newaetech/chipwhisperer-target-cw308t/CW308T_ICE405/README.md

## CE308T-ICE40 Prototype Target

This target was used for internal development.
