newaetech/chipwhisperer-target-cw308t/CW308T_NU8051_AT20/kicad_src/README.md

# N76e003 UFO Target board for the Chipwhisper UFO board

Tested and working, gerbers, BOM, and placement files are in `jlcpcb/`
