newaetech/chipwhisperer-target-cw308t/CW308T_STM32F_SOCKET/gerbers/README.txt

2-Layer PCB

Soldermask: Blue
Silkscreen: White

Finish: Immersion Gold

52.3mm x 64.6mm

Board Files:

 .GTO - Top Silkscreen
 .GTS - Top Soldermask
 .GTL - Top Copper
 .GBL - Bottom Copper
 .GBS - Bottom Soldermask
 .GBO - Bottom Silkscreen
 .GM1 - Board Outline
 .NCDRILL - Drill File

Other Files:

 .GTP - Top Paste (not used - no SMD on top)
 .GBP - Bottom Paste (for stencil)
