newaetech/chipwhisperer-target-cw308t/CW308T_IMXRT1062/gerbers/README.txt

2-Layer PCB

Soldermask: Blue
Silkscreen: White

Finish: ENIG

Individual PCB Size: 52.3mm x 64.6mm

Board Files:

 .GTO - Top Silkscreen
 .GTS - Top Soldermask
 .GTL - Top Copper
 .GBL - Bottom Copper
 .GBS - Bottom Soldermask
 .GBO - Bottom Silkscreen
 .GM1 - PCB Outline
 .NCDRILL - Drill Files

Other Files:

 .GTP - Top Paste (used for stencil)
 .GBP - Bottom Paste (NOT USED)
