newaetech/chipwhisperer-target-cw308t/CW308T_NRF52840/gerbers/README.txt

2-Layer PCB

Soldermask: Blue
Silkscreen: White

Finish: Immersion Gold

Individual PCB Size: 52.3mm x 64.6mm

Trace/Space: 5 mil
Min Drill:   0.3 mm

Board Files:

 .GTO - Top Silkscreen
 .GTS - Top Soldermask
 .GTL - Top Copper
 .GBL - Bottom Copper
 .GBS - Bottom Soldermask
 .GBO - Bottom Silkscreen
 .GM1 - Outline
 .NCDRILL - Drill Files

Other Files:

 .GTP - Top Paste (used for stencil)
 .GBP - Bottom Paste (NOT USED)
