newaetech/chipwhisperer-target-cw308t/CW308T_LPC1343F/gerbers/02/README.txt

2-Layer PCB

Soldermask: Blue
Silkscreen: White

Finish: Immersion Gold

PCB Size: 52.3mm x 64.6mm

Board Files:

 .GTO - Top Silkscreen
 .GTS - Top Soldermask
 .GTL - Top Copper
 .GBL - Bottom Copper
 .GBS - Bottom Soldermask
 .GBO - Bottom Silkscreen
 .GM1 - Outline
 .NCDRILL - Drill File (ROUND & SLOTS IN SEPERATE FILES)

Other Files:

 .GTP - Top Paste (used for stencil)
 .GBP - Bottom Paste (NOT USED)
