newaetech/chipwhisperer-target-cw308t/CW308T_STM32F4_CSP/gerbers/SINGLE_03/README.txt

2-Layer PCB

Soldermask: Blue
Silkscreen: White

4 mil trace/space

Finish: Immersion Gold

54.6mm x 65.7mm

Board Files:

 .GTO - Top Silkscreen
 .GTS - Top Soldermask
 .GTL - Top Copper
 .GBL - Bottom Copper
 .GBS - Bottom Soldermask
 .GBO - Bottom Silkscreen
 .GM1 - Board Outline
 .NCDRILL - Drill File

Other Files:

 .GTP - Top Paste (for stencil)
 .GBP - Bottom Paste (for stencil)
