newaetech/chipwhisperer-target-cw308t/CW308T_AVR/altium_src/gerbers/README.txt

2-Layer PCB

Soldermask: Blue
Silkscreen: White

Finish: RoHS HASL

52.3mm x 68.1mm

Board Files:

 .GTO - Top Silkscreen
 .GTS - Top Soldermask
 .GTL - Top Copper
 .GBL - Bottom Copper
 .GBS - Bottom Soldermask
 .GBO - Bottom Silkscreen
 .GM3 - Board Outline
 .NCDRILL - Drill File

Other Files:

 .GTP - Top Paste (for stencil)
 .GBP - Bottom Paste (for stencil)
