newaetech/chipwhisperer-target-cw308t/CW312T_ATSAM4S/altium_src/RELEASE/gerbers/README.txt

GENERAL
----------
Board Size: 58.7 mm x 53.7 mm
Finish: Immersion Gold
Soldermask: Blue
Silkscreen: White
Board Thickness: 1.6mm

Min drill = 0.3mm
Space/Trace = 6mil

PCB STACKUP:
--------------------------------
 .GTO Top Silkcreen
 .GTS Top Soldermask
 .GTL TOP COPPER               (LAYER 1)
 .GBL BOTTOM COPPER            (LAYER 2)
 .GTS Bottom Soldermask 
 .GBO Bottom Silkscreen

ADDITIONAL FILES:
--------------------------------
 .NCDRILL - NC Drill
 .GTP Top Stencil
 .GBP Bottom Stencil
 .GM1 Milling Layer

BOARD CONSTRUCTION
--------------------------------
Standard board stackup spacing for 2-layer 0.062" PCB
