newaetech/chipwhisperer-target-cw308t/CW308T_ATSAMR21/Images/atsamr21-sch.png

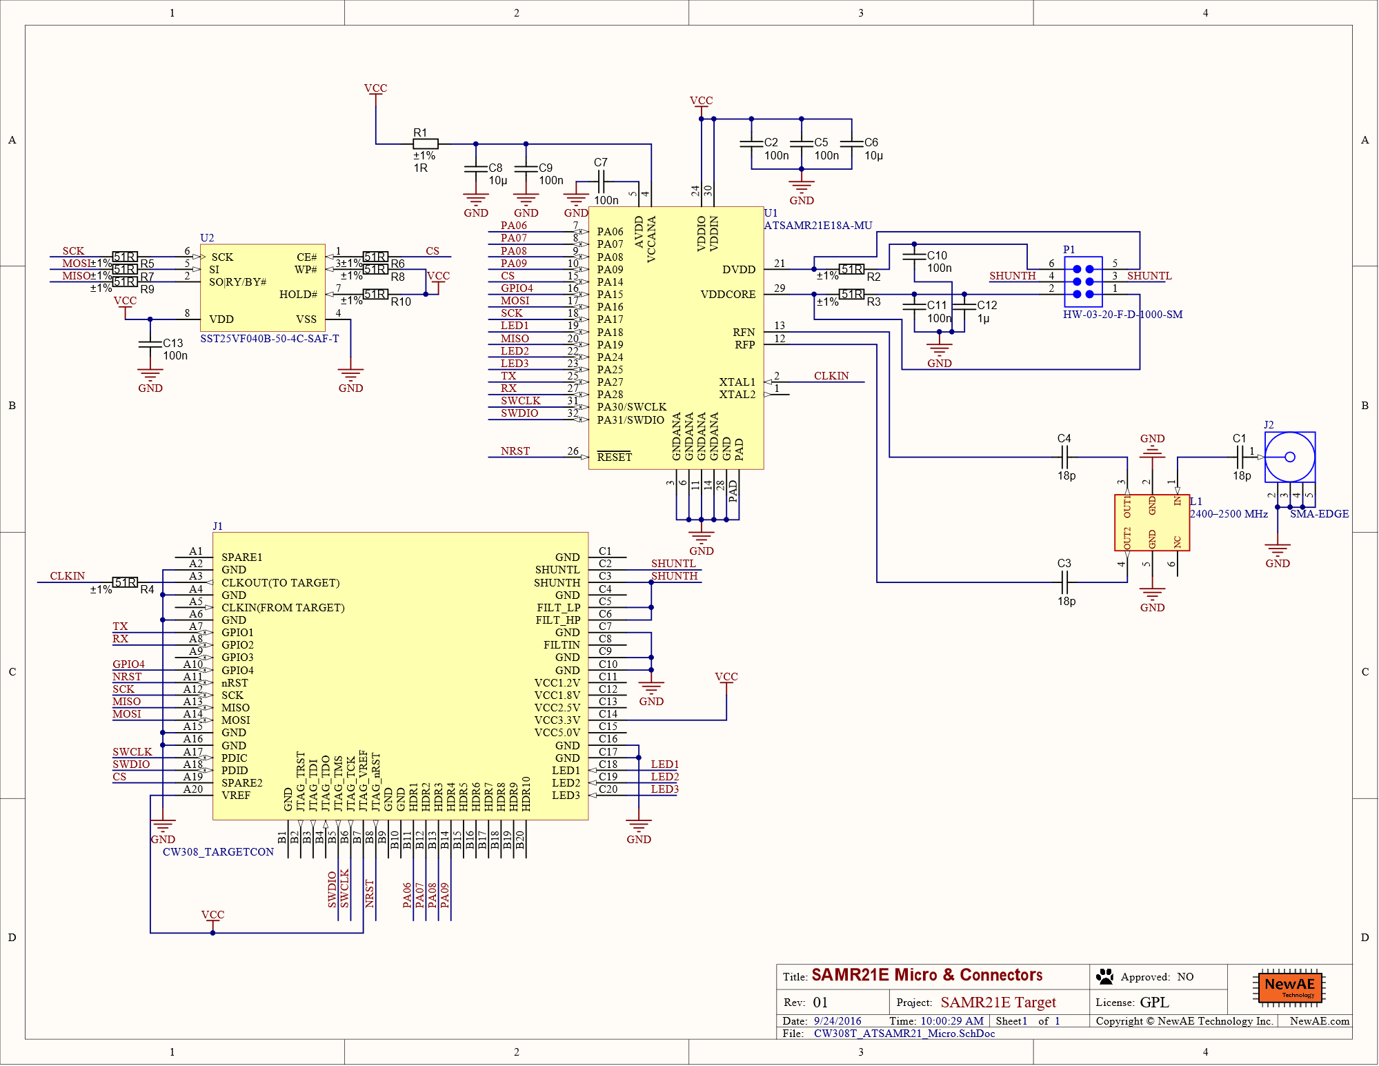
CW308T_ATSAMR21/Images/atsamr21-sch.png
