newaetech/chipwhisperer-target-cw308t/CW308T_Si4010/altium_src/matching_values.png

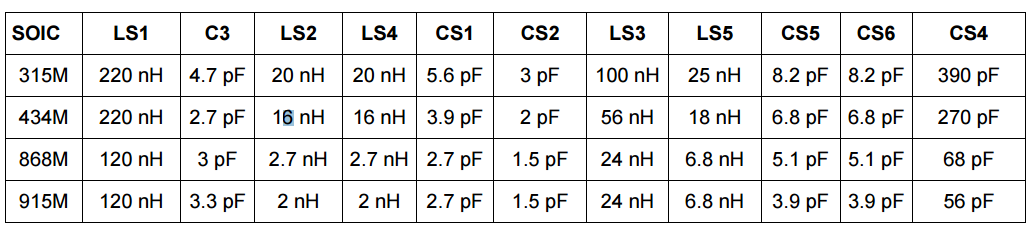
CW308T_Si4010/altium_src/matching_values.png
