newaetech/chipwhisperer-target-cw308t/CW308T_S6LX9/altium_src/PANEL_ORDER/README.txt

GENERAL
----------
Panel Size: 138.78 mm x 114.27 mm
Board Size: 52.3 mm x 64.6 mm
Finish: Immersion Gold
Soldermask: Blue
Silkscreen: White
Board Thickness: 1.6mm

Min drill = 0.3mm
Space/Trace = 6mil

PCB STACKUP:
--------------------------------
 .GTO Top Silkcreen
 .GTS Top Soldermask
 .GTL TOP COPPER               (LAYER 1)
 .GP1 INNER PLANE 1 (NEGATIVE) (LAYER 2)
 .GP2 INNER PLANE 2 (NEGATIVE) (LAYER 3)
 .GBL BOTTOM COPPER            (LAYER 4)
 .GTS Bottom Soldermask
 .GBO Bottom Silkscreen

ADDITIONAL FILES:
--------------------------------
 .NCDRILL - NC Drill
 .GTP Top Stencil
 .GBP Bottom Stencil
 .GM25 - Panel Outline
 .GM18 - VSCORE for Panel

BOARD CONSTRUCTION
--------------------------------
Standard board stackup spacing for 4-layer 0.062" PCB ok

E-TEST
------

PCBs must be 100% electrically tested.
