newaetech/chipwhisperer-target-cw308t/CW308T_87C51/altium_src/RELEASE/-02/NAE-CW308T-87C51 Build Notes.pdf

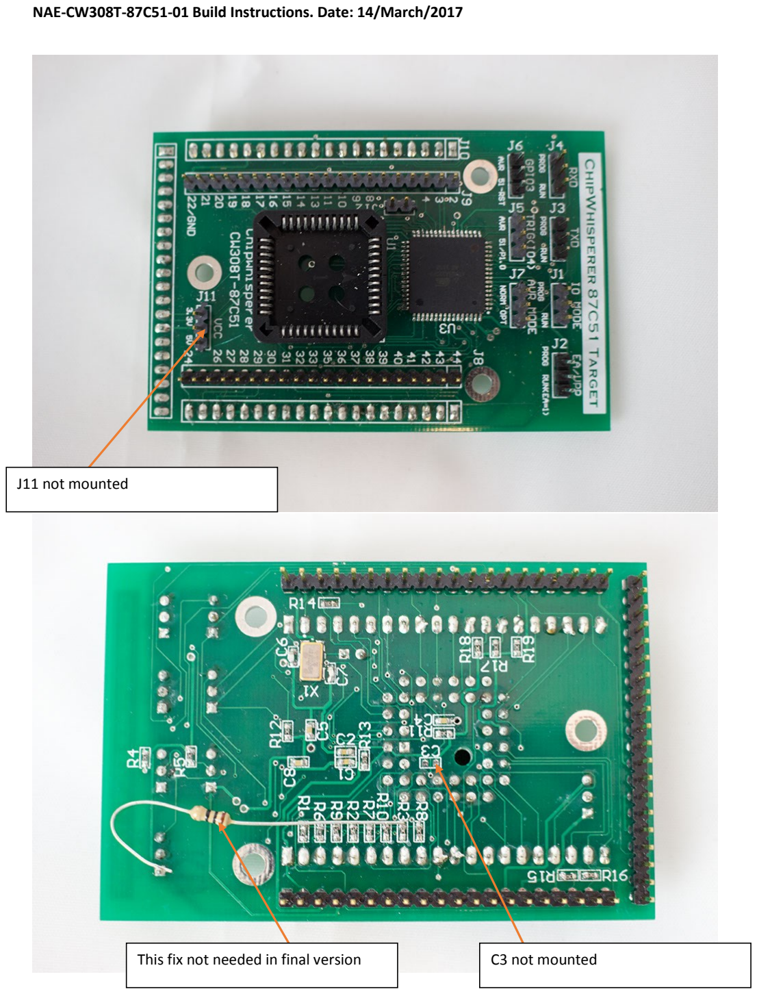
[picture p116: page 1]

NAE-CW308T-87C51-01 Build Instructions. Date: 14/March/2017

J11 not mounted

This fix not needed in final version | C3 not mounted
