newaetech/chipwhisperer-target-cw308t/CW308T_S6LX9/NAE-CW308T-S6LX9_Schematic.PDF

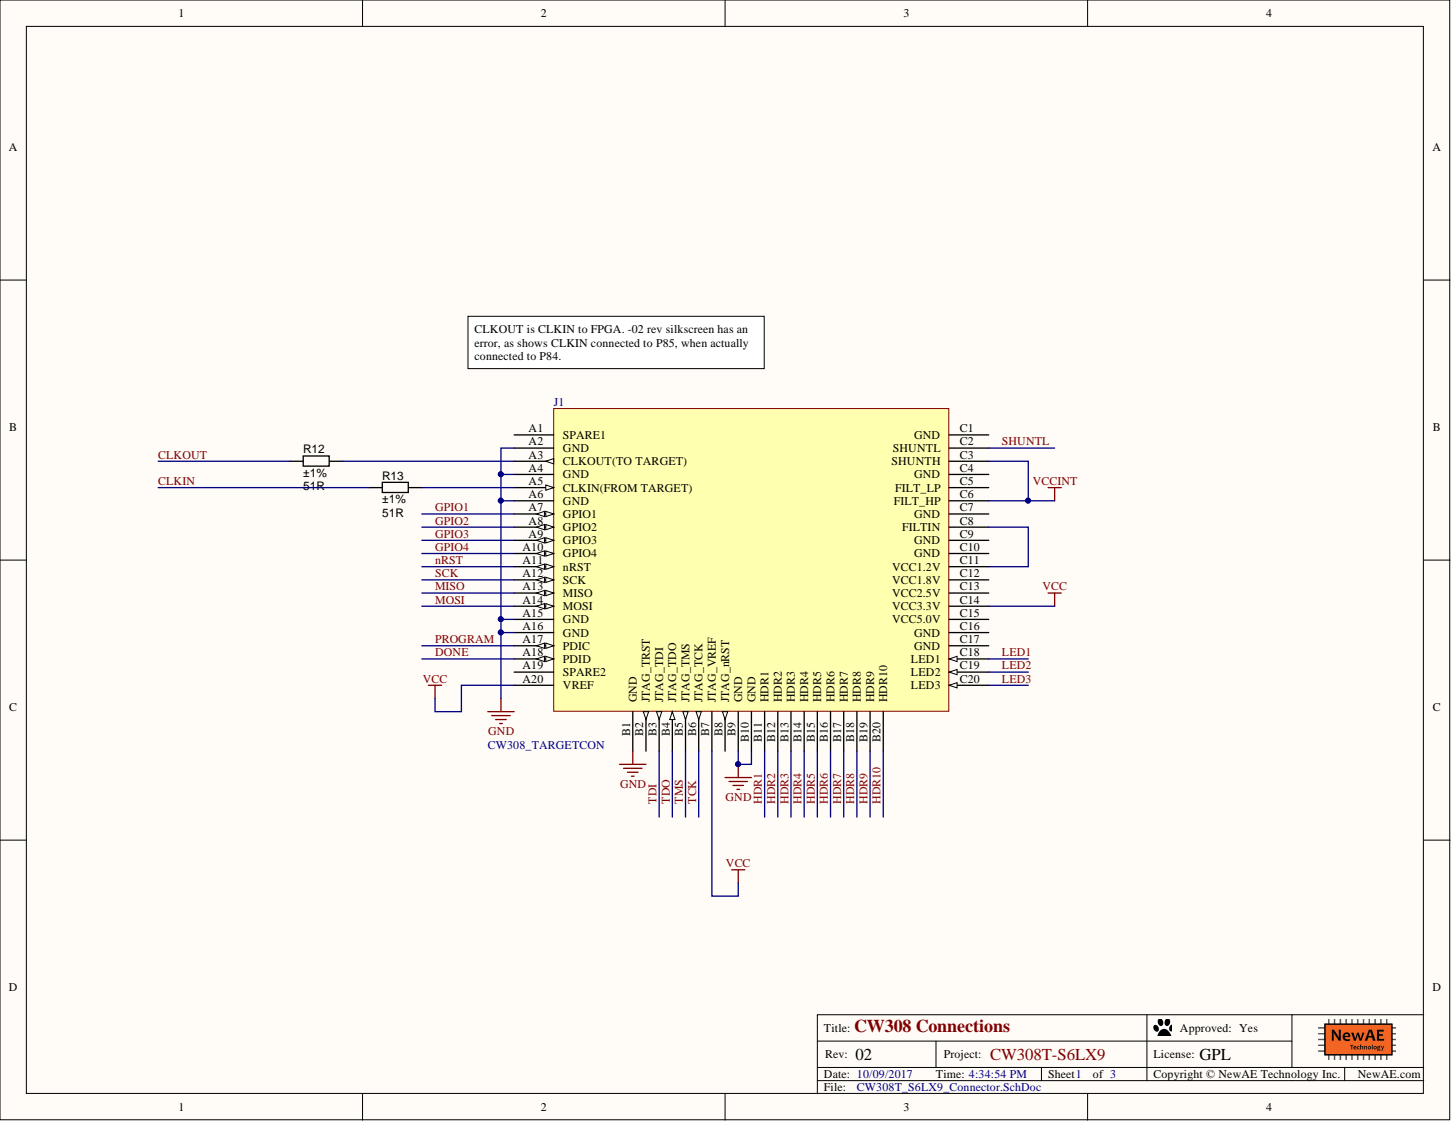
[picture p130: page 1]

CLKOUT is CLKIN to FPGA. -02 rev silkscreen has an
error, as shows CLKIN connected to P85, when actually
connected to P84.

CW308 Connections Title: | Approved: Yes

Rev: 02 | Project: CW308T-S6LX9 | License: GPL

Date: 10/09/2017 Time: 4:34:54 PM | Sheet 1 of 3

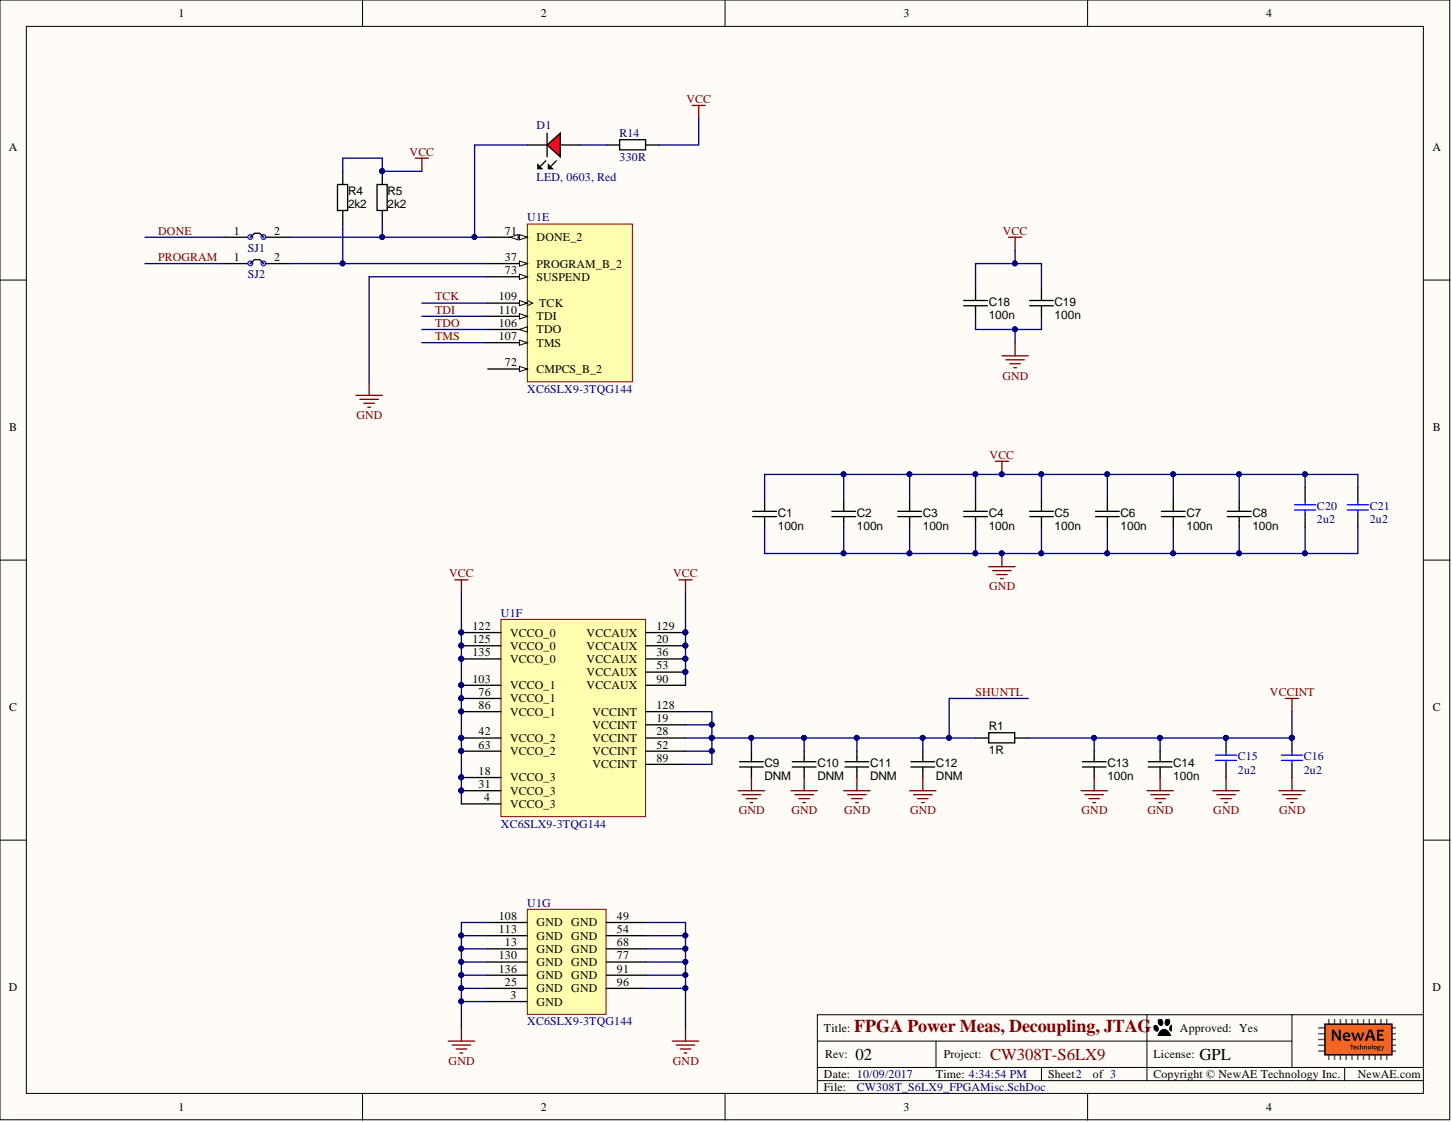
[picture p131: page 2]

FPGA Power Meas, Decoupling, JTAG Title: | Approved: Yes

Rev: 02 | Project: CW308T-S6LX9 | License: GPL

10/09/2017 Time: 4:34:54 PM | Sheet 2 of 3

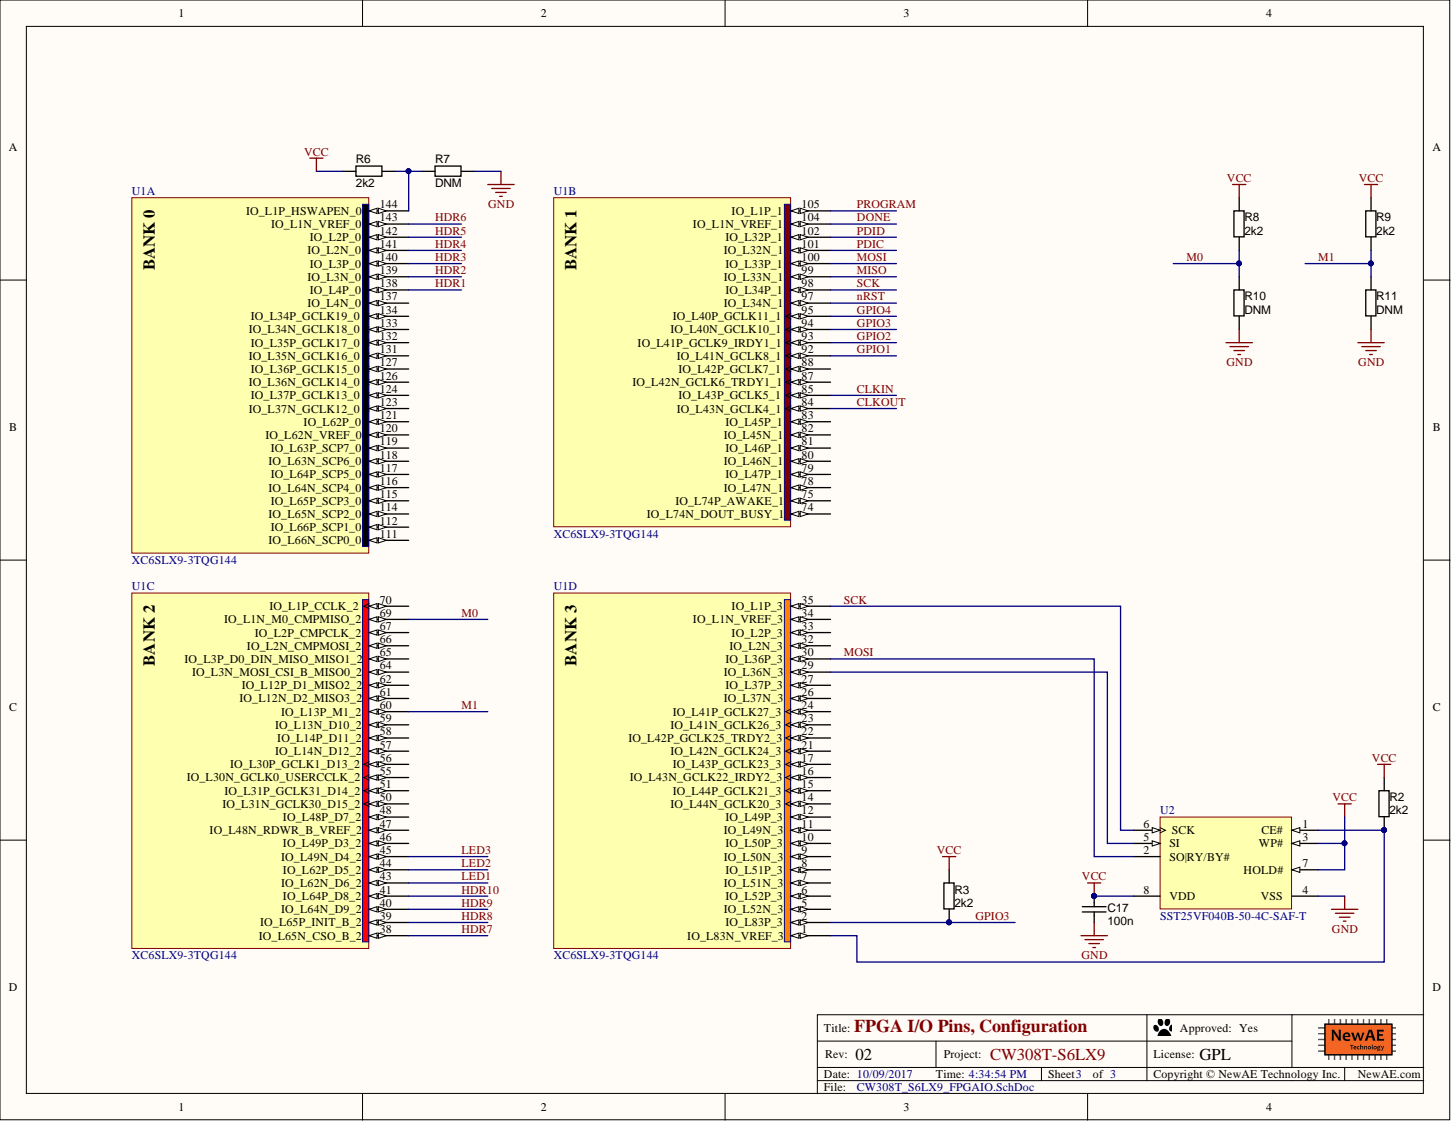
[picture p132: page 3]

9 | VCC | 2 | | 7

FPGA I/O Pins, C onfiguratio n T i t le: | A p pro ved : Yes

Rev : 02 | Project : CW308T-S6LX | L icen se: GPL

/ / T ime: : : 4 PM | Sheet o f | Co p yri g h t © New A E Tech n | o l o g y Inc.
