newaetech/chipwhisperer-target-cw308t/CW312T_RP2350/RP2350_CW312_REV02.PDF

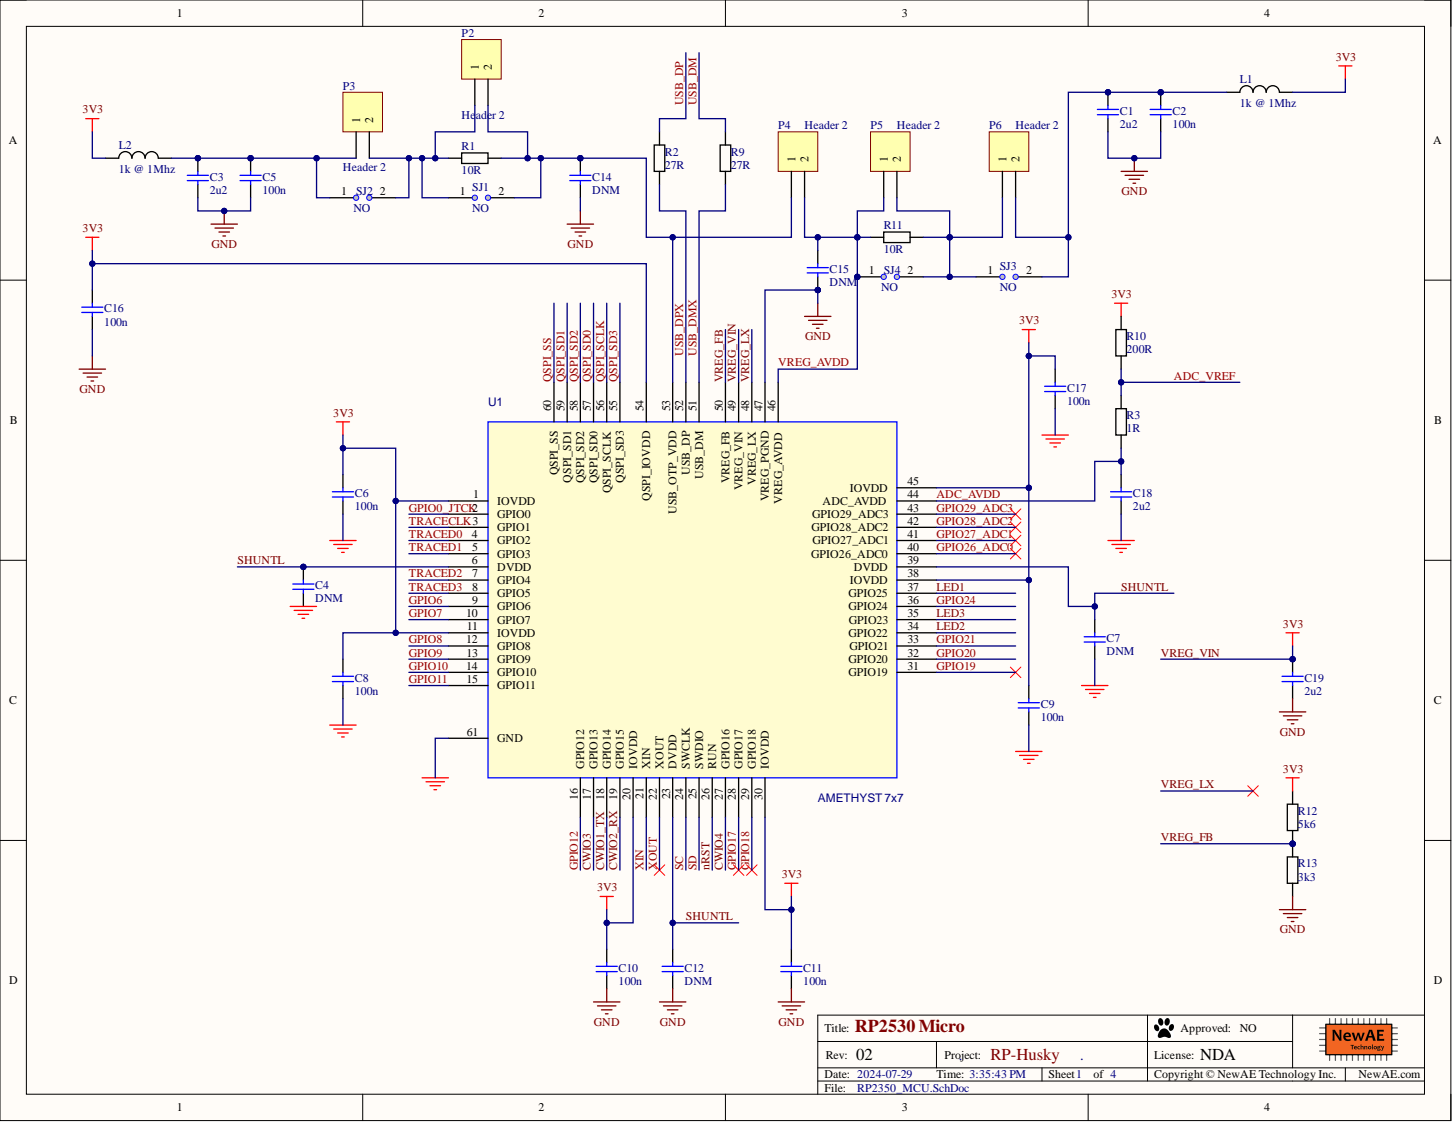
[picture p133: page 1]

ADC_AVDD

GPIO0_JTCK | GPIO0 2 | GPIO29_ADC3

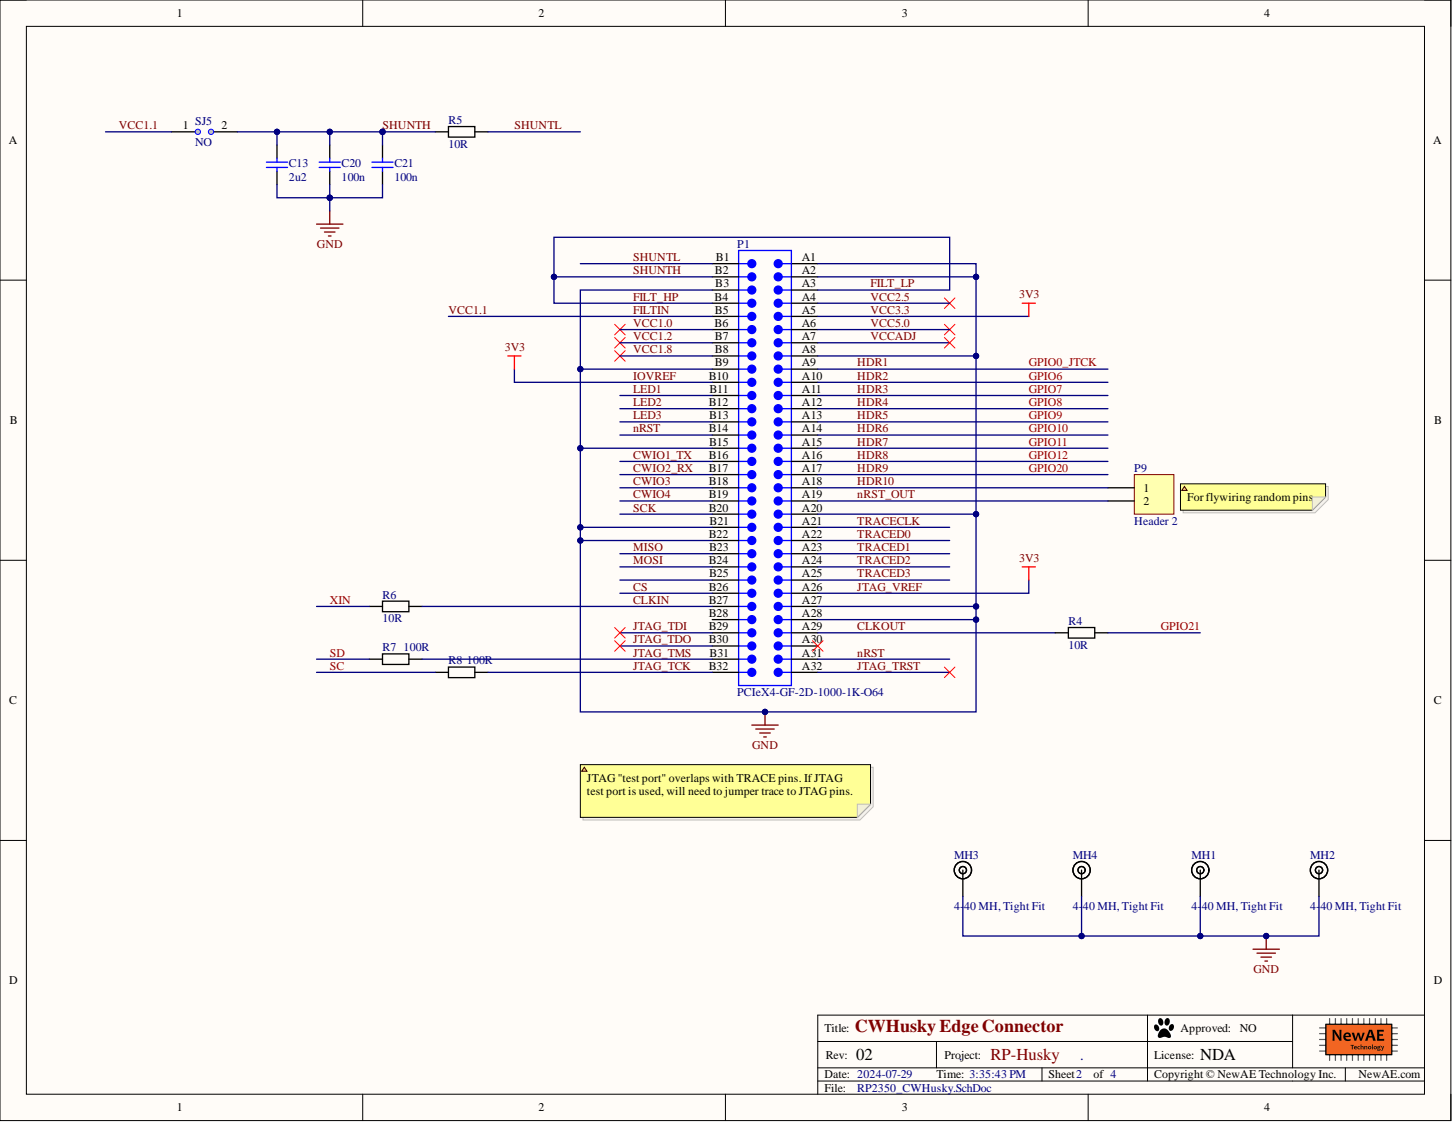
[picture p134: page 2]

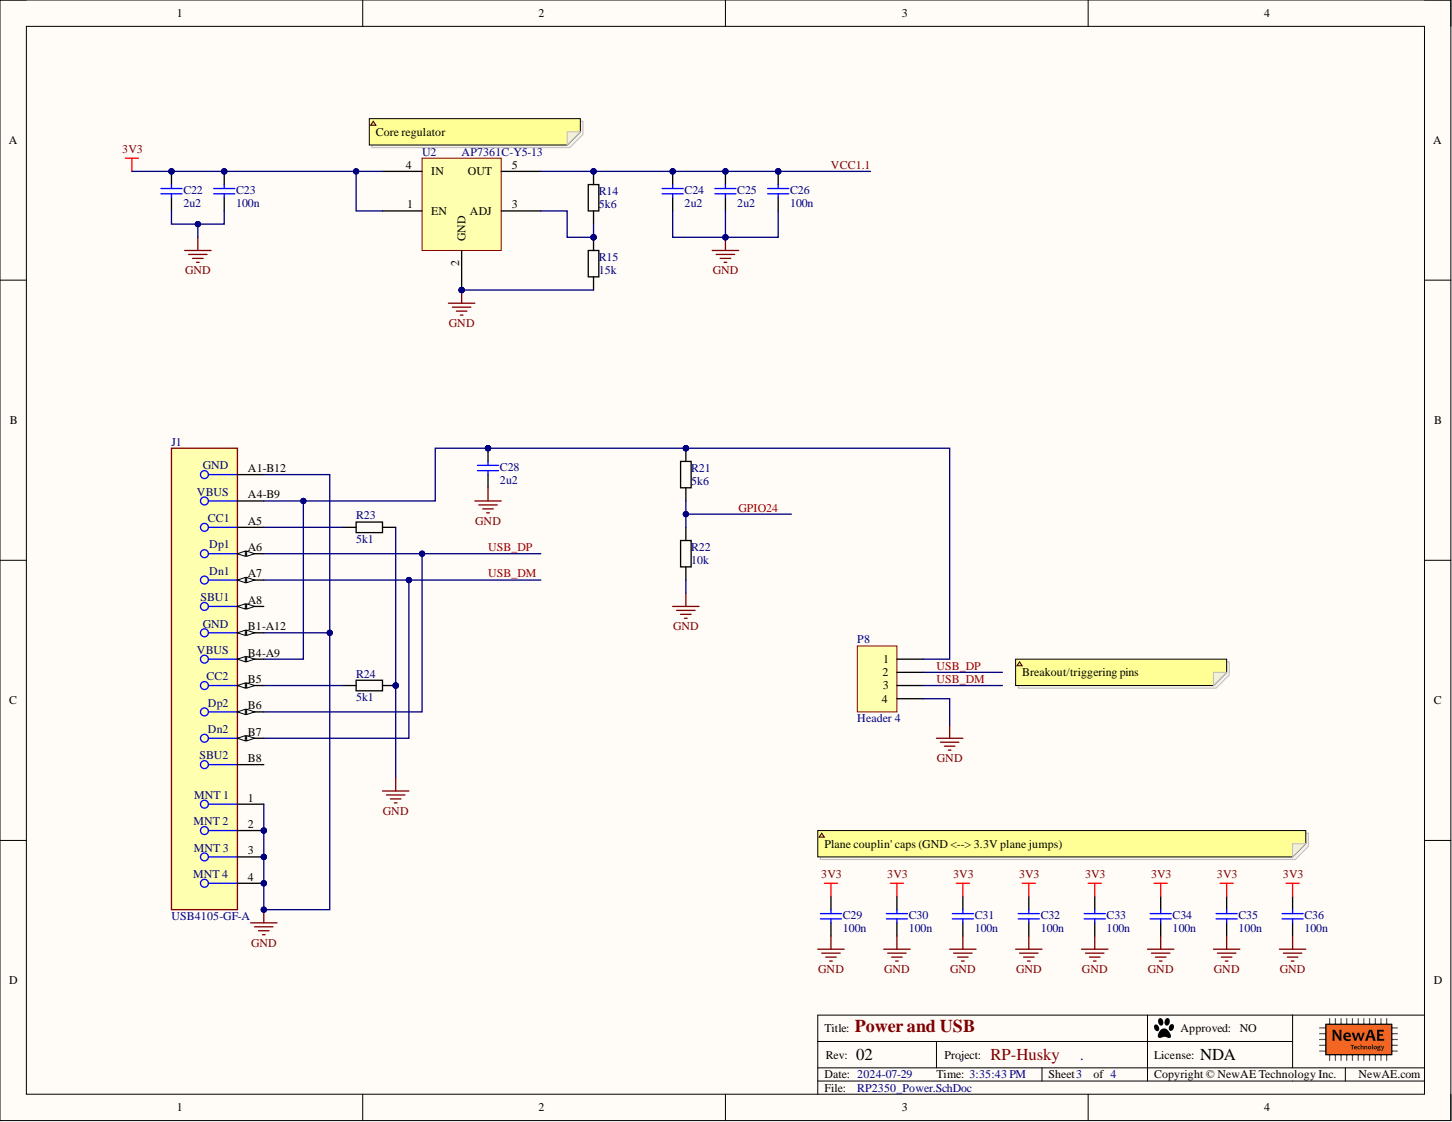
[picture p135: page 3]

Plane couplin' caps (GND <--> 3.3V plane jumps)

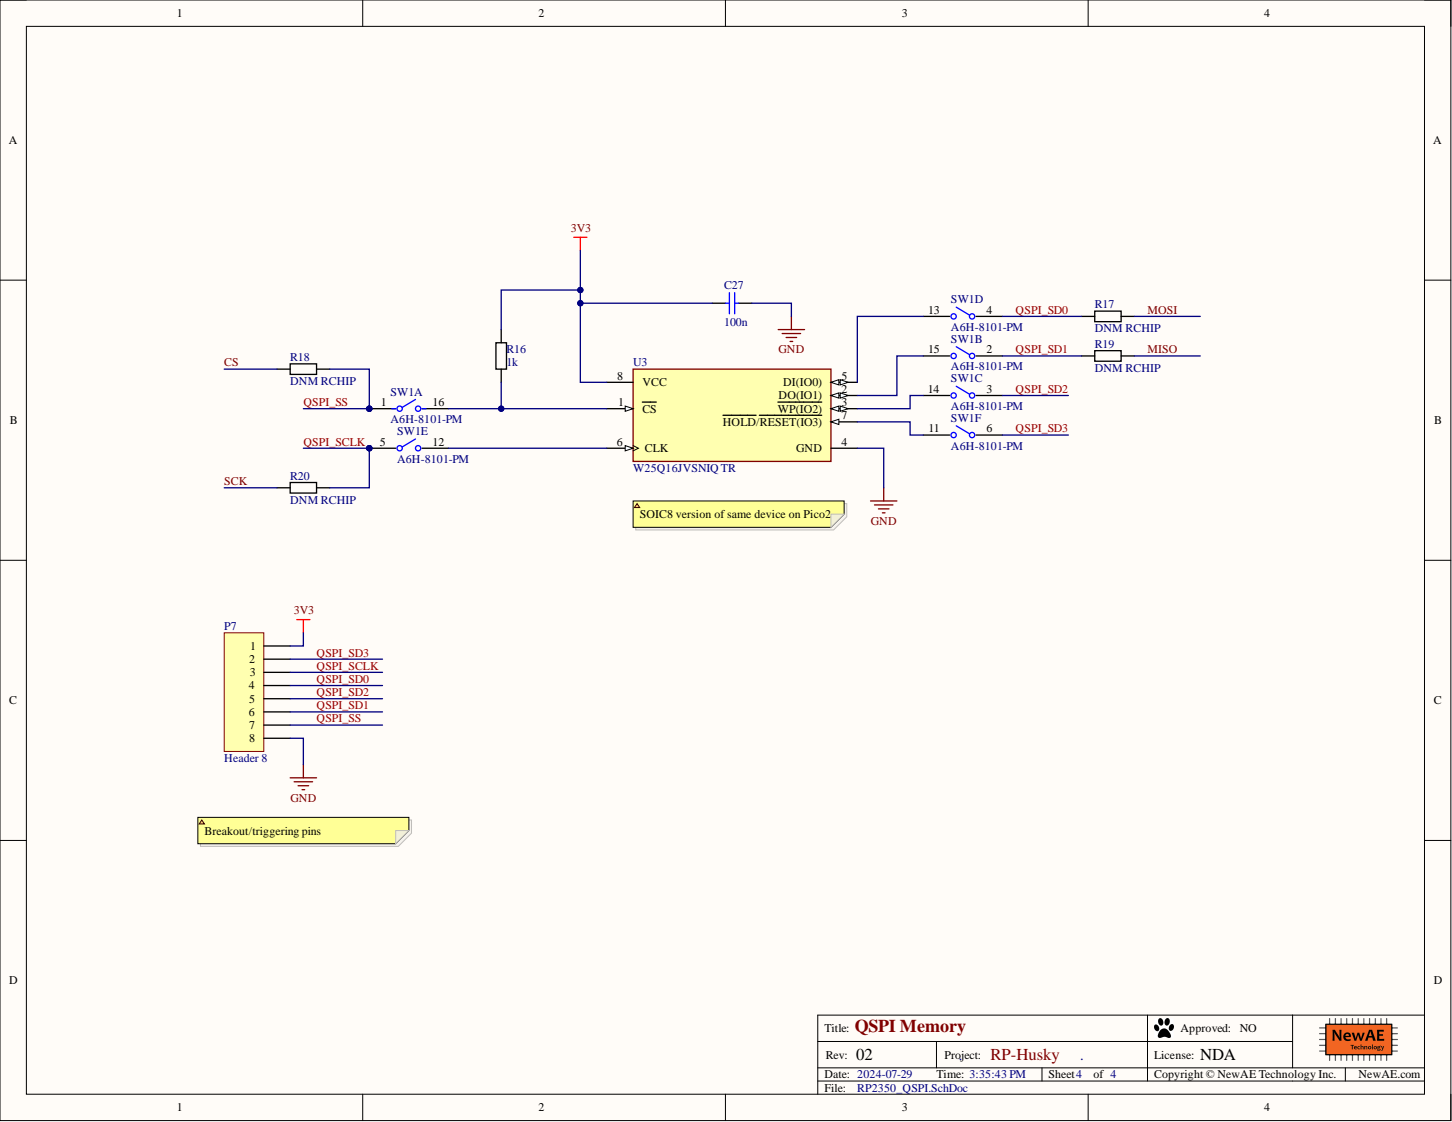
[picture p136: page 4]

SOIC8 version of same device on Pico2
