newaetech/chipwhisperer-target-cw308t/CW308T_STM32F_SOCKET/NAE_CW308T_STM32F_SOCKET.PDF

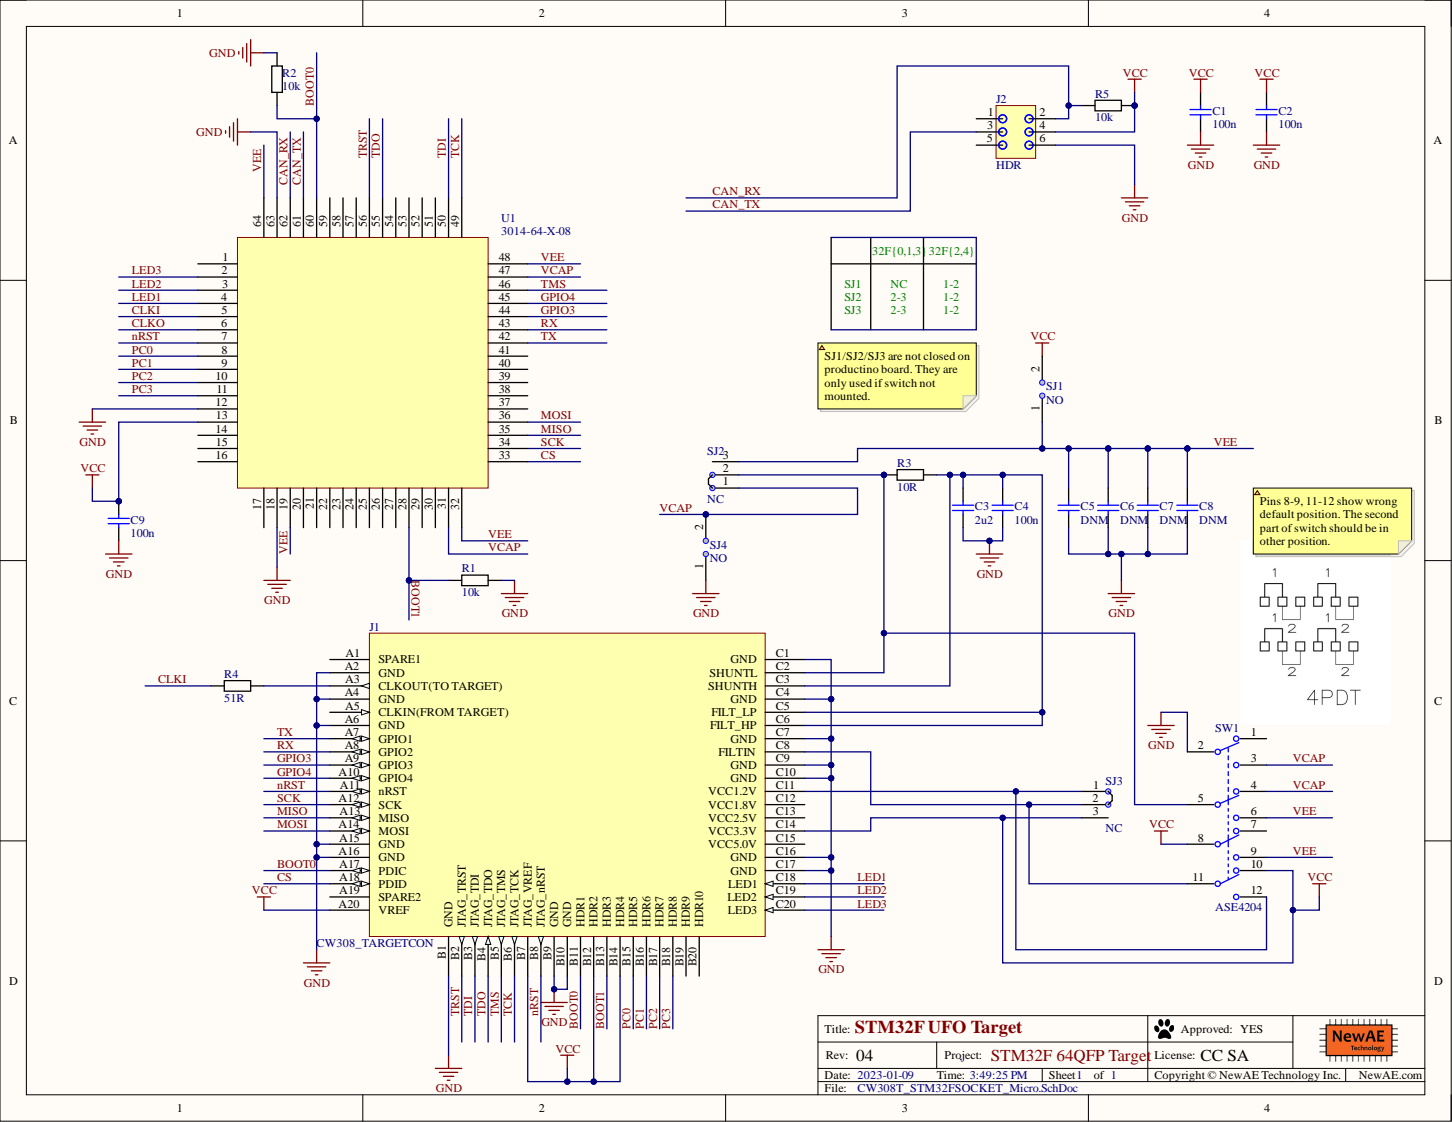
[picture p137: page 1]

SJ1/SJ2/SJ3 are not closed on
productino board. They are
only used if switch not
mounted.

15 | 34 SCK
16 | 33 CS

Pins 8-9, 11-12 show wrong
default position. The second
part of switch should be in
other position.

VEE
