newaetech/chipwhisperer-target-cw308t/CW308T_ICE405/CW308T-ICE40-PROTO.PDF

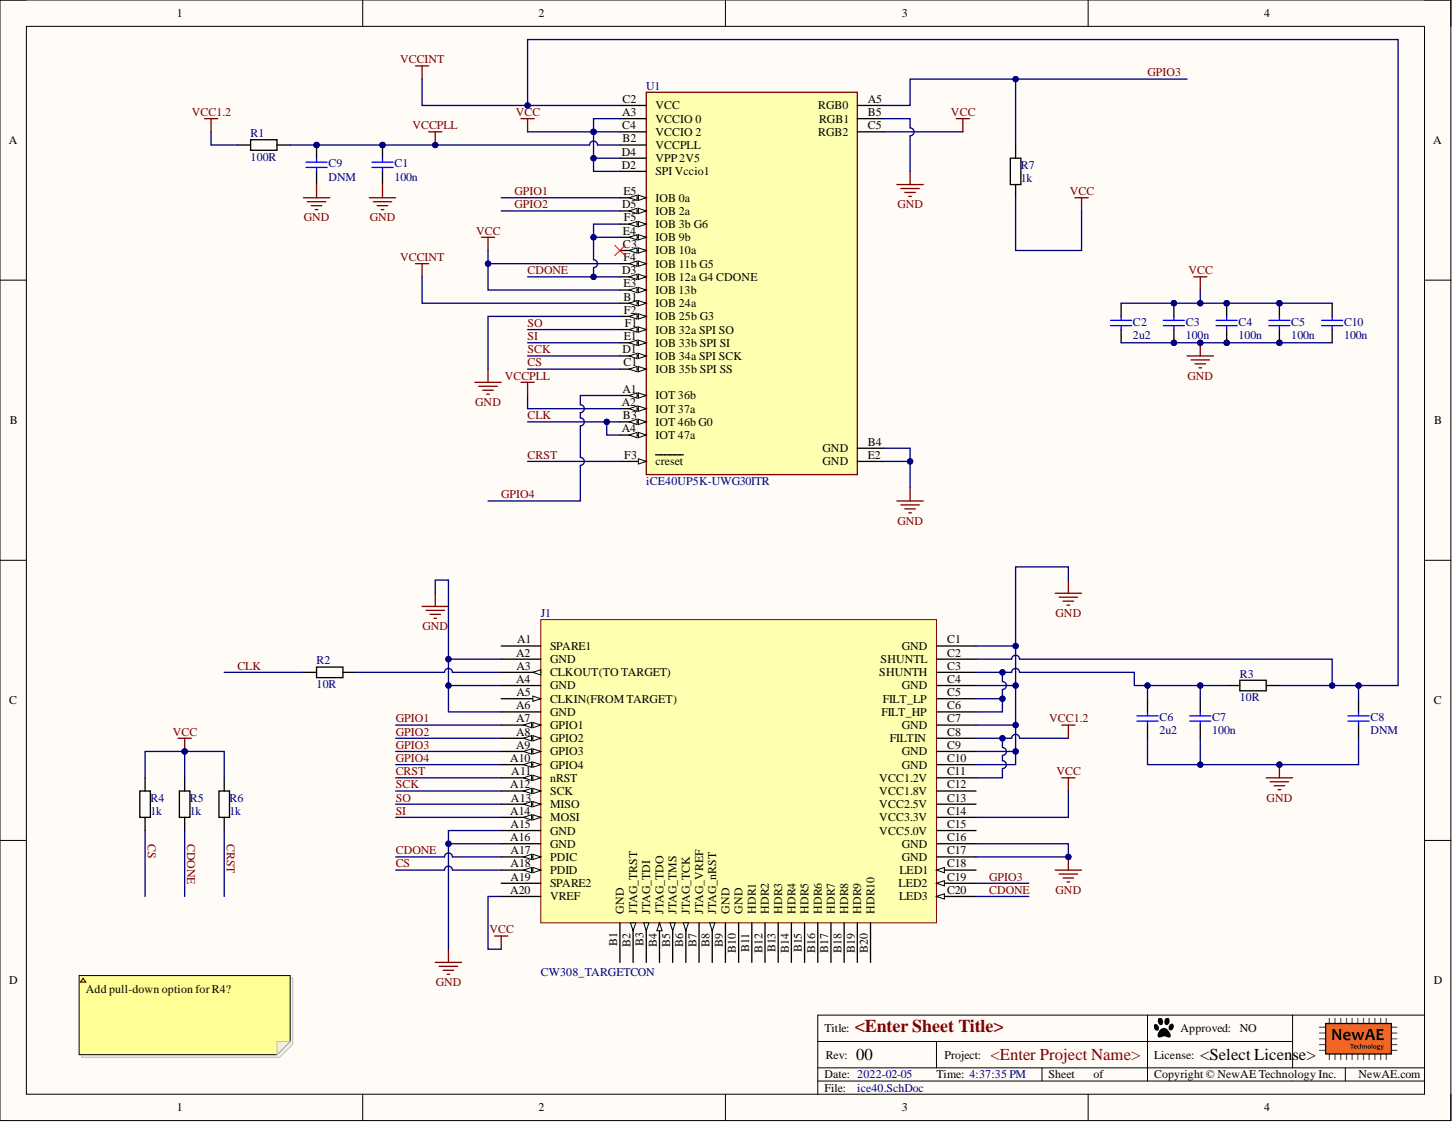
[picture p138: page 1]

VCCIO 0 A3 | VCC
VCCIO 2 C4
VCCPLL B2
SPI Vccio1 D2 VPP 2V5 D4

IOB 9b E4
IOB 10a C3
IOB 11b G5 F4

CDONE | | IOB 12a G4 CDONE D3

IOB 13b E3

PDIC A17

SPARE2 A19

Add pull-down option for R4?
