newaetech/chipwhisperer-target-cw308t/CW308T_STM32F4_CSP/NAE-CW308T-STM32F415WLCSP_03.PDF

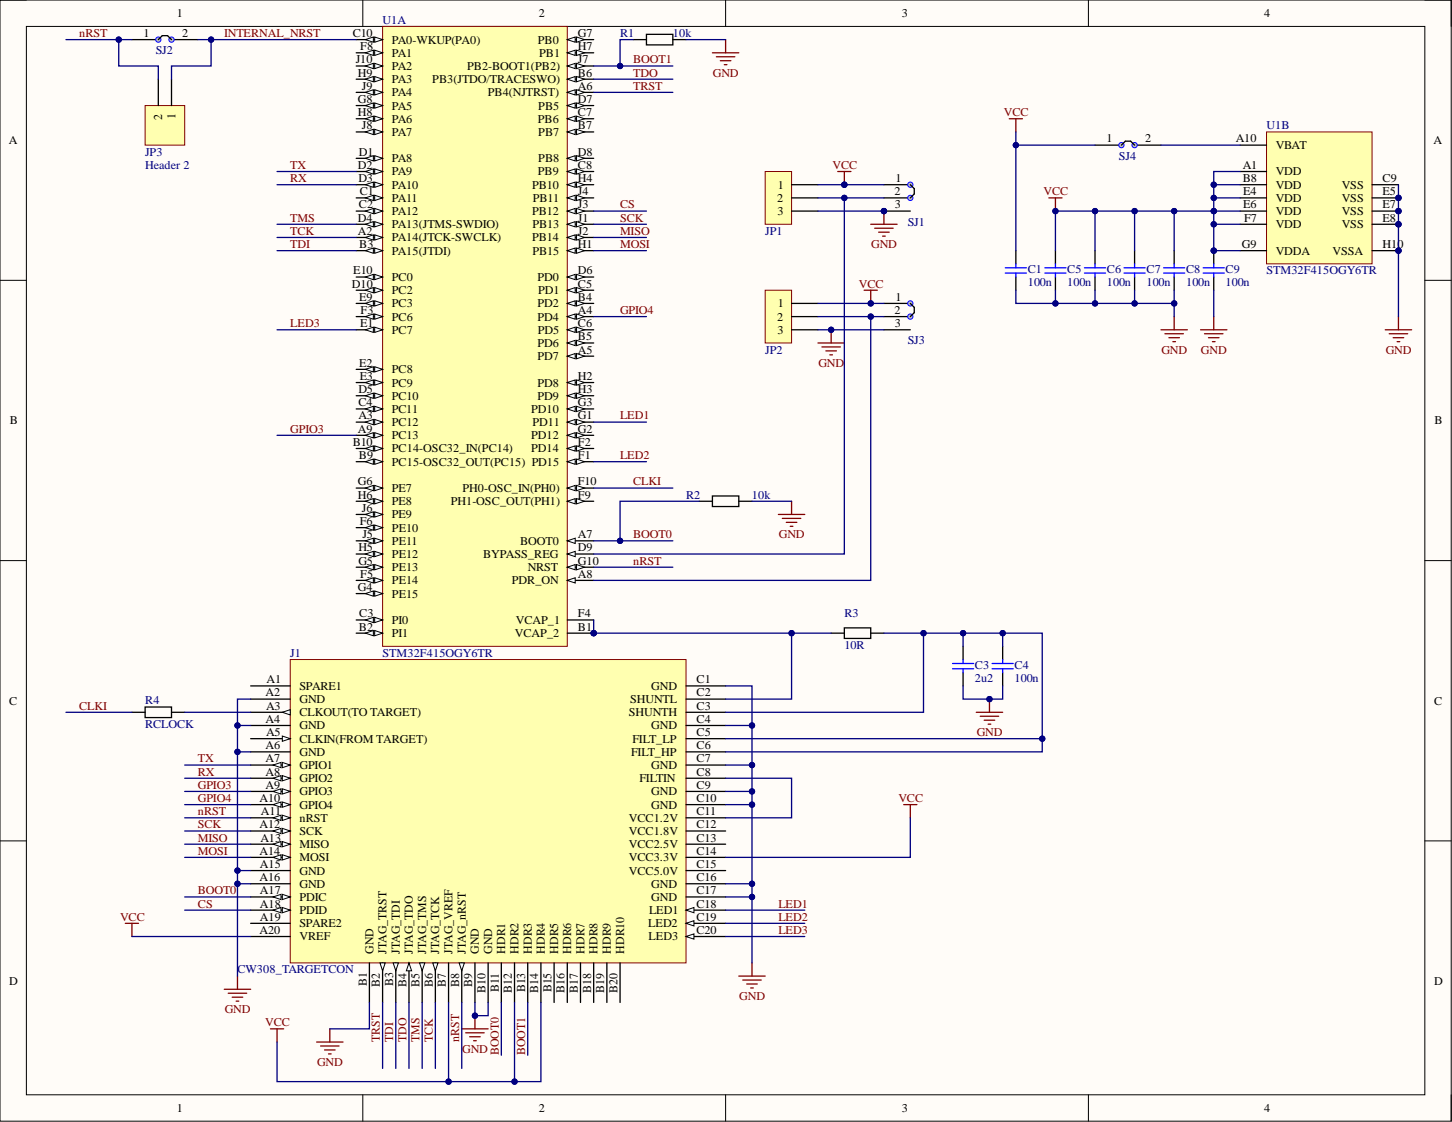
[picture p139: page 1]

PA14(JTCK-SWCLK) A2 | MISO JP1
PA15(JTDI) B3 | MOSI

LED1 | 3 | 3

PC8 E2 PC9 E3 PC11 C4 PC12 A3 PC13 A9 | | GND
