newaetech/chipwhisperer-target-cw308t/CW308T_STM32F/CW308T_STM32F_03.PDF

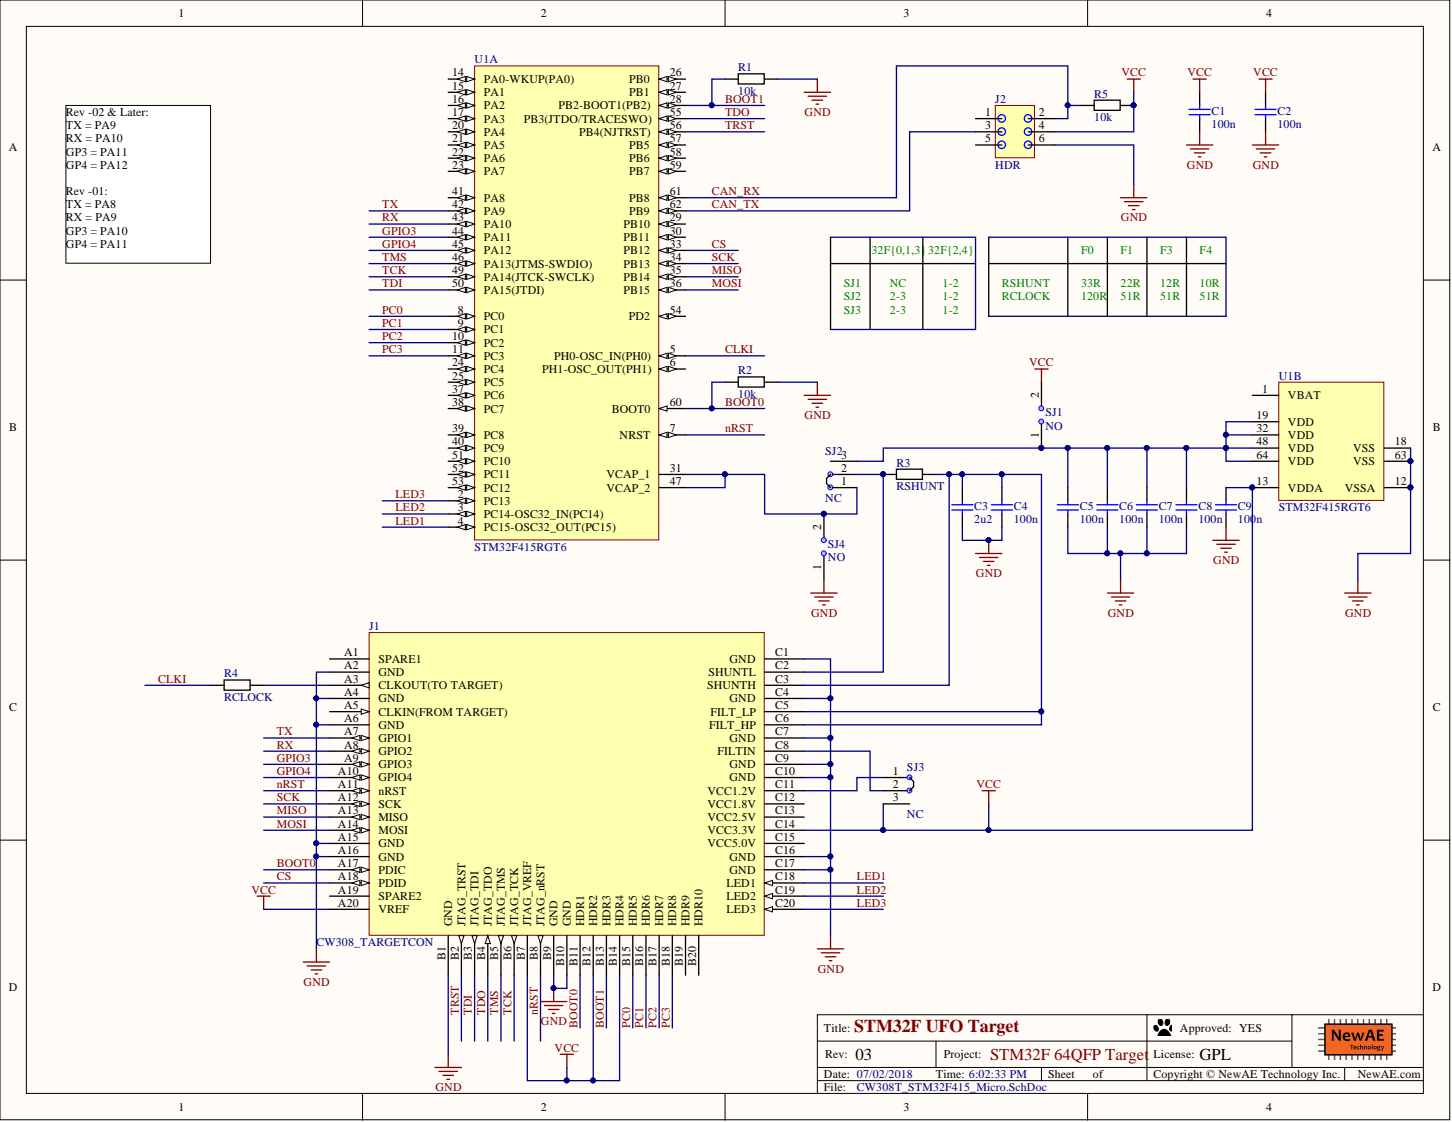
[picture p140: page 1]

STM32F UFO Target Title: | Approved: YES

Rev: 03 | Project: STM32F 64QFP Target License: GPL

Date: 07/02/2018 Time: 6:02:33 PM | Sheet of
