newaetech/chipwhisperer-target-cw308t/CW308T_ADuCM3029/NAE-CW308T-ADuCM3029_Schematic.PDF

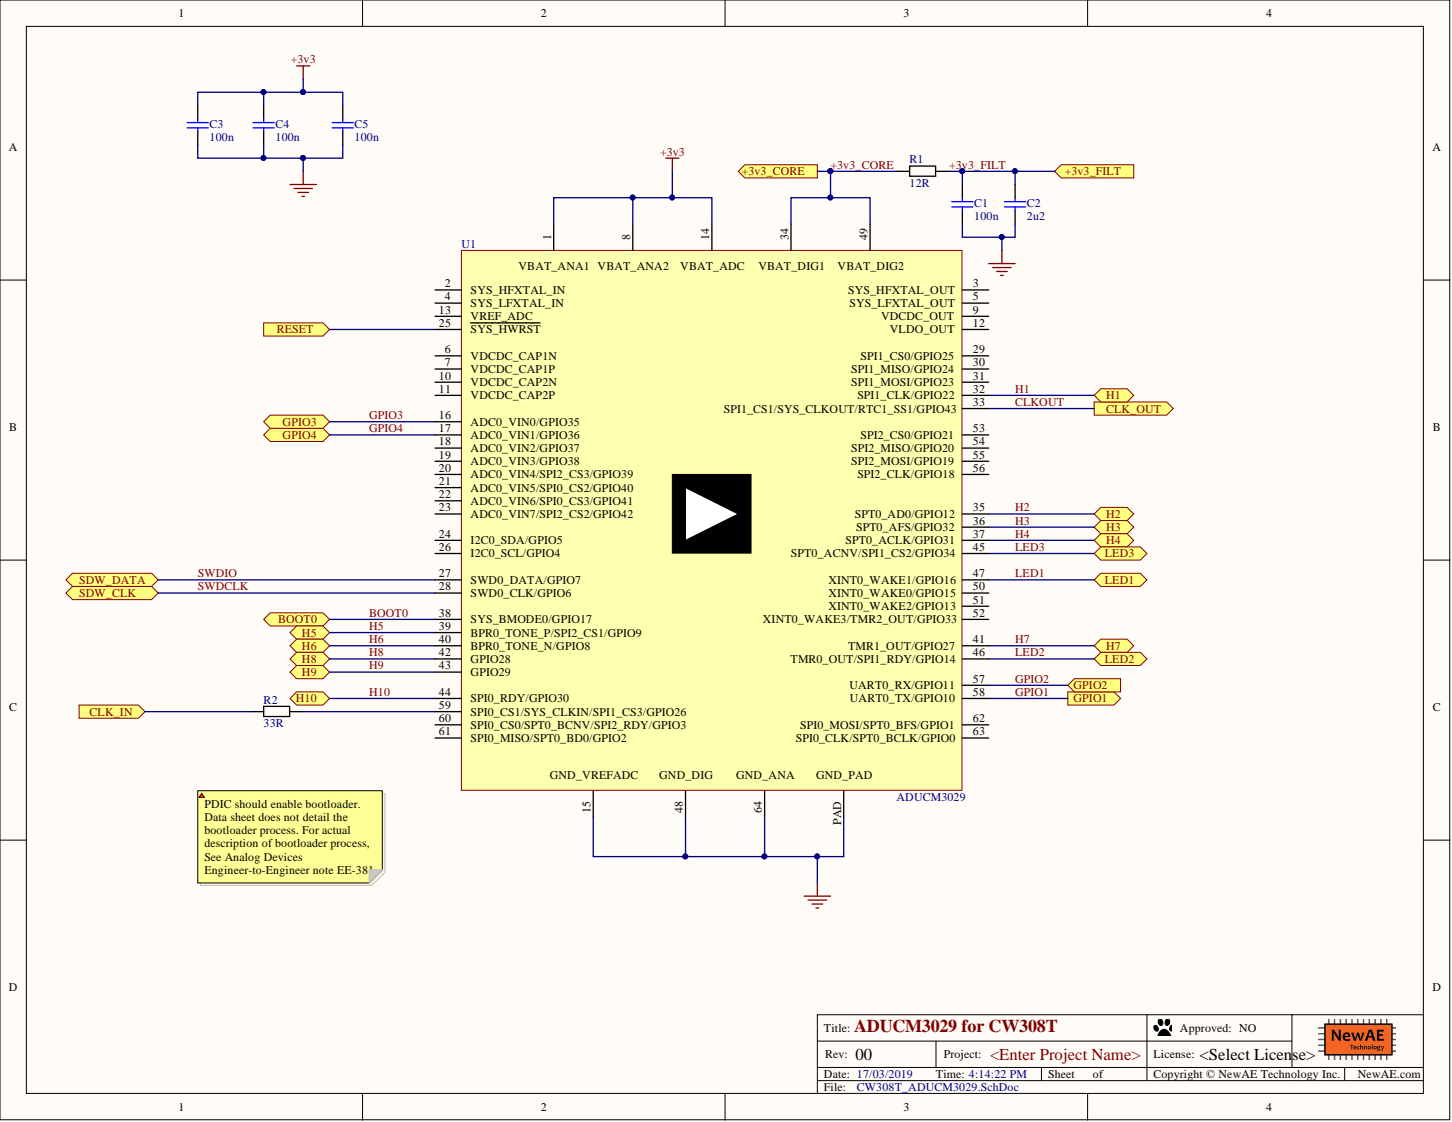
[picture p151: page 1]

PDIC should enable bootloader.
Data sheet does not detail the
bootloader process. For actual
description of bootloader process,
See Analog Devices
Engineer-to-Engineer note EE-381

ADUCM3029 for CW308T Title: | Approved: NO

Rev: 00 | Project: <Enter Project Name> | License: <Select License>

Date: 17/03/2019 Time: 4:14:22 PM | Sheet of

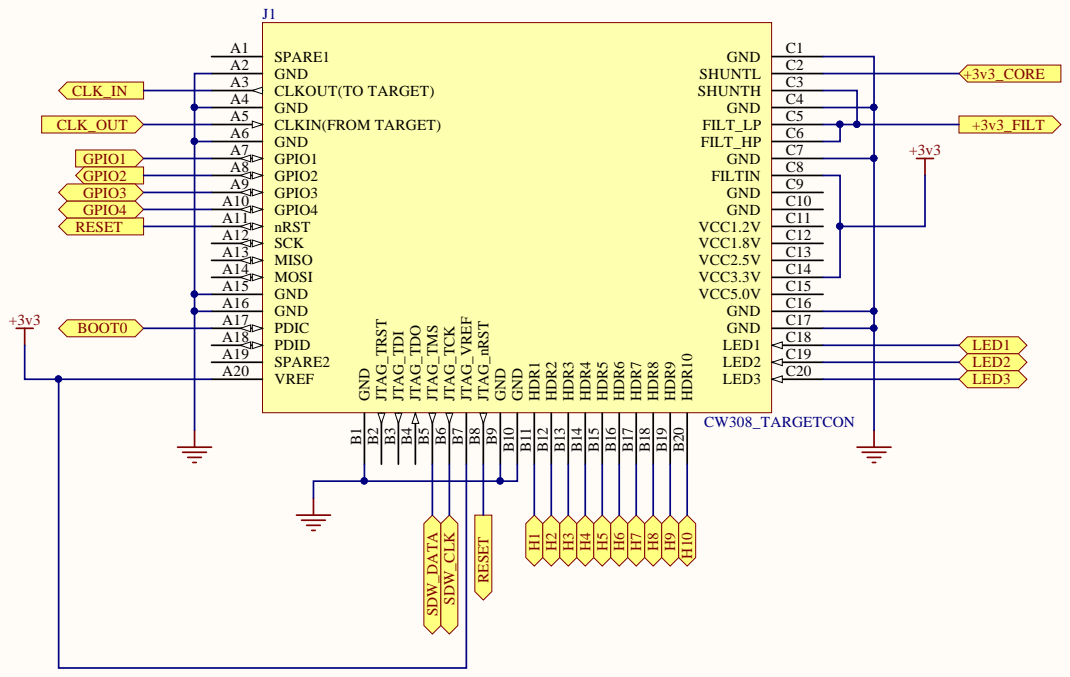
[picture p152: page 2]

PDIC A17 PDID A18

SPARE2 A19

<Enter Sheet Title> Title: | Approved: NO

Rev: 00 | Project: <Enter Project Name> | License: <Select License>

Date: 17/03/2019 Time: 4:14:22 PM | Sheet of
