newaetech/chipwhisperer-target-cw308t/CW308T_ATSAM4L/NAE-CW308T-ATSAM4L-02_Schematic.PDF

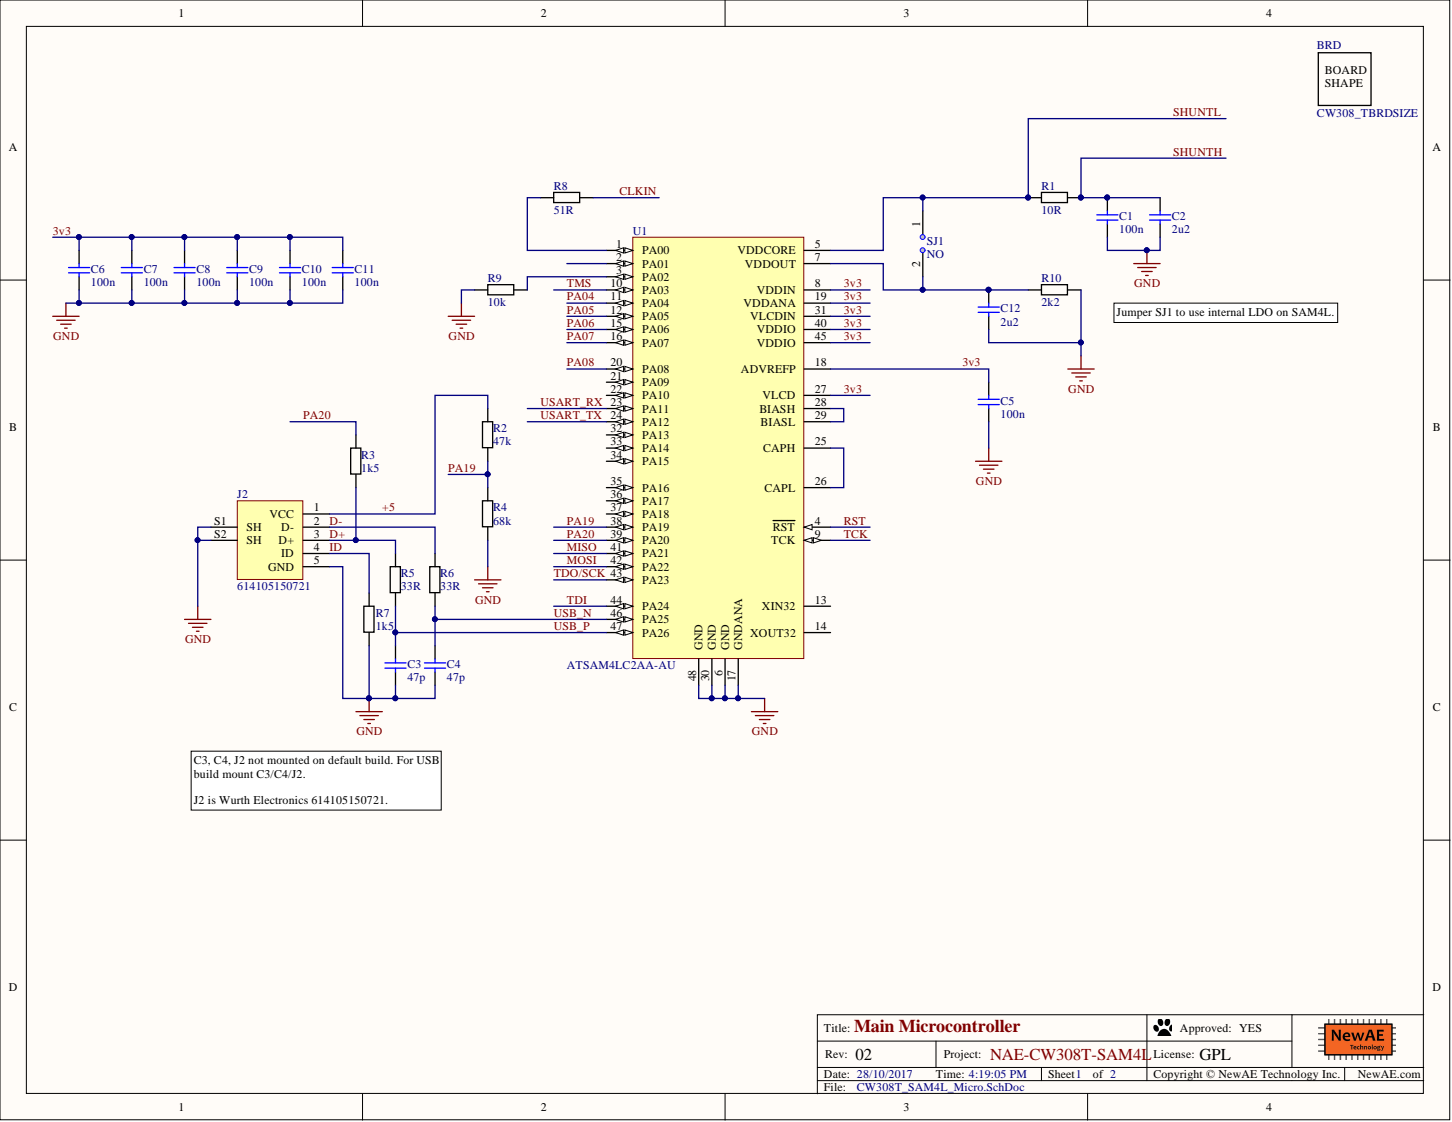
[picture p153: page 1]

USB_ N | 4 6
USB_ P | 4 7

M ain Microcontroller T i t le: | A p pro ved : Y E S

Rev : 02 | Project : N AE-CW308T-SAM4L | L icen se: GPL

Date: 2 8 / 1 0 / 2 0 1 7 T ime: 4 : 1 9 : 0 5 PM | Sheet 1 o f 2 | Co p yri g h t © New A E Tech n | o l o g y Inc.

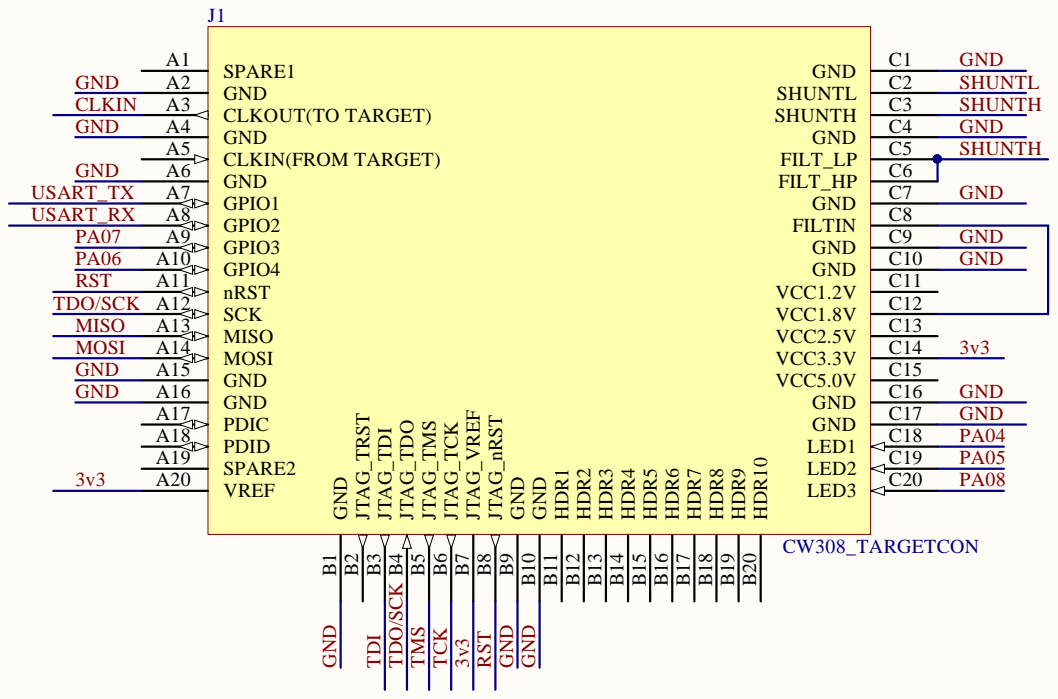
[picture p154: page 2]

UFO C onnections T i t le: | A p pro ved : Y E S

Rev : 02 | Project : N AE-CW308T-SAM4L | L icen se: GPL

Date: 2 8 / 1 0 / 2 0 1 7 T ime: 4 : 1 9 : 0 5 PM | Sheet 2 o f 2 | Co p yri g h t © New A E Tech n | o l o g y Inc.
