newaetech/chipwhisperer-target-cw308t/CW308T_AVR/NAE-CW308T-AVR-02_Schematic.PDF

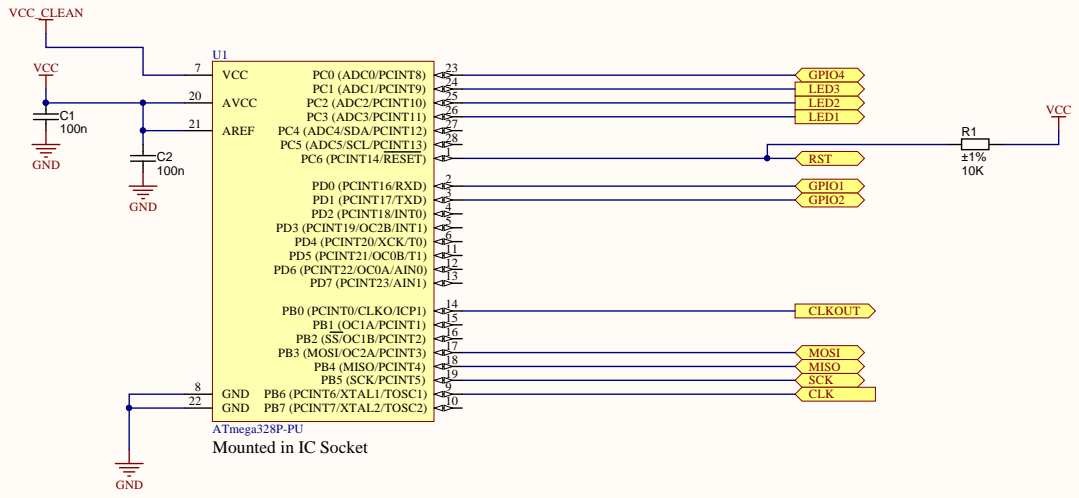
[picture p155: page 1]

A V R Microcontroller T i t le: | A p pro ved : Y E S

Rev : 02 | Project : CW308T-A V R | L icen se: GPL

Date: 9 / 2 1 / 2 0 1 6 T ime: 1 0 : 4 6 : 0 9 A M | Sheet 1 o f 2 | Co p yri g h t © New A E Tech n | o l o g y Inc.

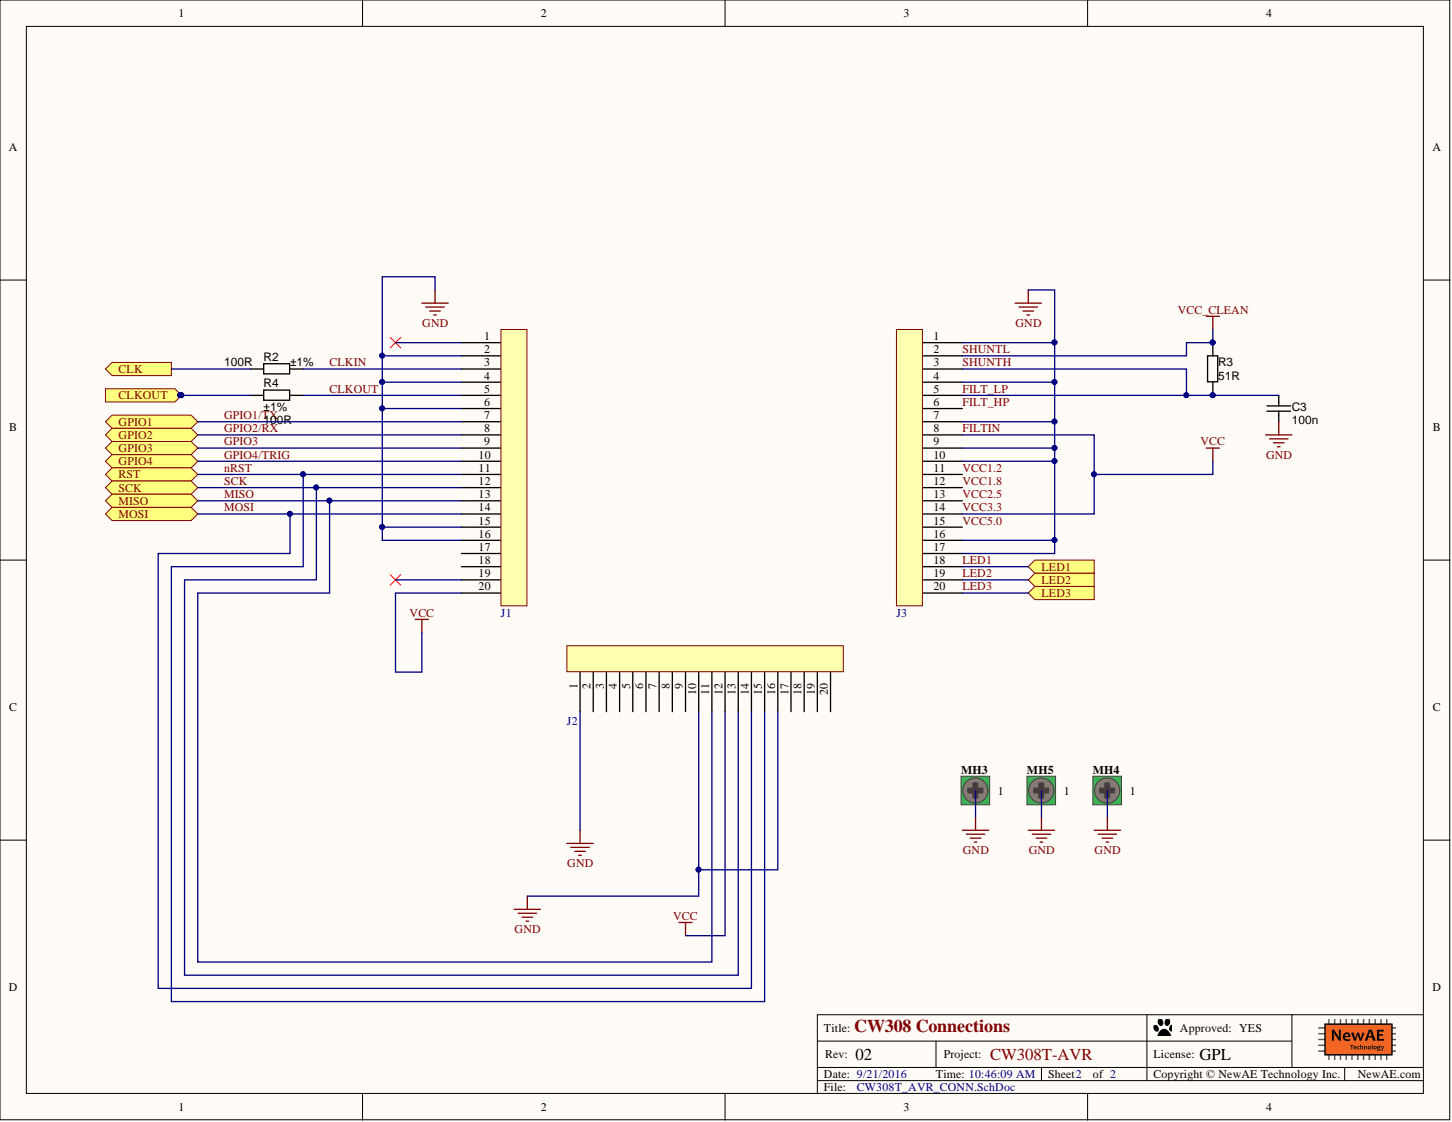
[picture p156: page 2]

SH U N T L
SH U N T H

FIL T _ L P
FIL T _ H P

FIL TIN

CW3 0 8 C onnections T i t le: | A p pro ved : Y E S

Rev : 02 | Project : CW308T-A V R | L icen se: GPL

Date: 9 / 2 1 / 2 0 1 6 T ime: 1 0 : 4 6 : 0 9 A M | Sheet 2 o f 2 | Co p yri g h t © New A E Tech n | o l o g y Inc.
