newaetech/chipwhisperer-target-cw308t/CW308T_CC2538/NAE-CW308T-CC2538_Schematic.PDF

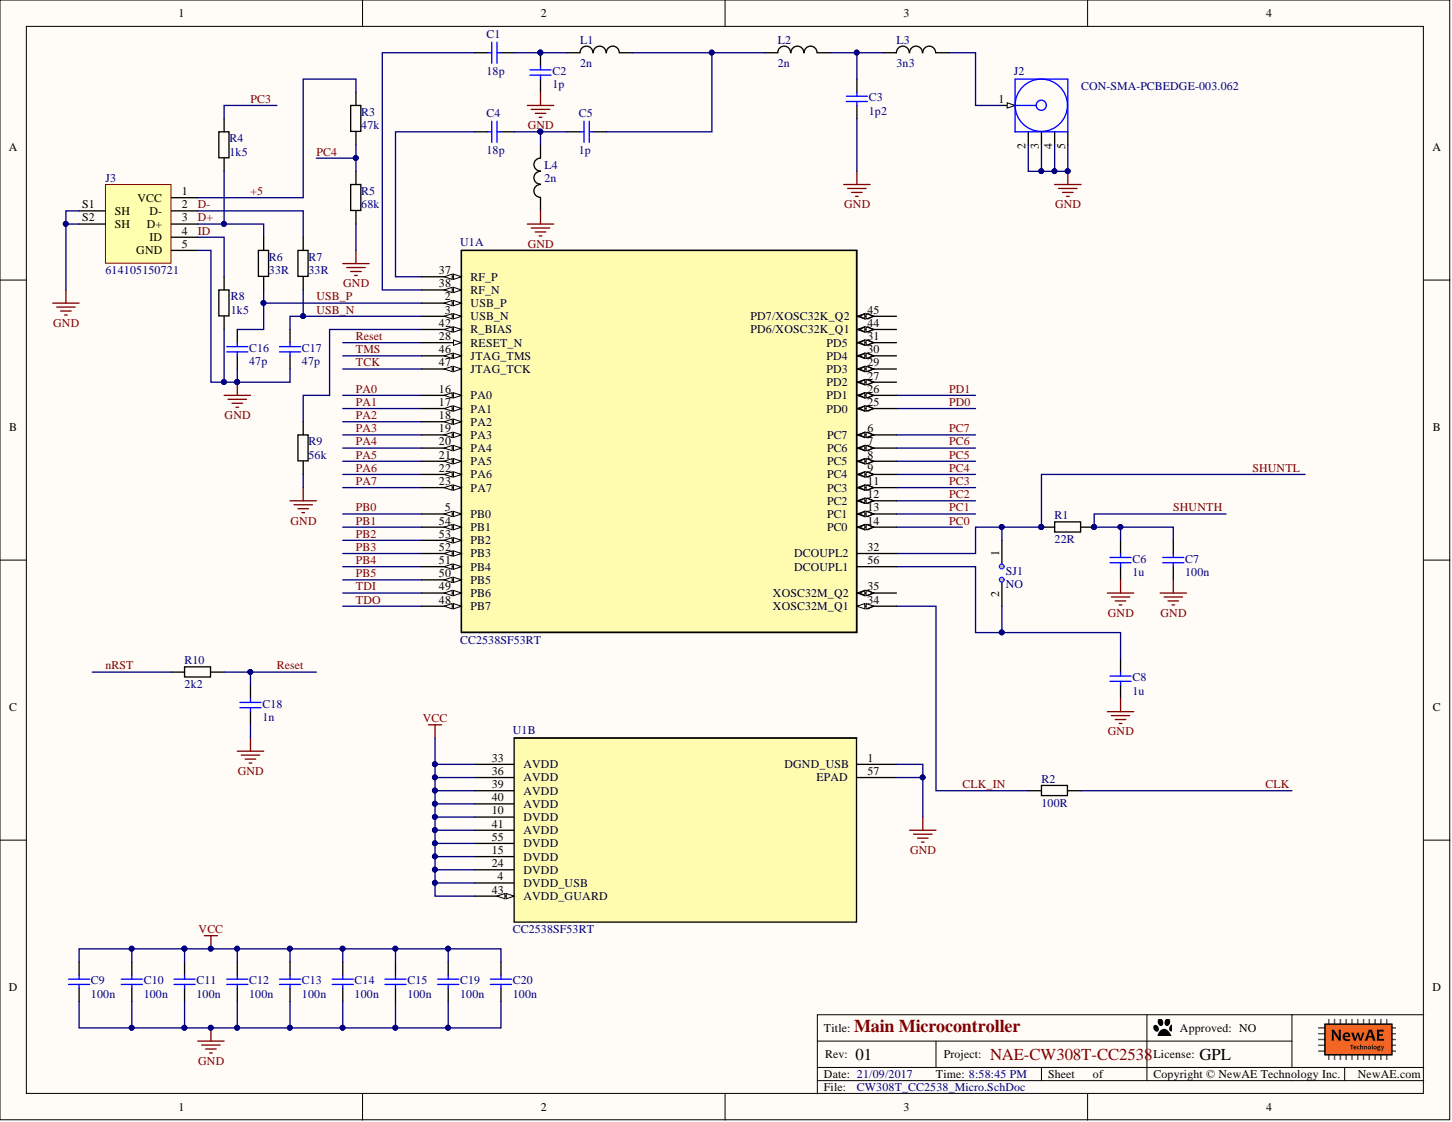
[picture p157: page 1]

USB_P | | USB_P 2
USB_N

Main Microcontroller Title: | Approved: NO

Rev: 01 | Project: NAE-CW308T-CC2538License: GPL

Date: 21/09/2017 Time: 8:58:45 PM | Sheet of

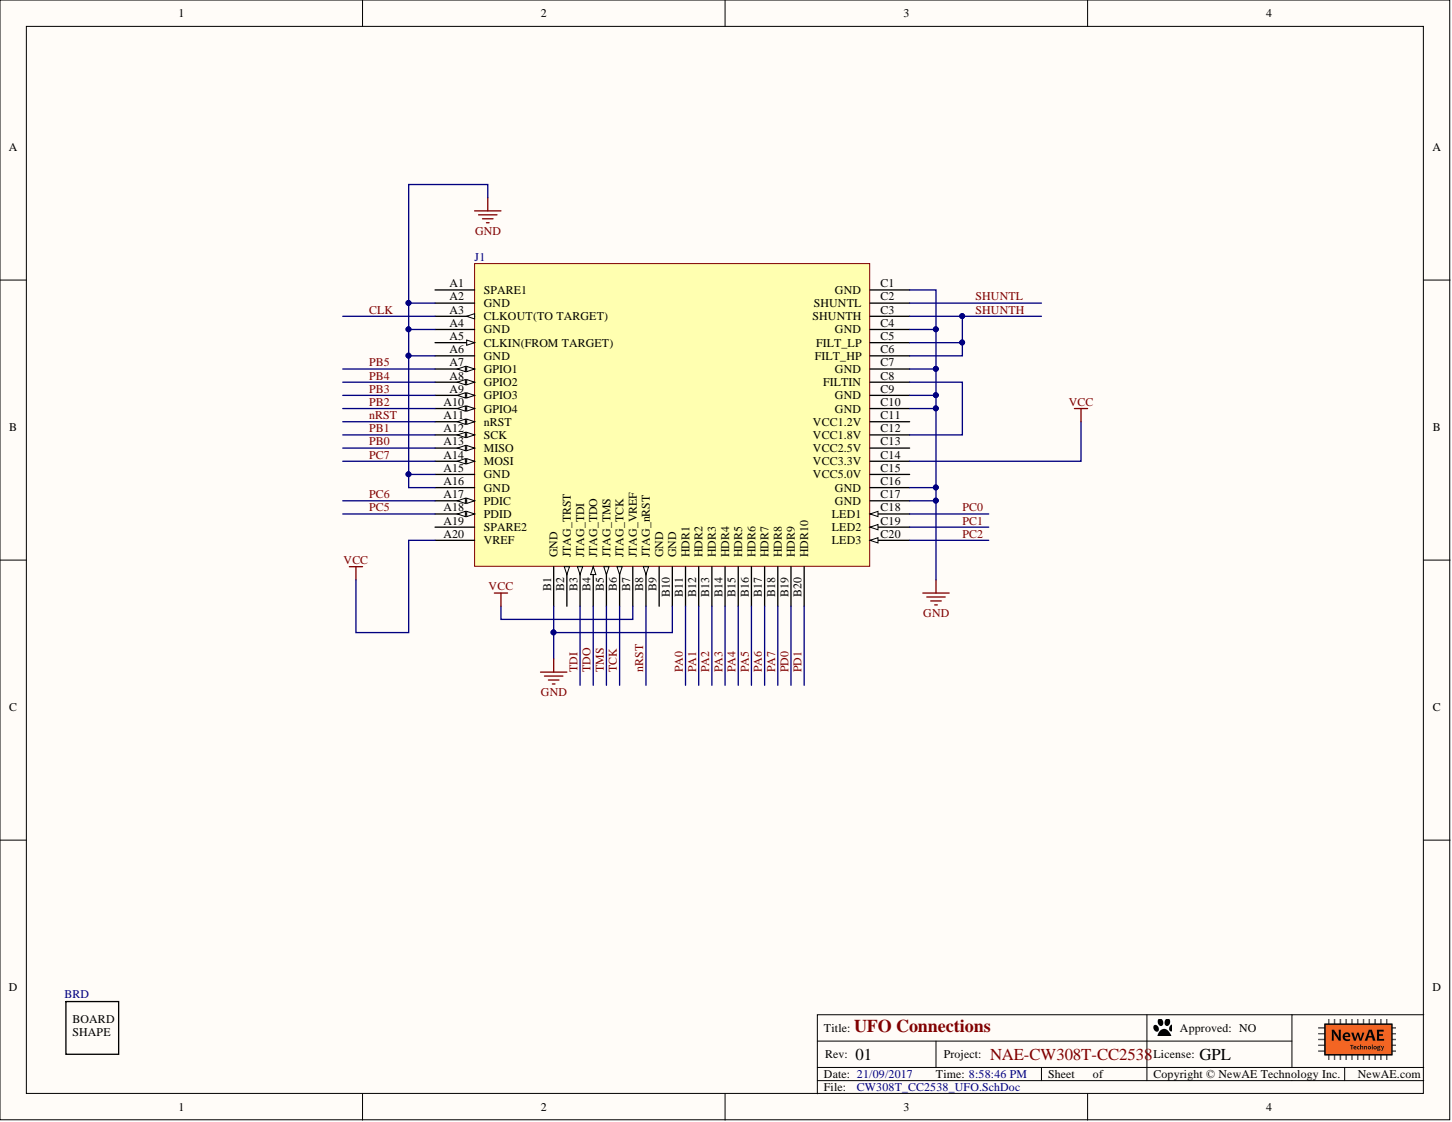
[picture p158: page 2]

UFO Connections Title: | Approved: NO

Rev: 01 | Project: NAE-CW308T-CC2538License: GPL

Date: 21/09/2017 Time: 8:58:46 PM | Sheet of
