newaetech/chipwhisperer-target-cw308t/CW308T_M2351S/NAE-CW308T-M2351_Schematic.PDF

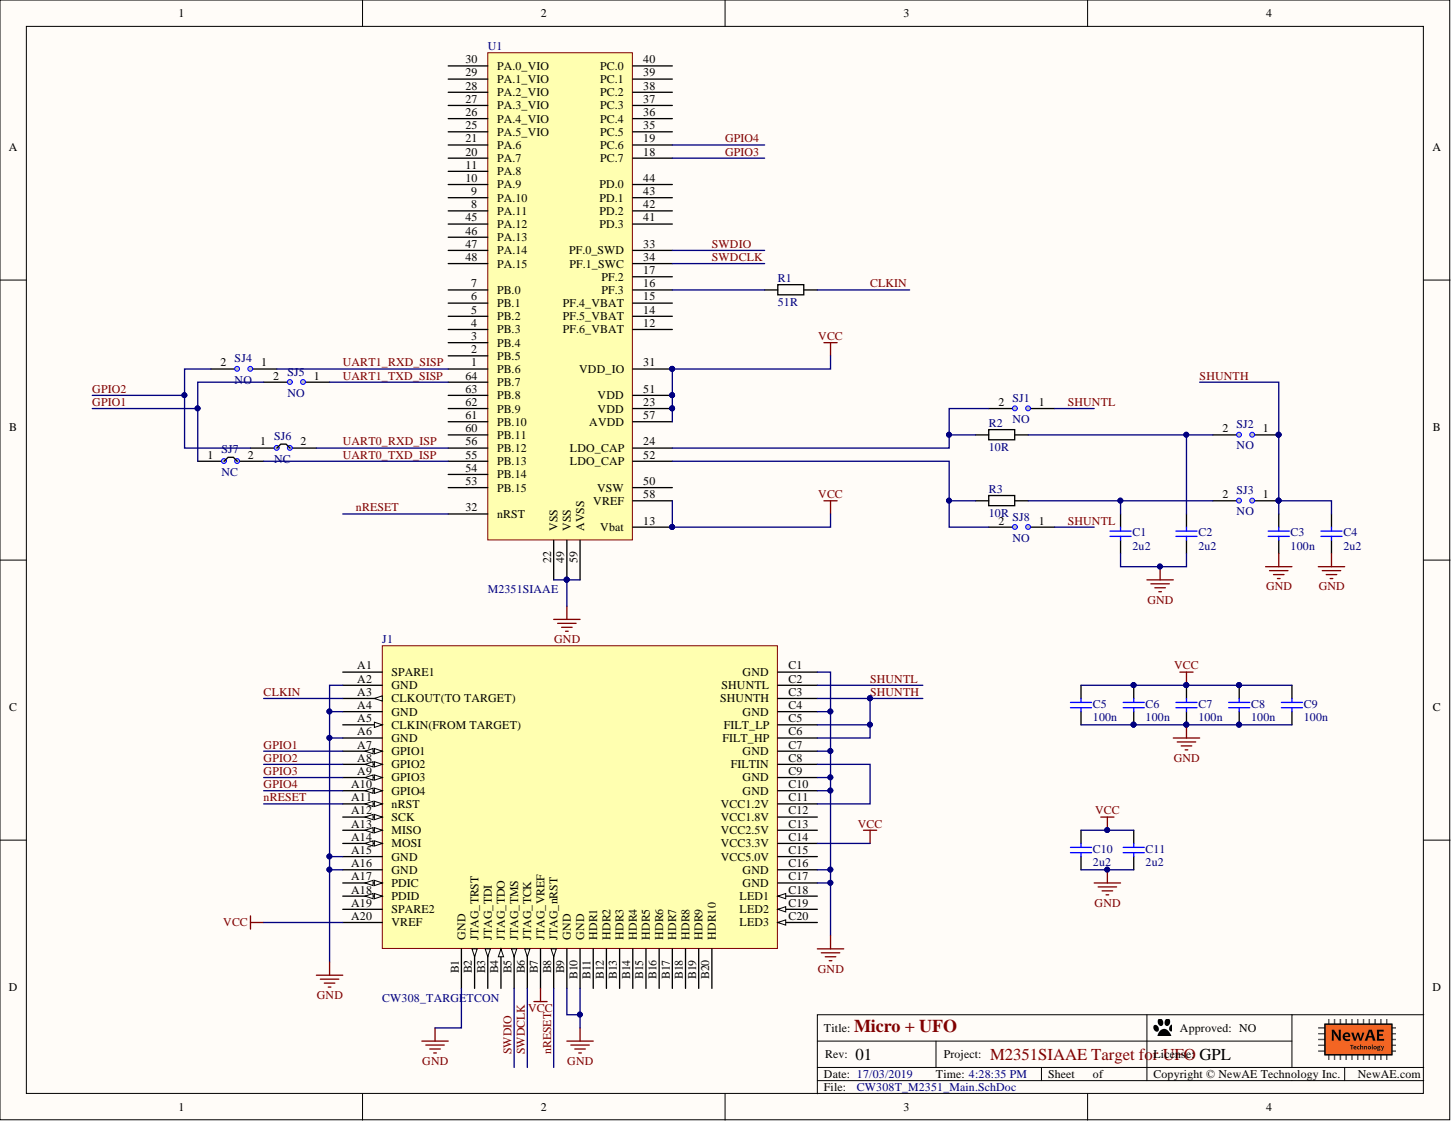
[picture p159: page 1]

Micro + UFO Title: | Approved: NO

Rev: 01 | Project: M2351SIAAE Target for Li | UcenFOse: GPL

Date: 17/03/2019 Time: 4:28:35 PM | Sheet of
