newaetech/chipwhisperer-target-cw308t/CW308T_XMEGA/CW308T_XMEGA_Schematic.PDF

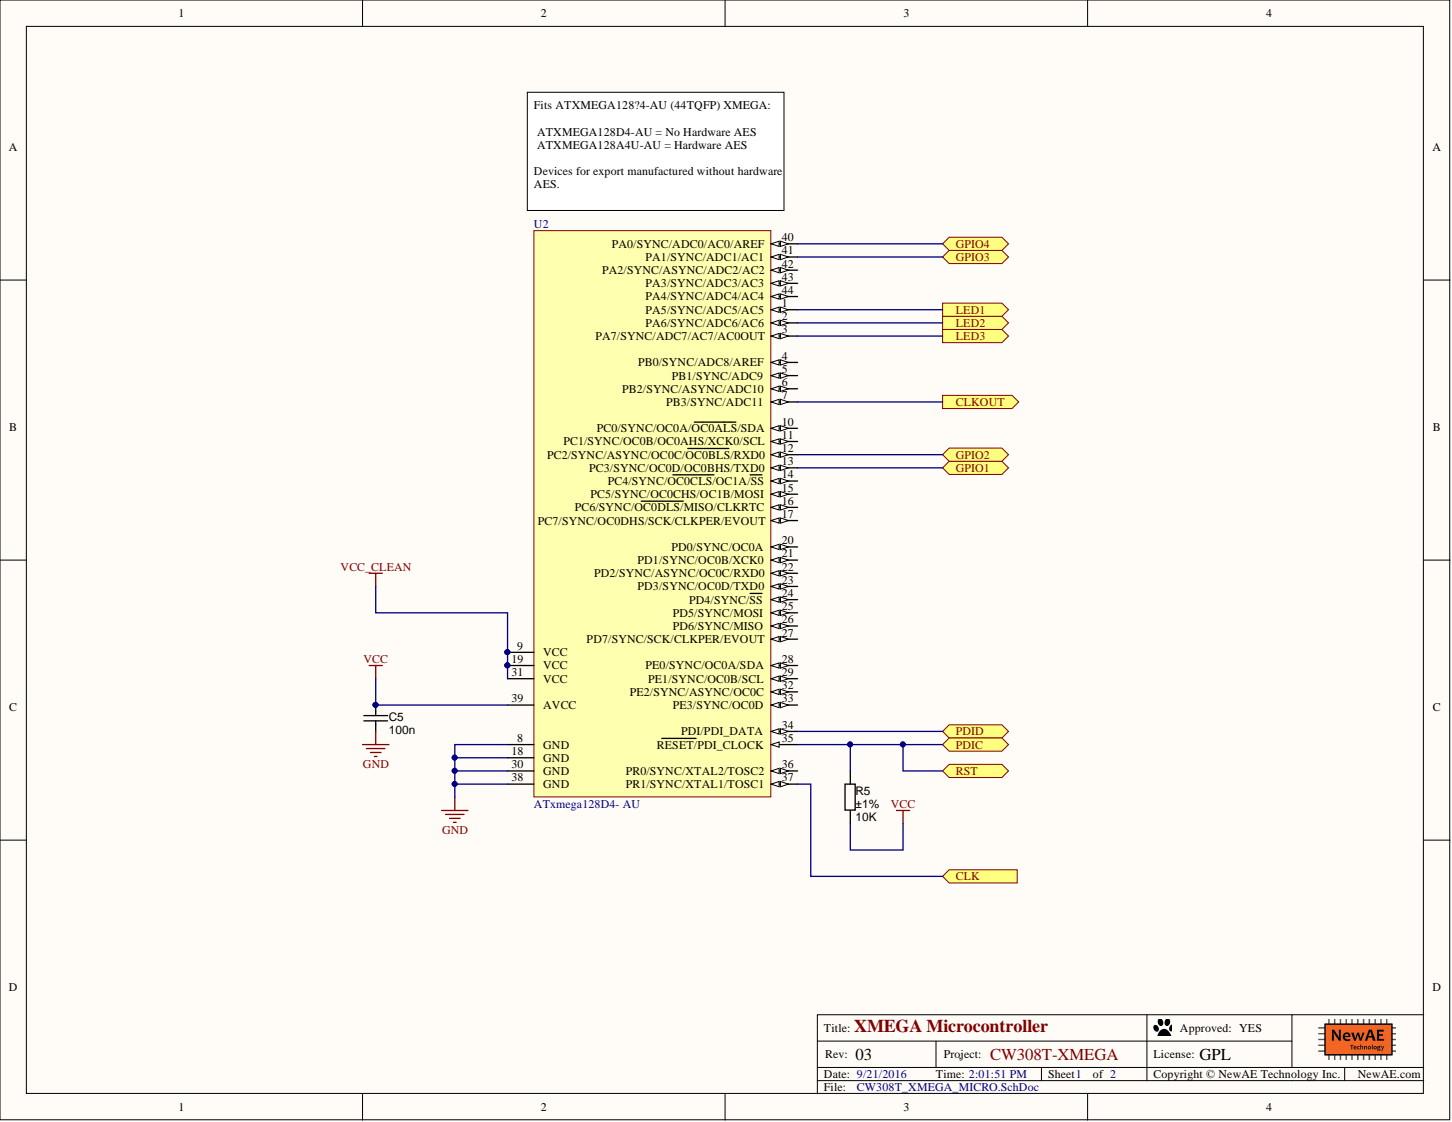
[picture p160: page 1]

X MEGA Microcontroller . T i t le: | A p pro ved : Y E S

Rev : 03 | Project : CW308T-XMEG A | L icen se: GPL

Date: 9 / 2 1 / 2 0 1 6 T ime: 2 : 0 1 : 5 1 PM | Sheet 1 o f 2 | Co p yri g h t © New A E Tech n | o l o g y Inc.

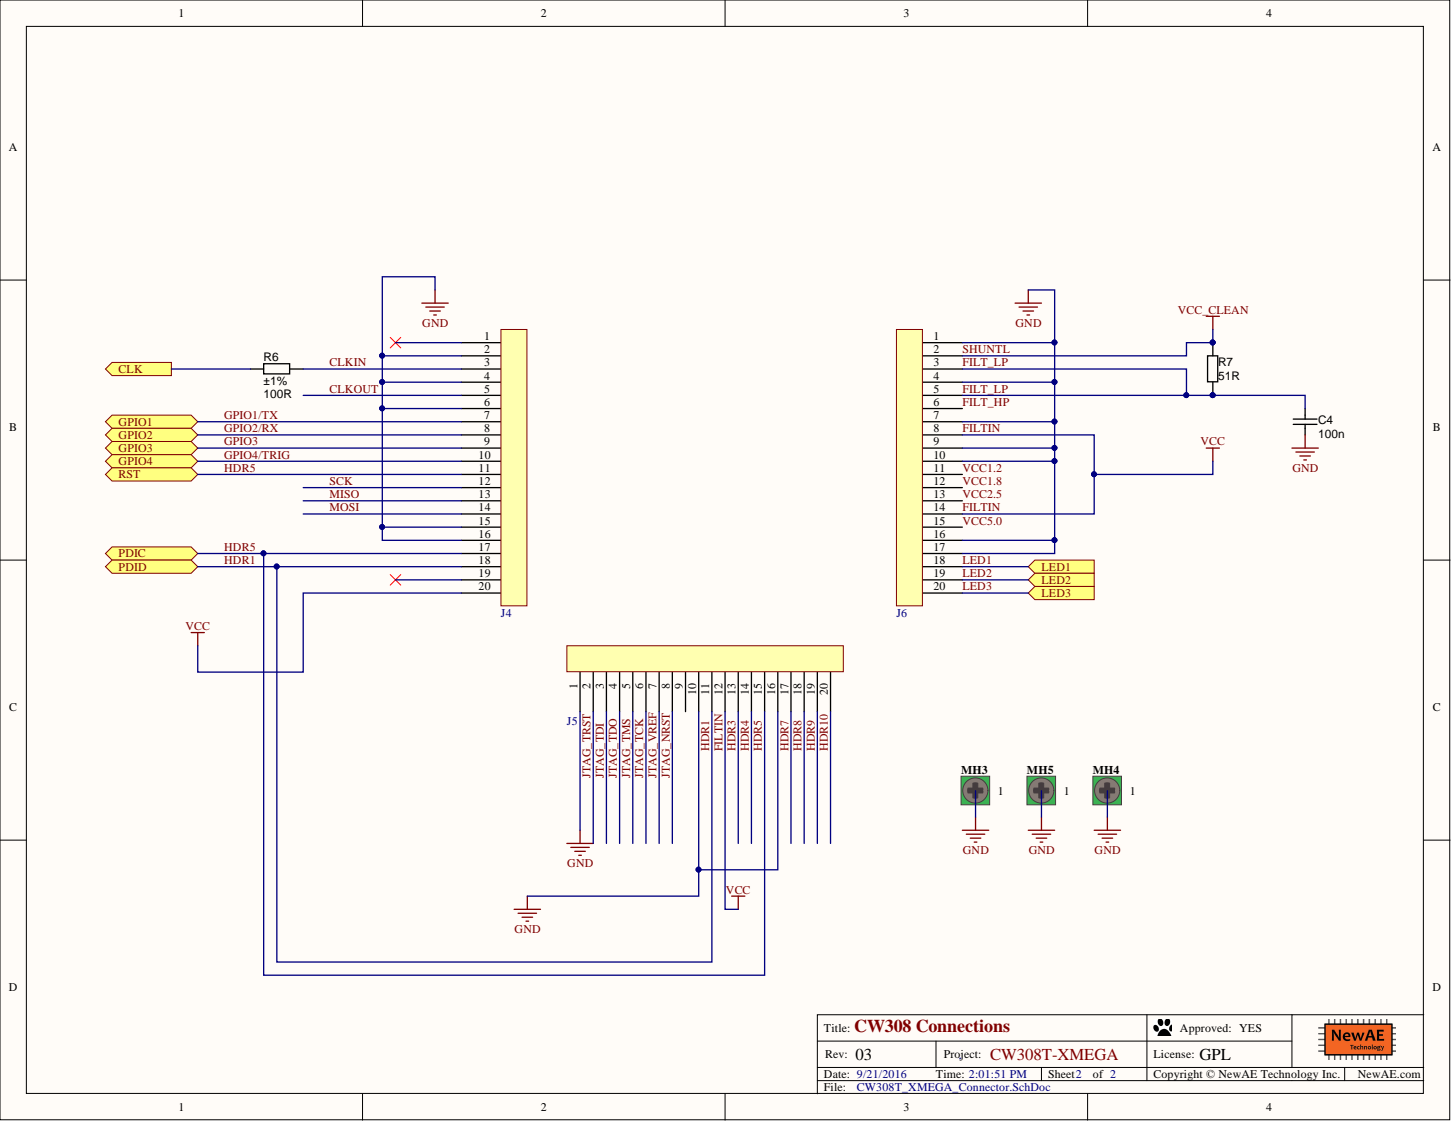
[picture p161: page 2]

SH U N T L
FIL T _ L P

FIL T _ H P

1 8
1 9 2 0

CW3 0 8 C onnections . T i t le: | A p pro ved : Y E S

Rev : 03 | Project : CW308T-XMEG A | L icen se: GPL

Date: 9 / 2 1 / 2 0 1 6 T ime: 2 : 0 1 : 5 1 PM | Sheet 2 o f 2 | Co p yri g h t © New A E Tech n | o l o g y Inc.
