newaetech/chipwhisperer-target-cw308t/CW312T_XC7A35T/NAE-CW312T0XC7A35-04.PDF

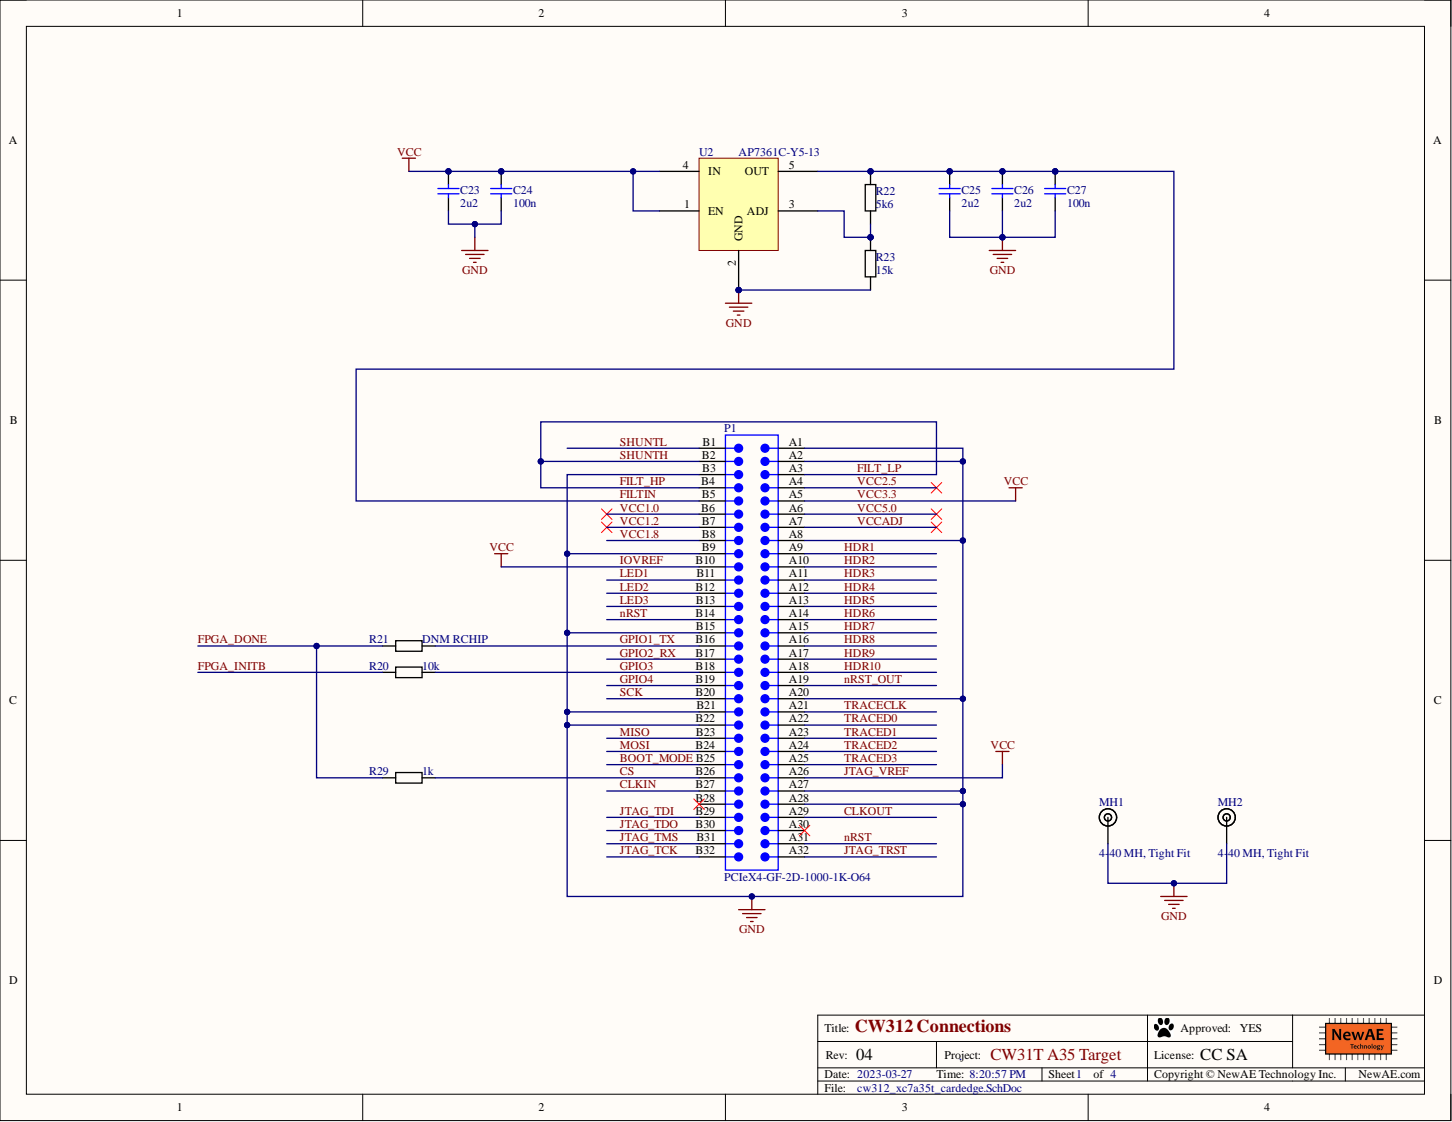
[picture p162: page 1]

FILT _ H P | B4

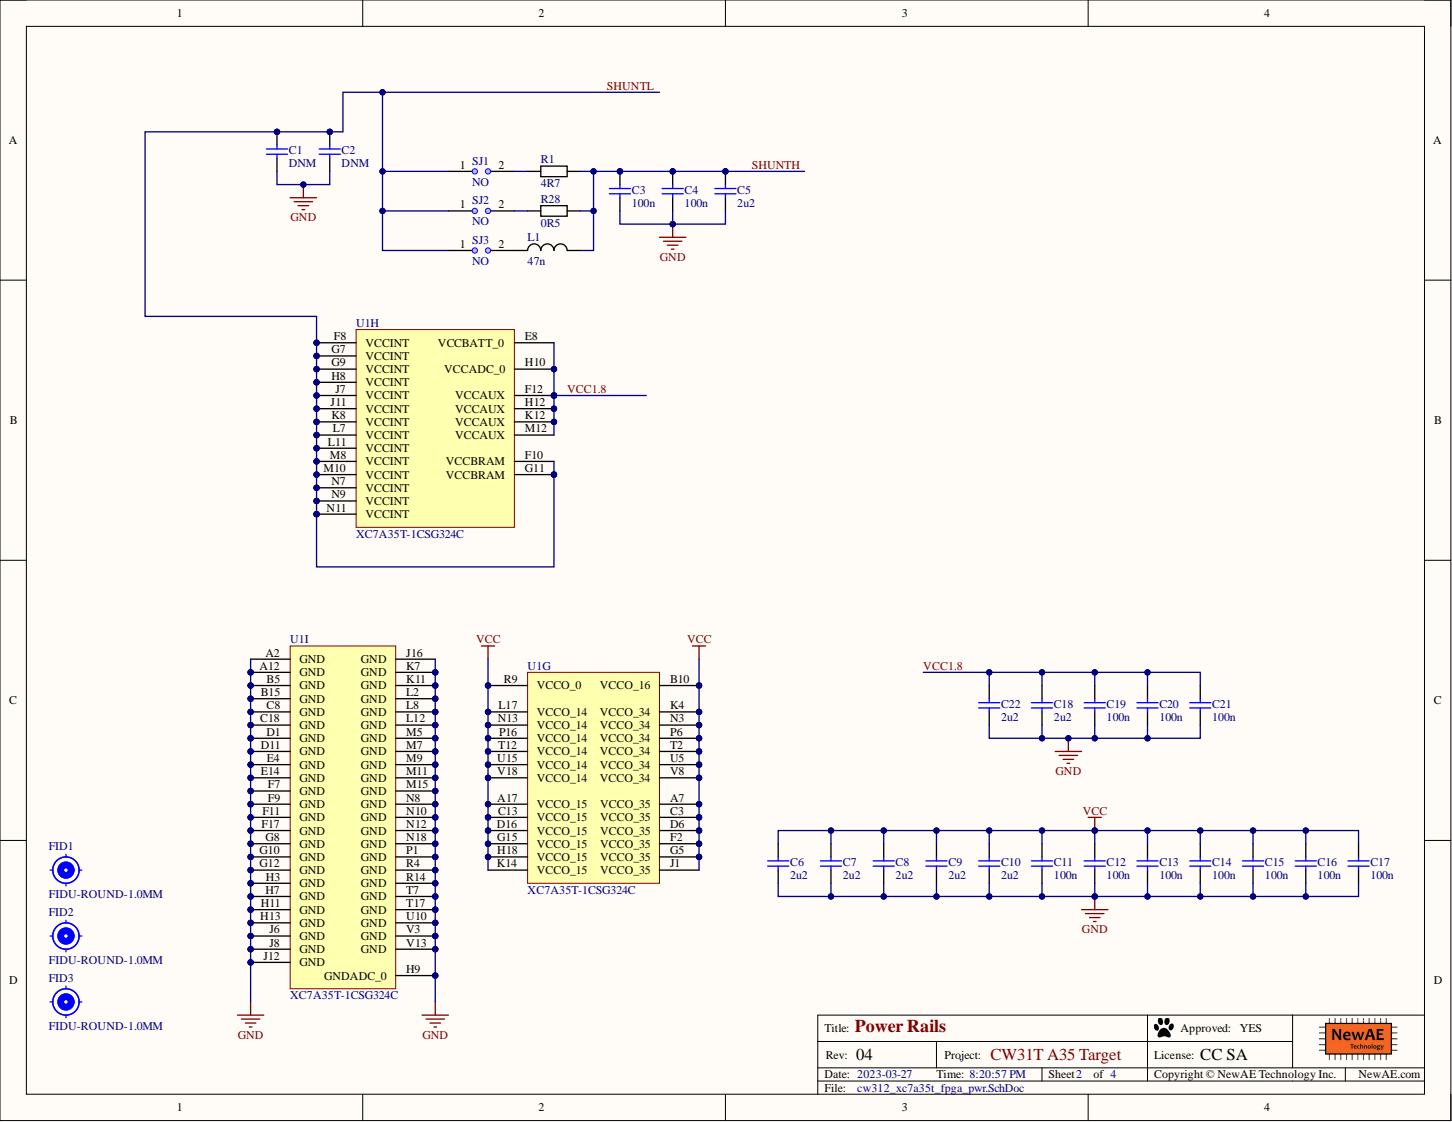
[picture p163: page 2]

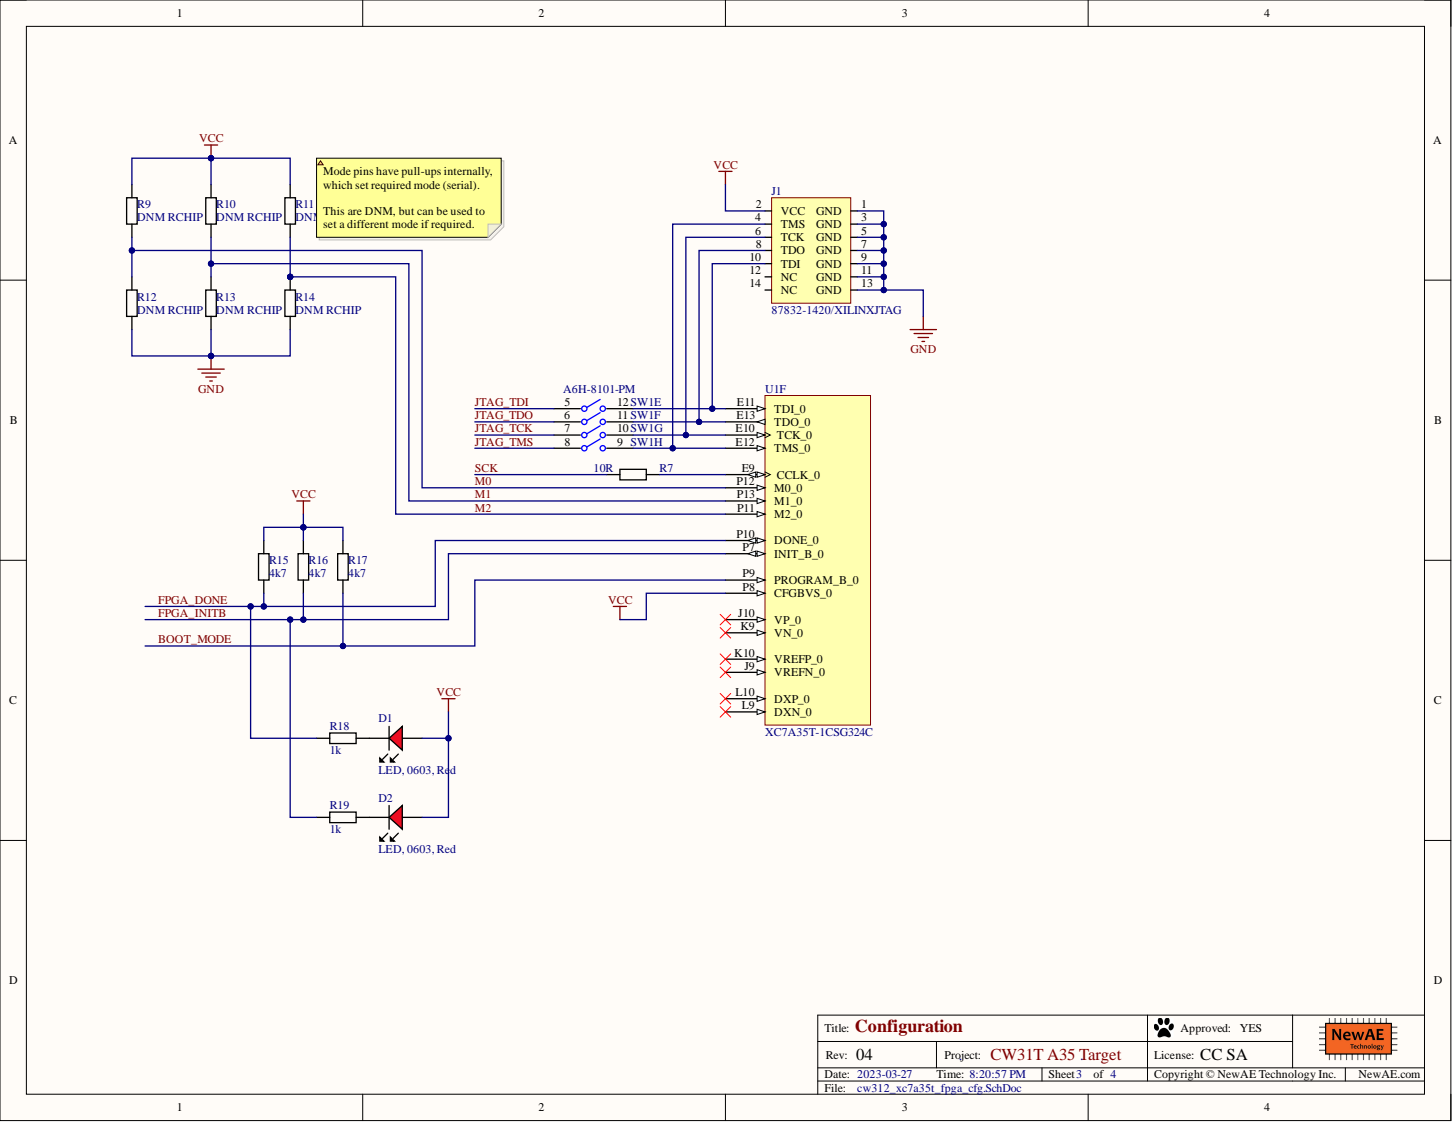
[picture p164: page 3]

Mode pins have pull-ups internally,
which set required mode (serial).
This are DNM, but can be used to
DNM RCHIP
set a different mode if required.

VCC M1 | | M1_0 P13

DONE_0 P10
INIT_B_0 P7

FPGA_DONE | | CFGBVS_0 P8 PROGRAM_B_0 P9

FPGA_INITB
BOOT_MODE | | VN_0 K9

VCC

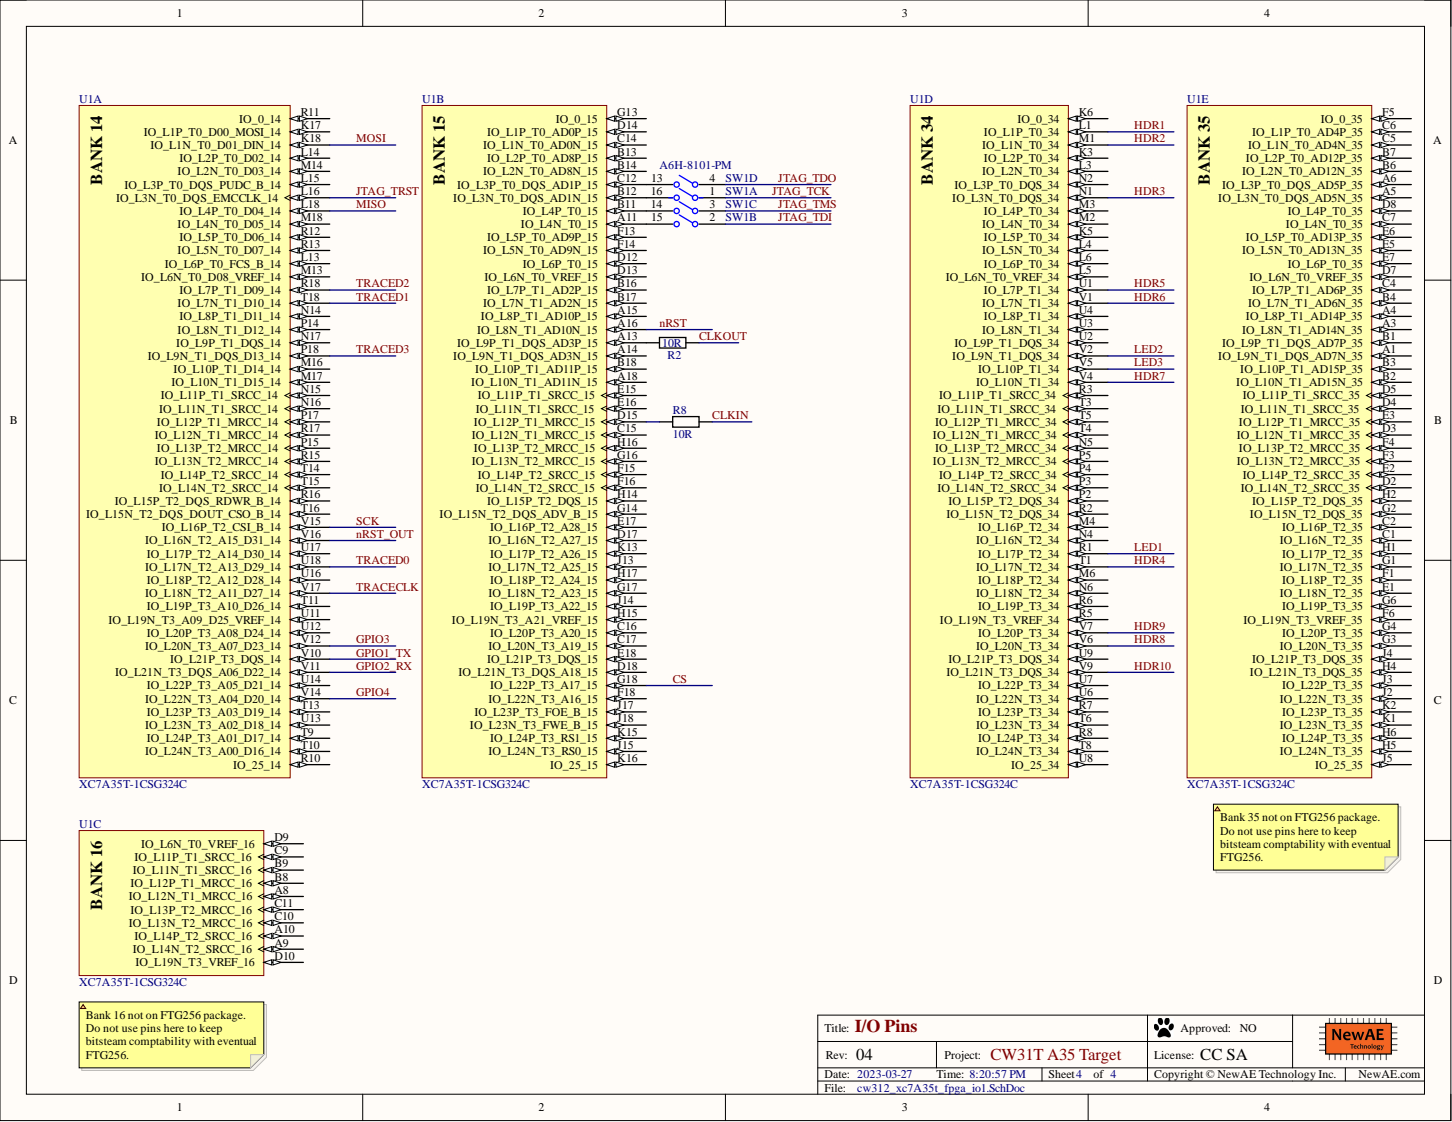
[picture p165: page 4]
