newaetech/chipwhisperer-target-cw308t/CW312T_TMP91FW/NAE-CW312T-TMP91FW rev 0.pdf

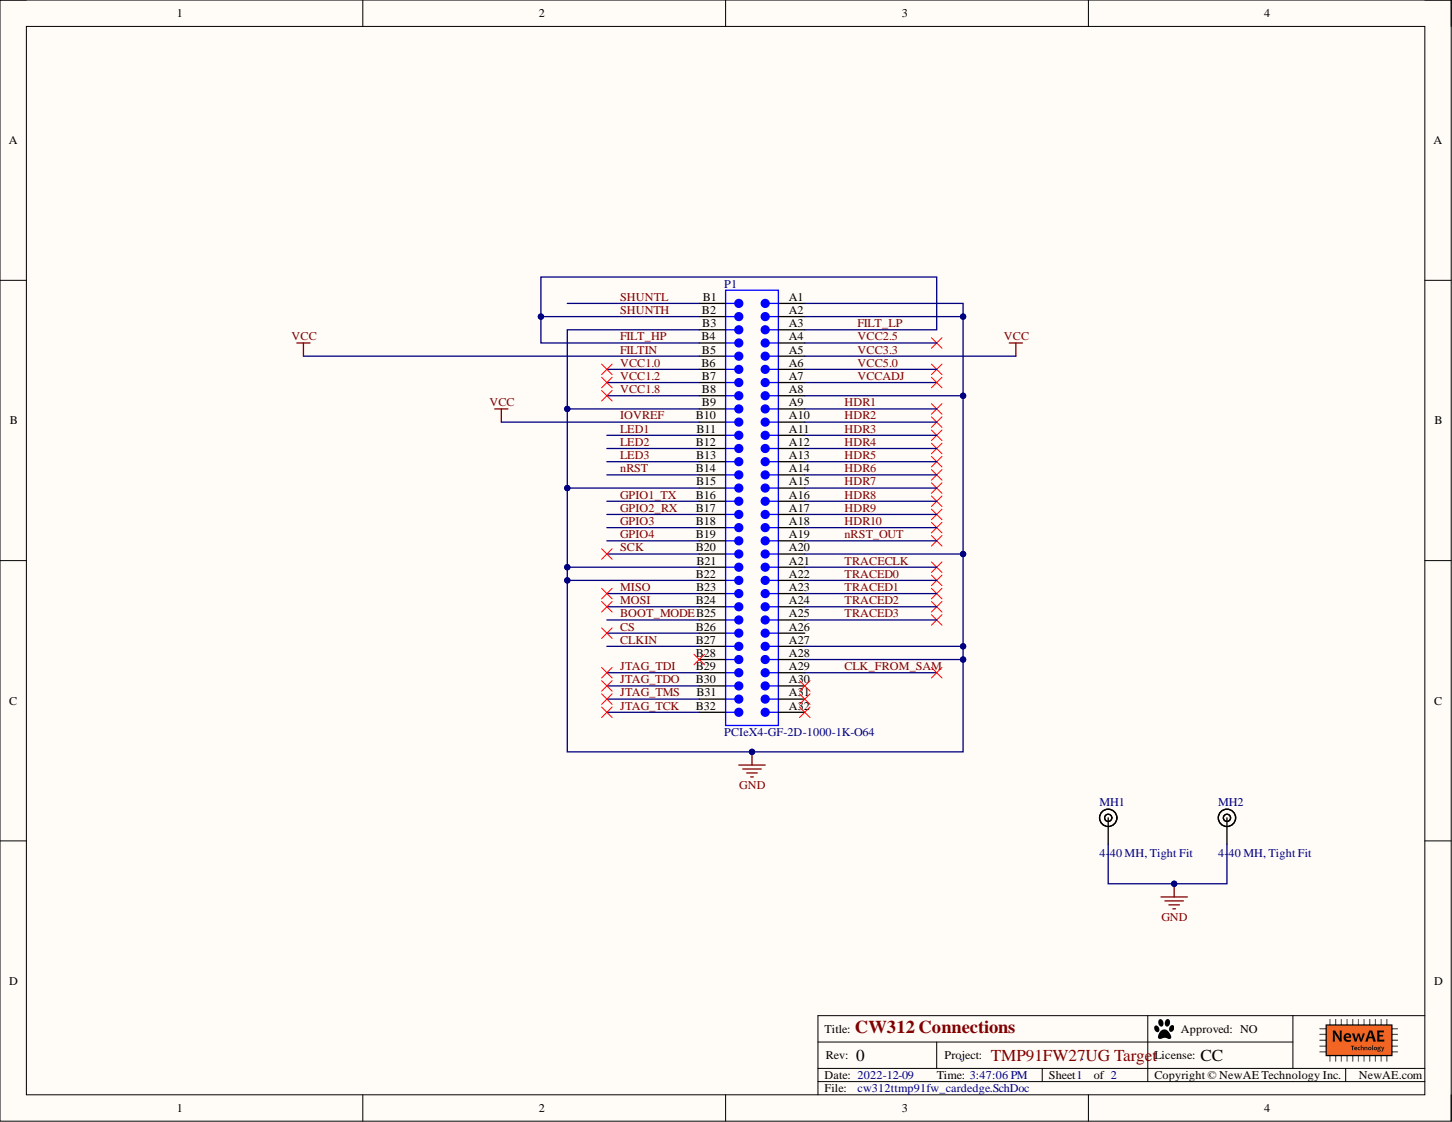
[picture p174: page 1]

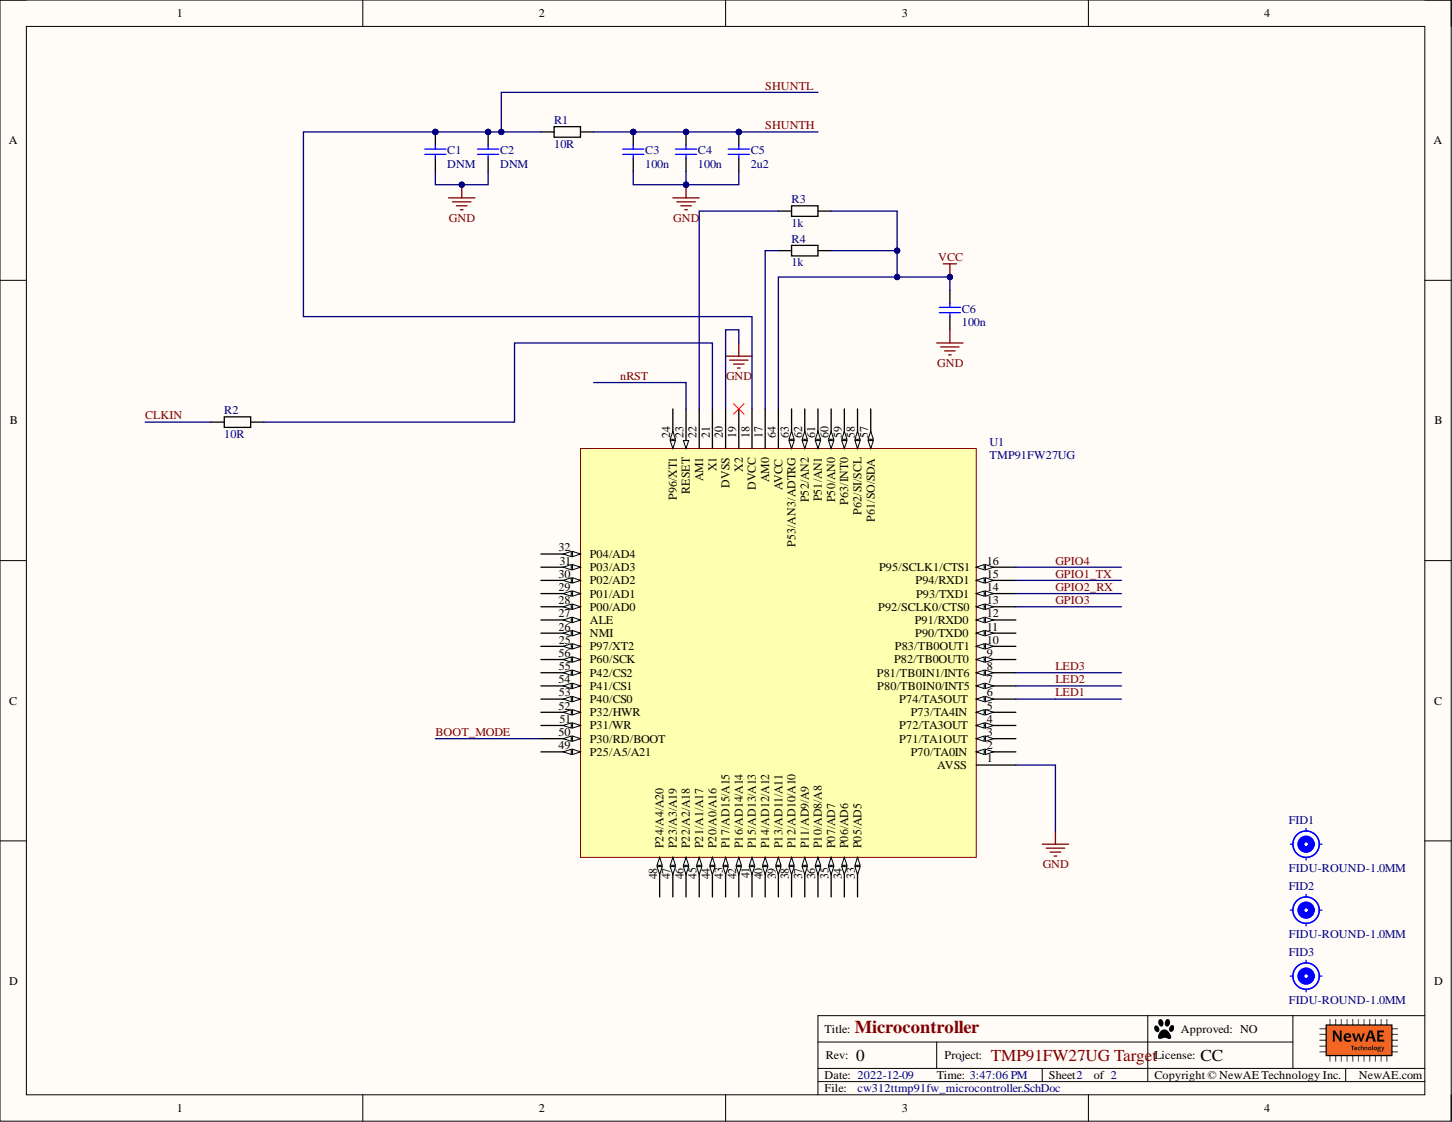
[picture p175: page 2]

P61/SO/SDA 57 P62/SI/SCL 58 P63/INT0 59 P50/AN0 60 P51/AN1 61 P52/AN2 62 P53/AN3/ADTRG 63 AVCC 64 AM0 17 DVCC 18 X2 19 DVSS 20 X1 21 AM1 22 RESET 23 P96/XT1 24
