newaetech/chipwhisperer-target-cw308t/CW312T_ATSAM4S/NAE-CW312T-SAM4S-02.PDF

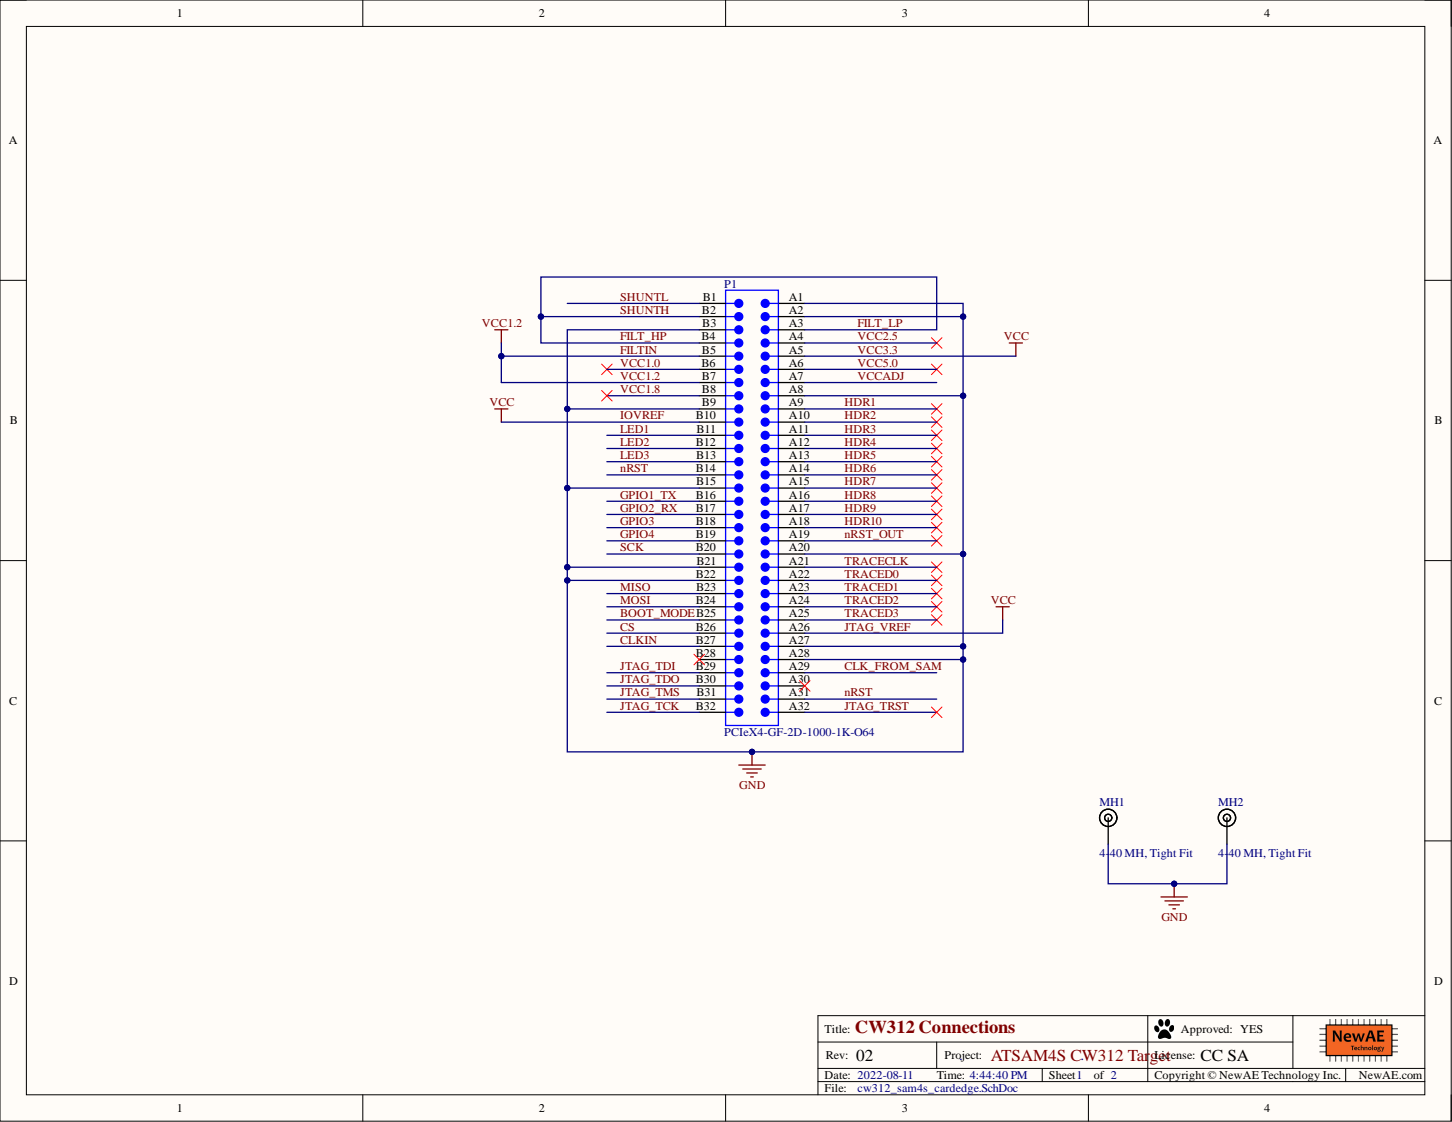
[picture p176: page 1]

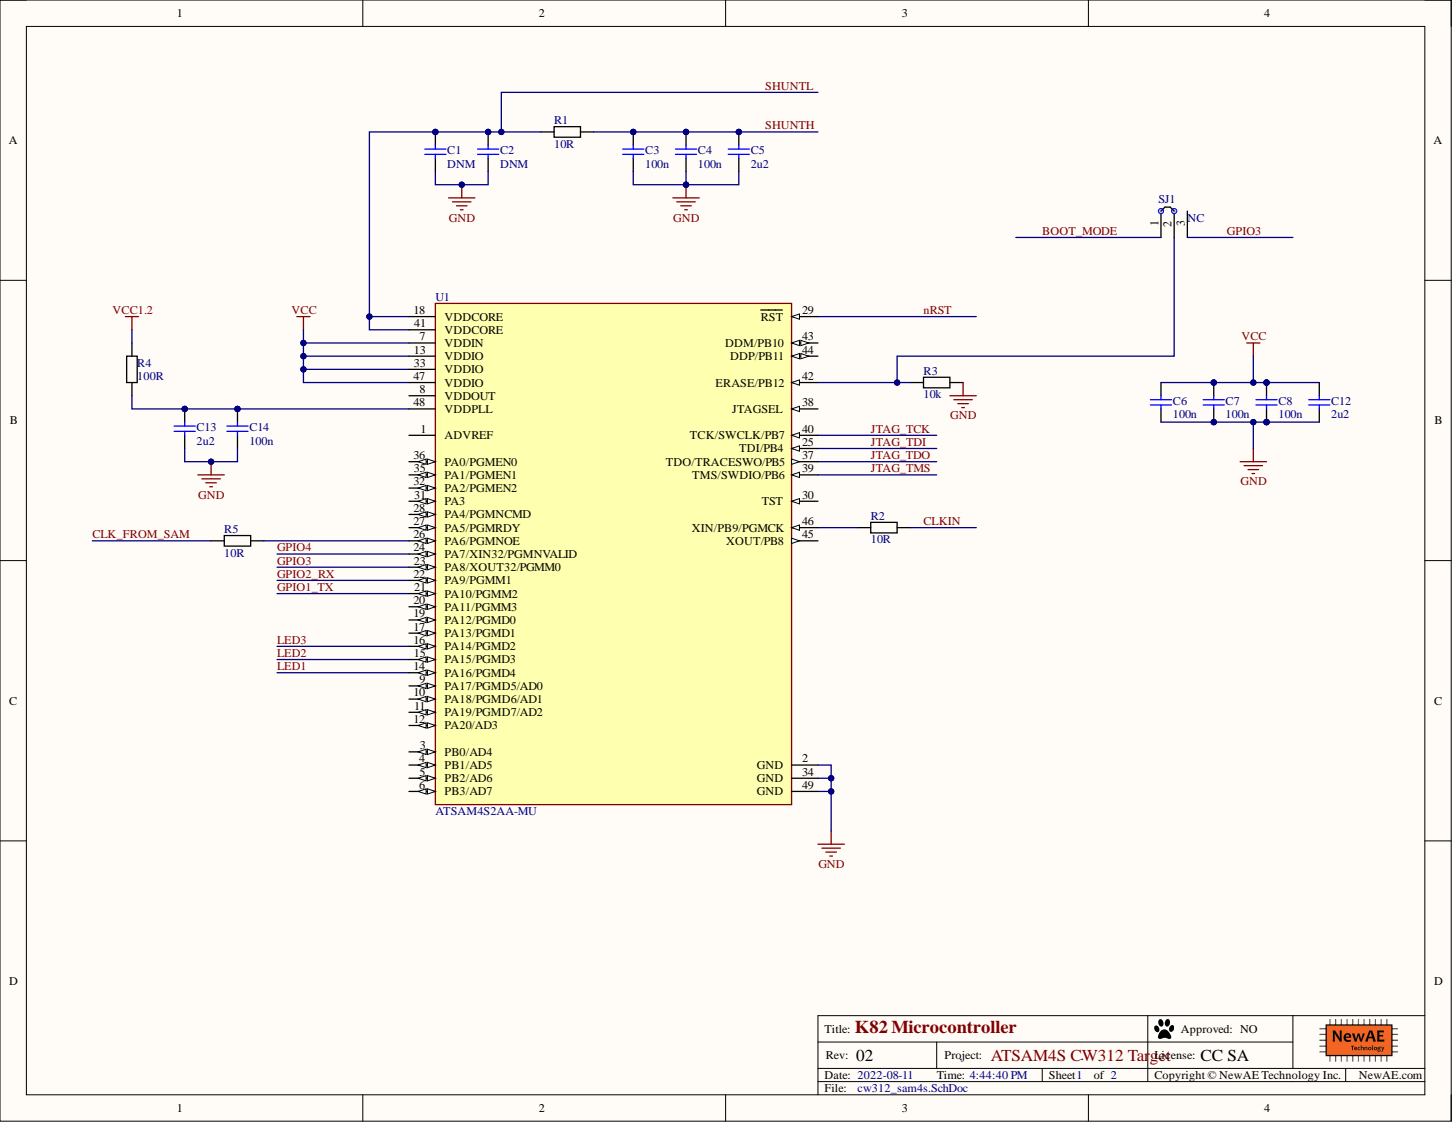
[picture p177: page 2]

1 3 | 4 4
3 3 | 4 2

3 4
4 9
