newaetech/chipwhisperer-target-cw308t/CW312T_ICE40UP/NAE-CW312T-iCE40.PDF

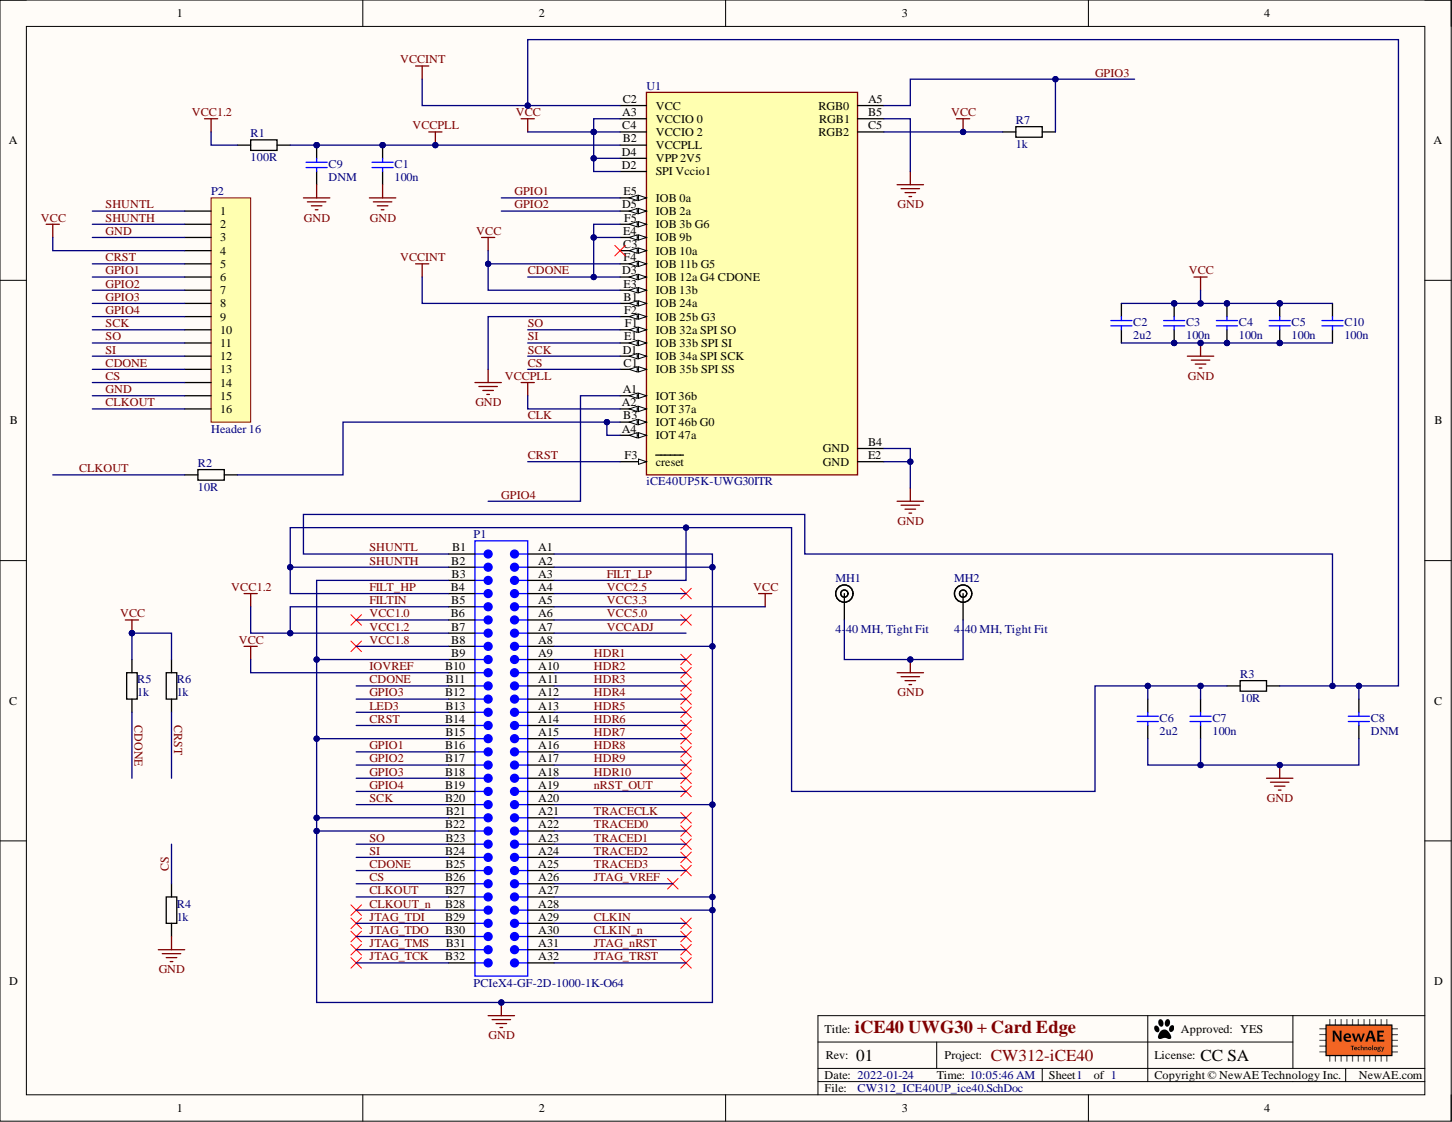
[picture p178: page 1]

D 4
D 2

FILT _ H P | B4
