newaetech/chipwhisperer-target-cw308t/CW308T_MPC5Y/NAE-CW308T-MPC5Y.PDF

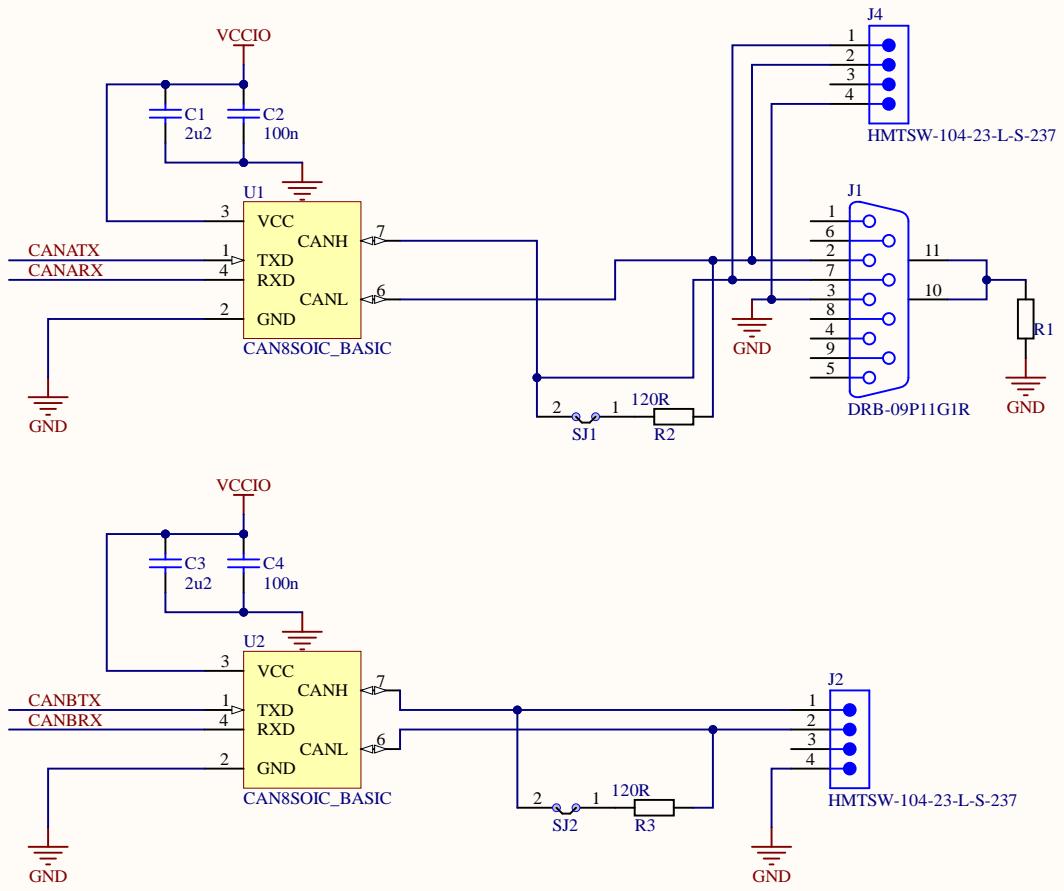
[picture p179: page 1]

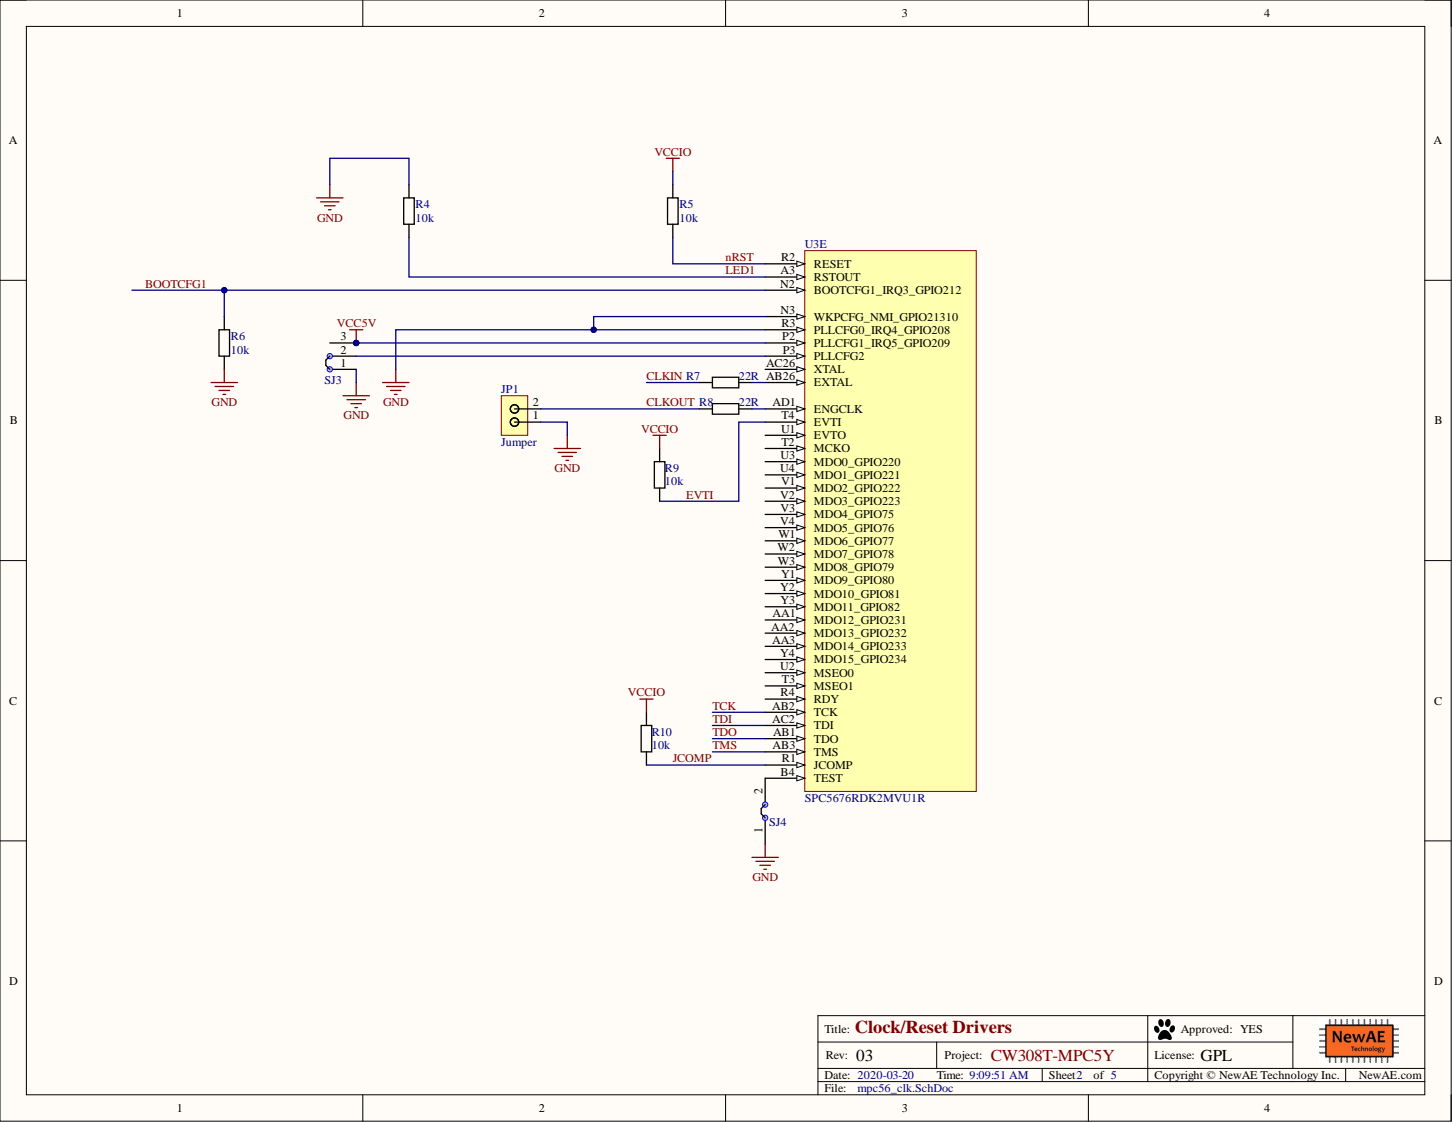
[picture p180: page 2]

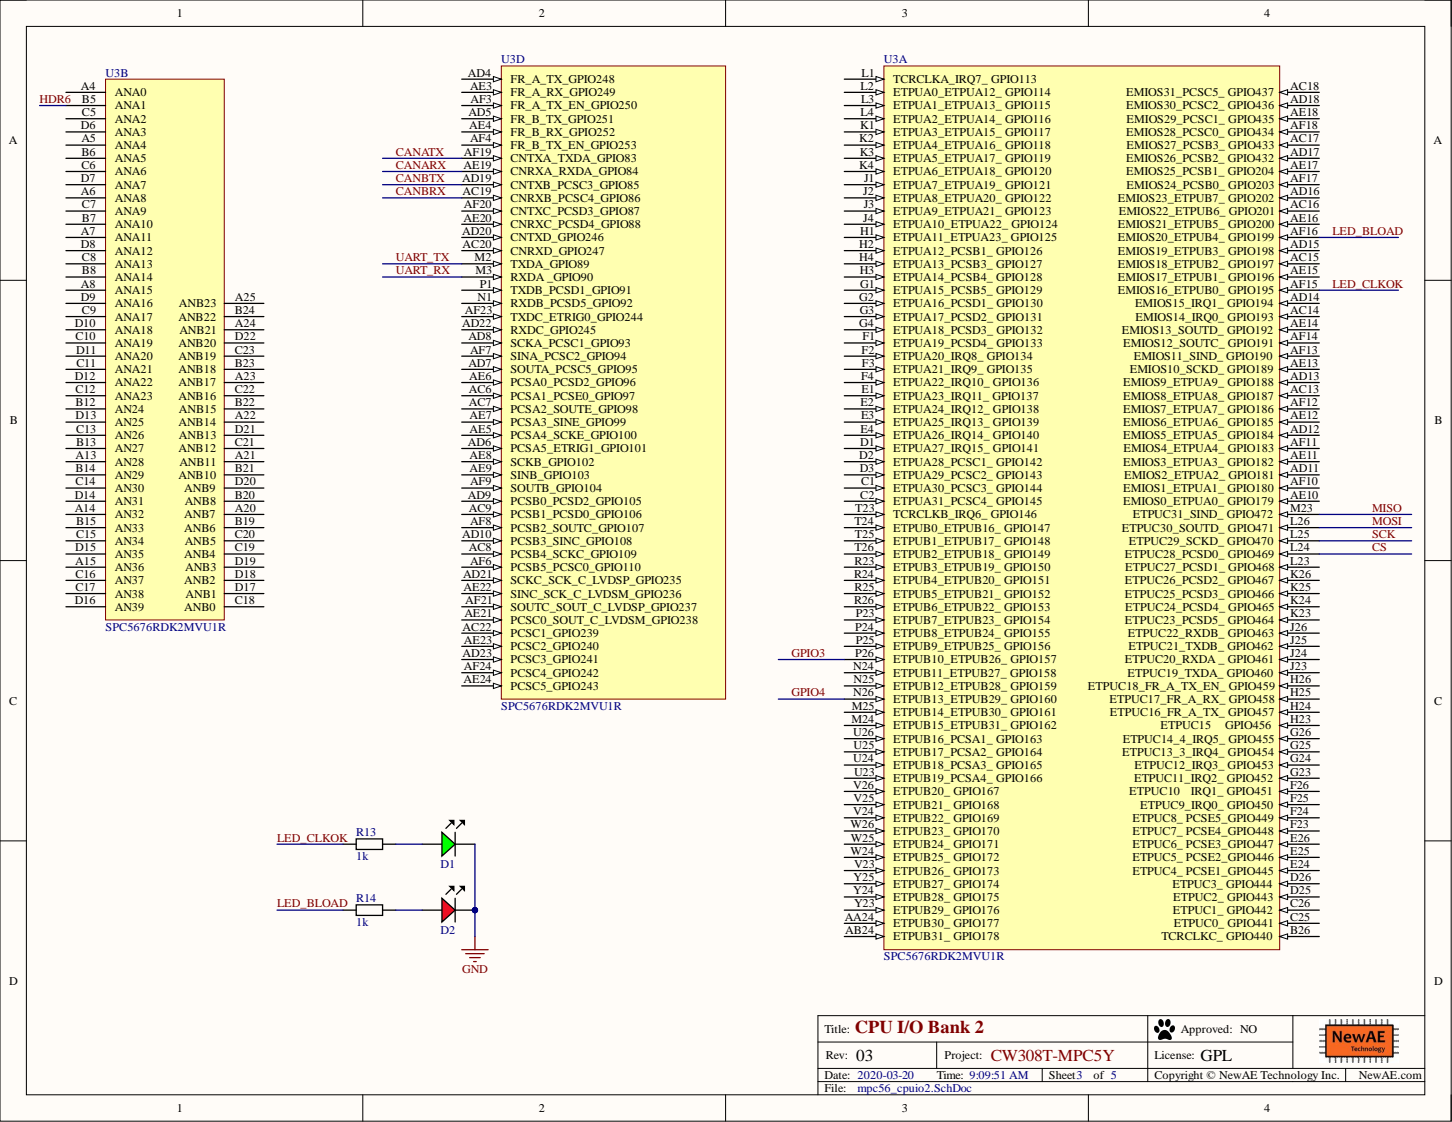
[picture p181: page 3]

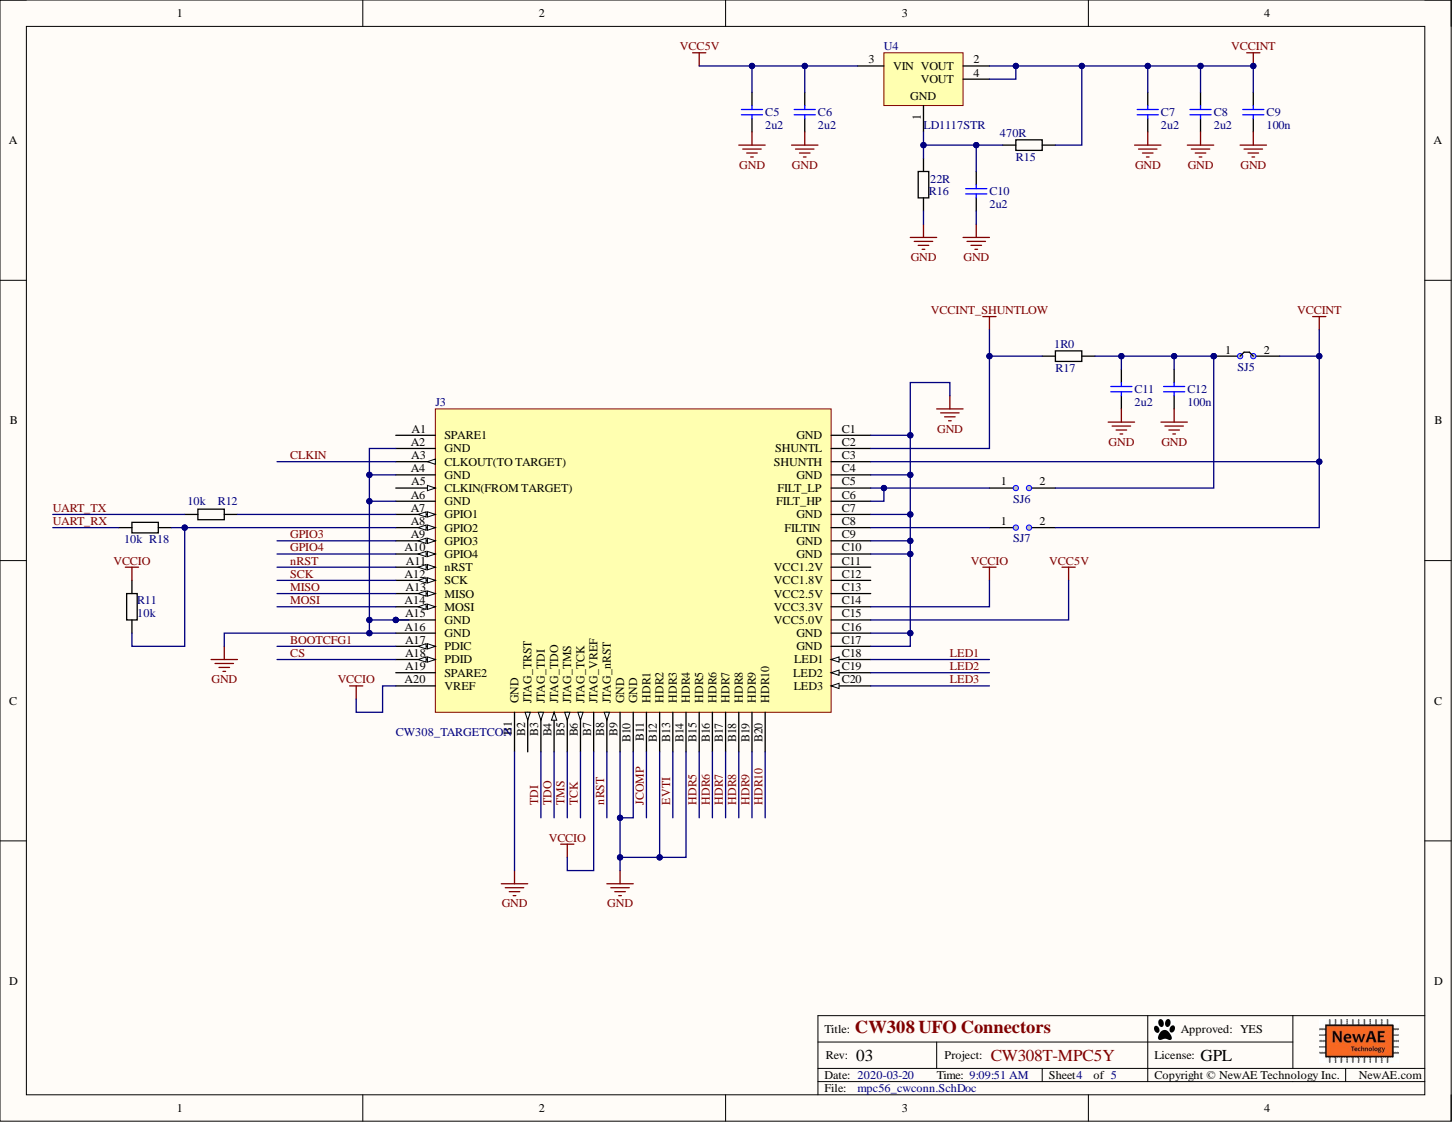
[picture p182: page 4]

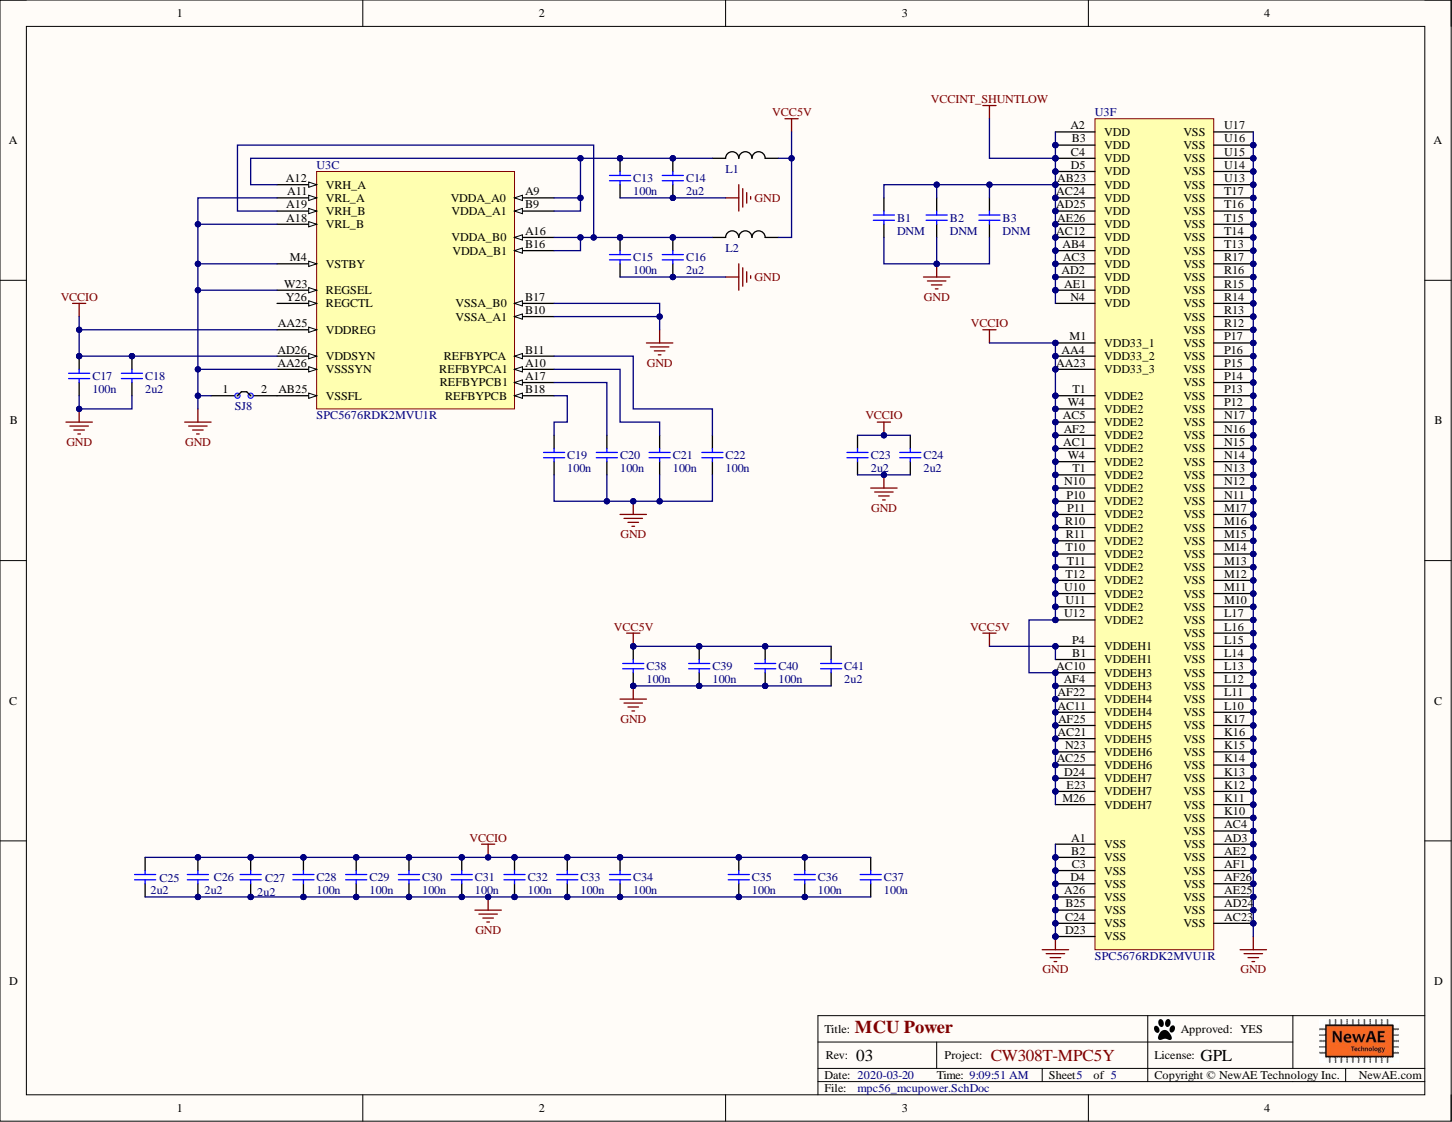
[picture p183: page 5]
