newaetech/chipwhisperer-target-cw308t/CW308T_IMXRT1062/NAE-CW308T-IMXRT1062_02.PDF

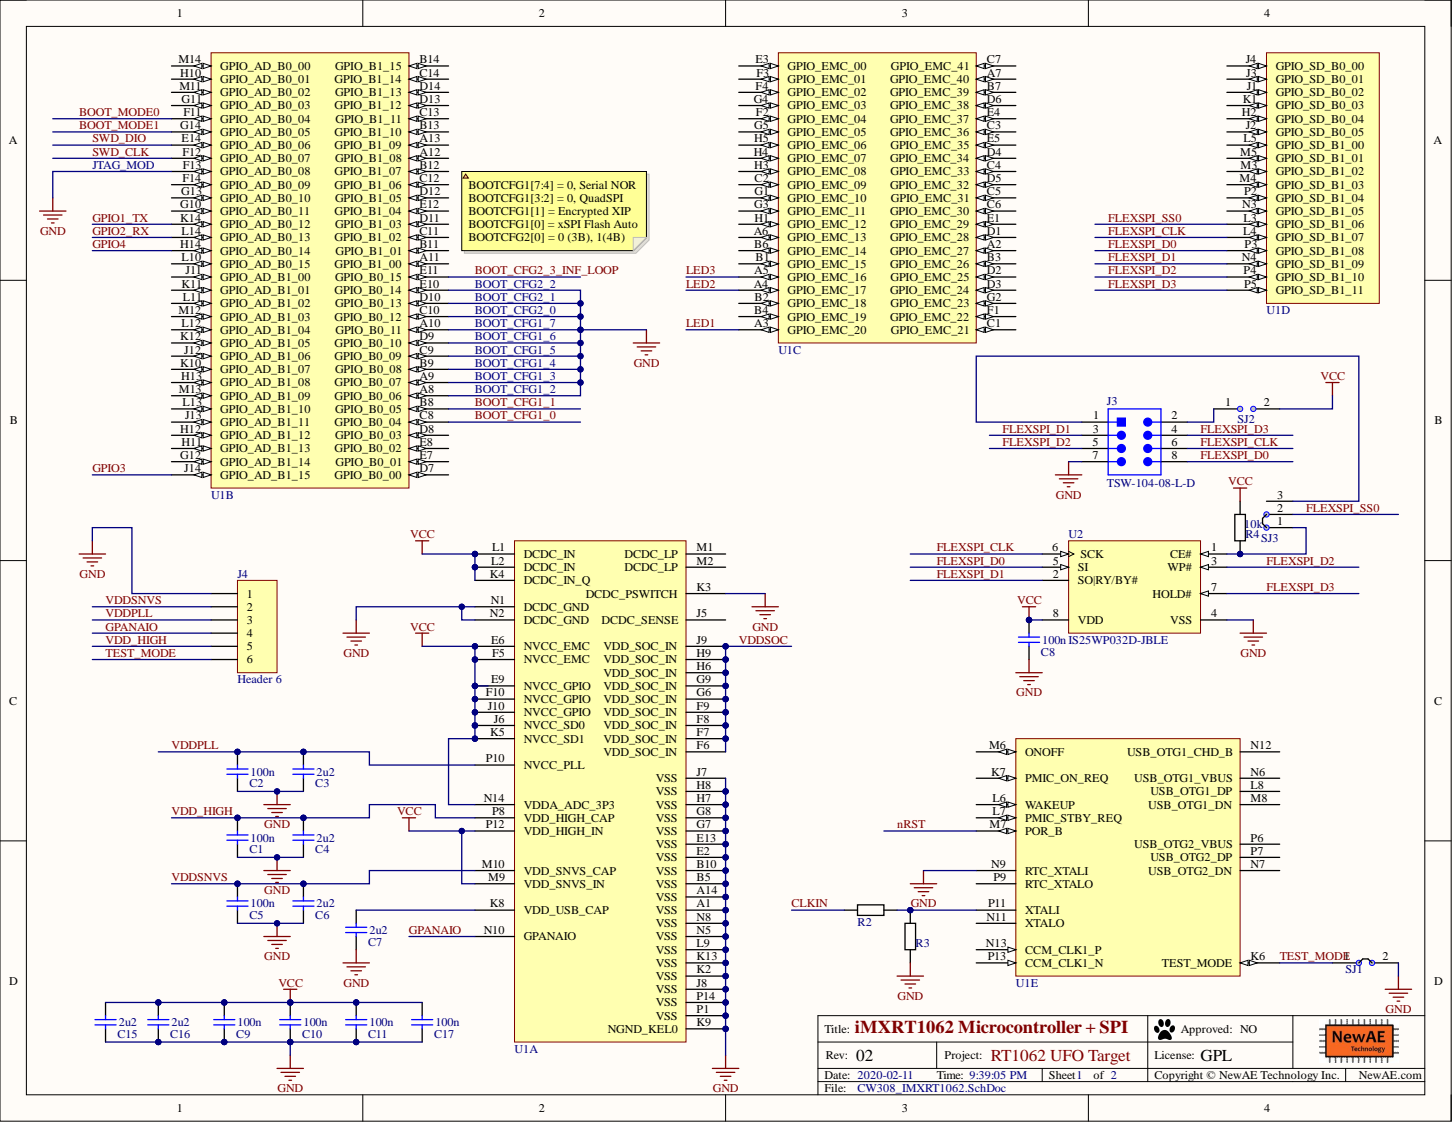
[picture p184: page 1]

GPIO_AD_B1_03 M12 | BOOT_CFG2_0
GPIO_AD_B1_04 L12 | BOOT_CFG1_7
GPIO_AD_B1_05 K12 | BOOT_CFG1_6
GPIO_AD_B1_06 J12 | BOOT_CFG1_5

GPIO_AD_B1_08 H13 | BOOT_CFG1_3
GPIO_AD_B1_09 M13 | BOOT_CFG1_2

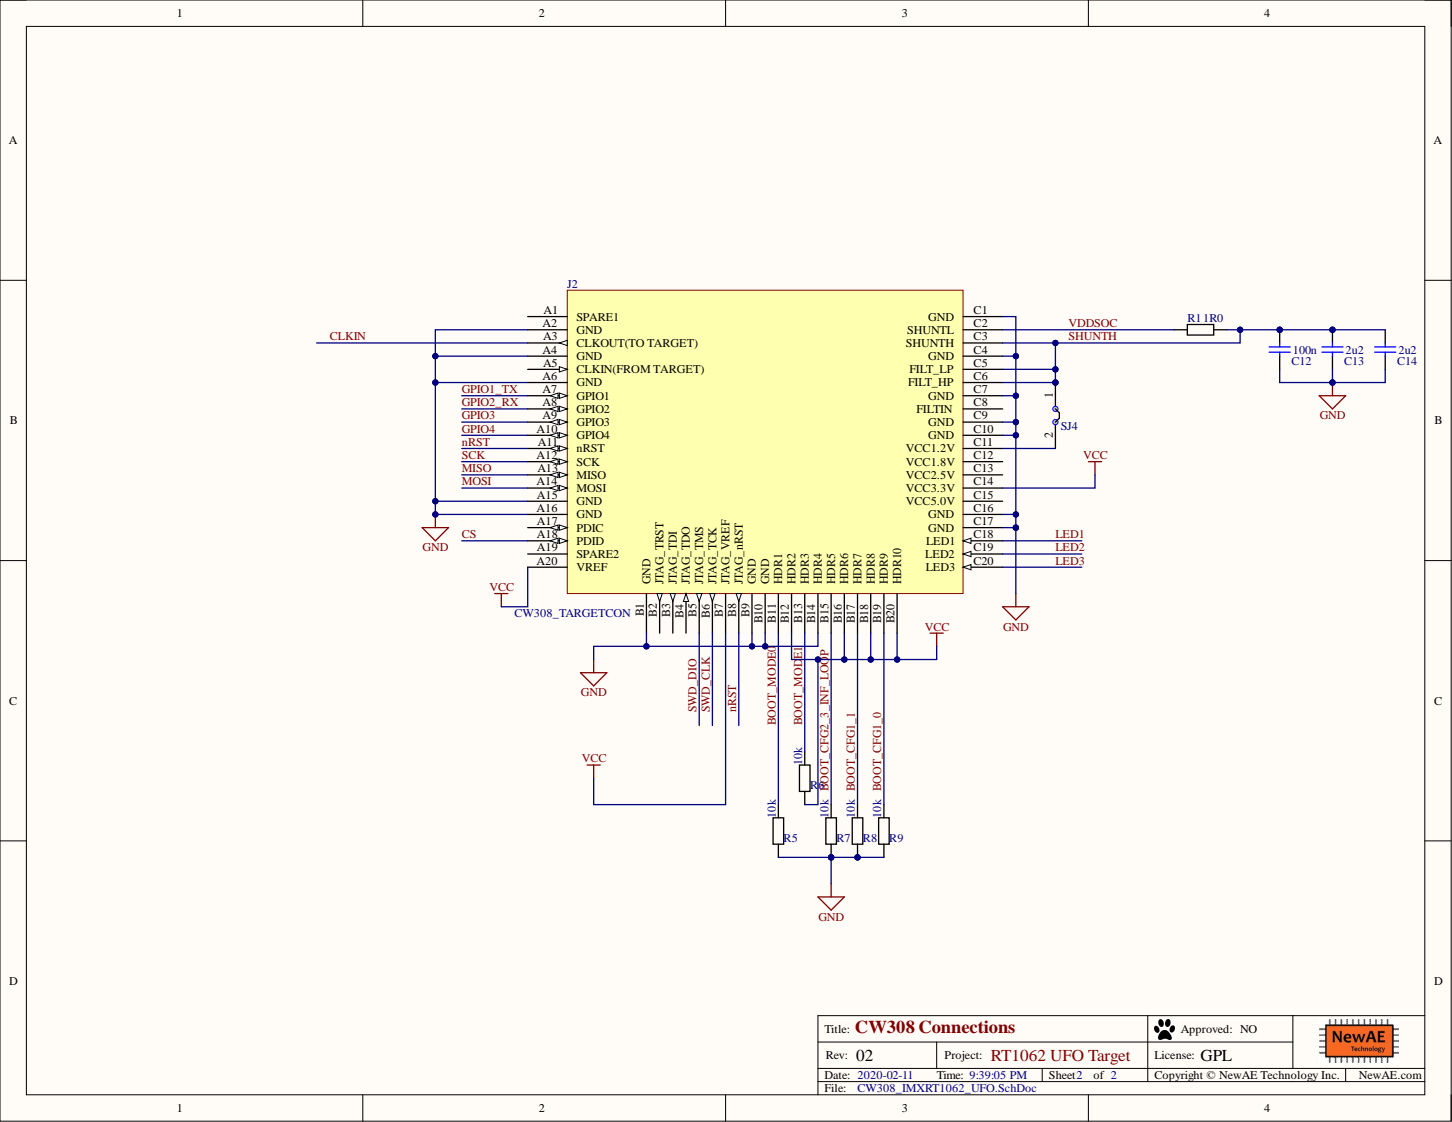
[picture p185: page 2]
