newaetech/chipwhisperer-target-cw308t/CW308T_MPC57/SCH_CW308T_MPC5748G_02.PDF

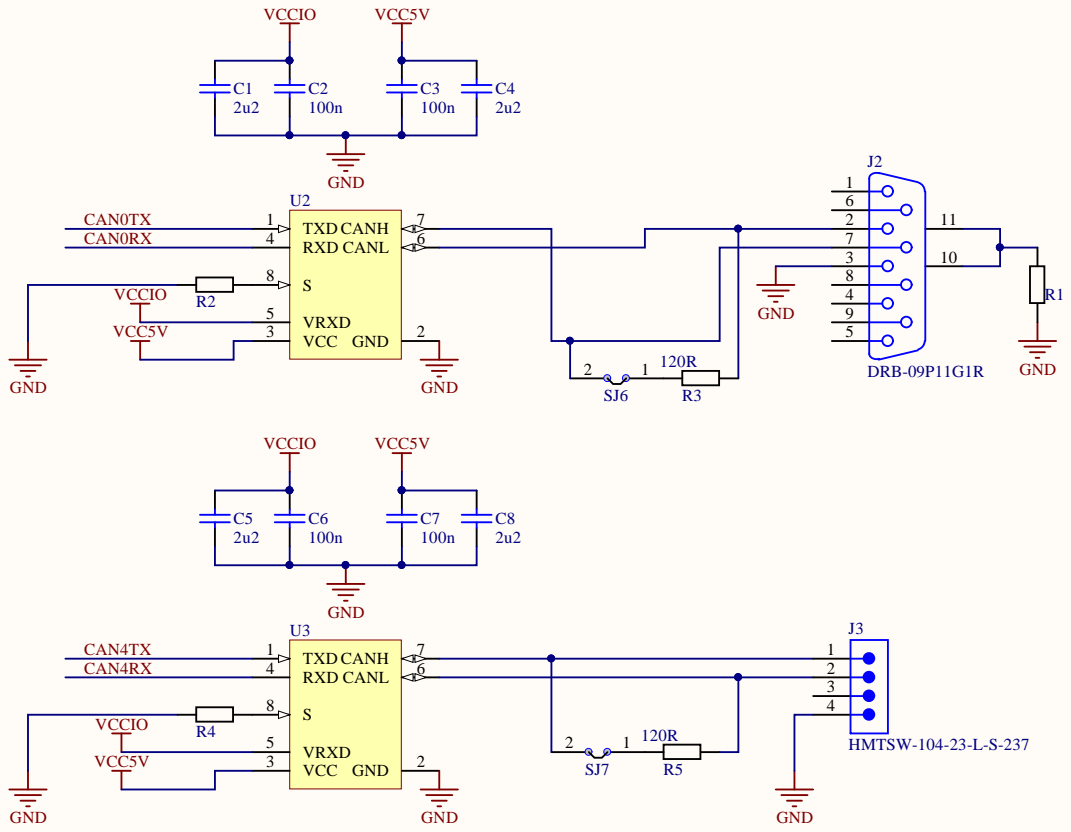
[picture p186: page 1]

CAN Transceivers Title: | Approved: YES

Rev: 02 | Project: CW308T-MPC5748G | License: GPL

Date: 11/03/2017 Time: 6:35:42 PM | Sheet of

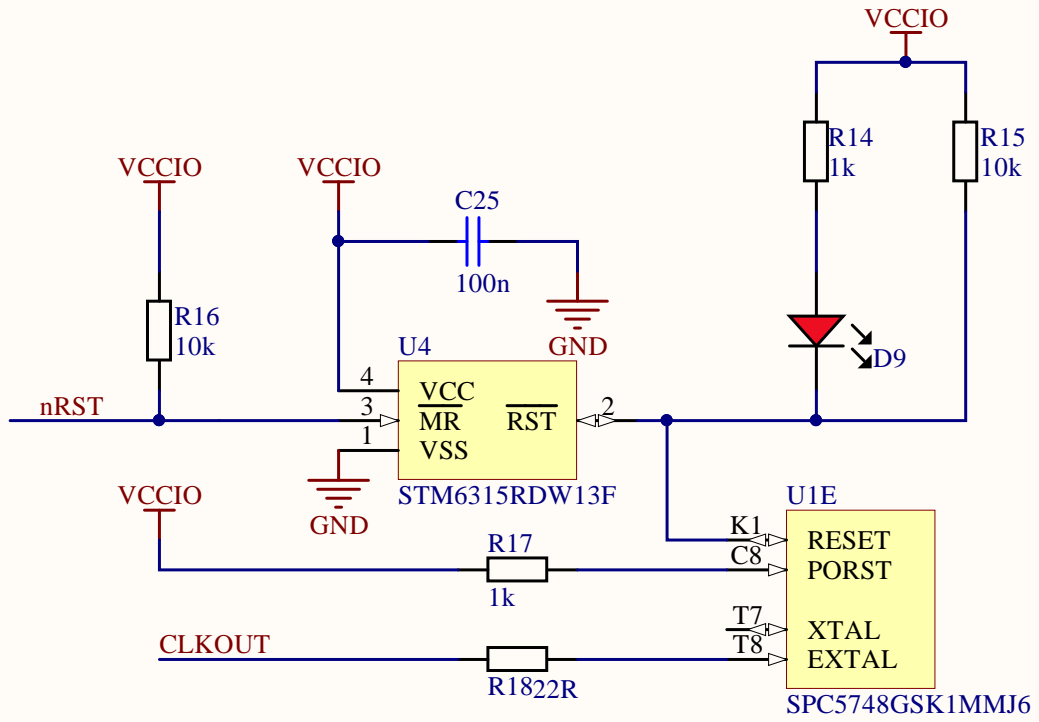
[picture p187: page 2]

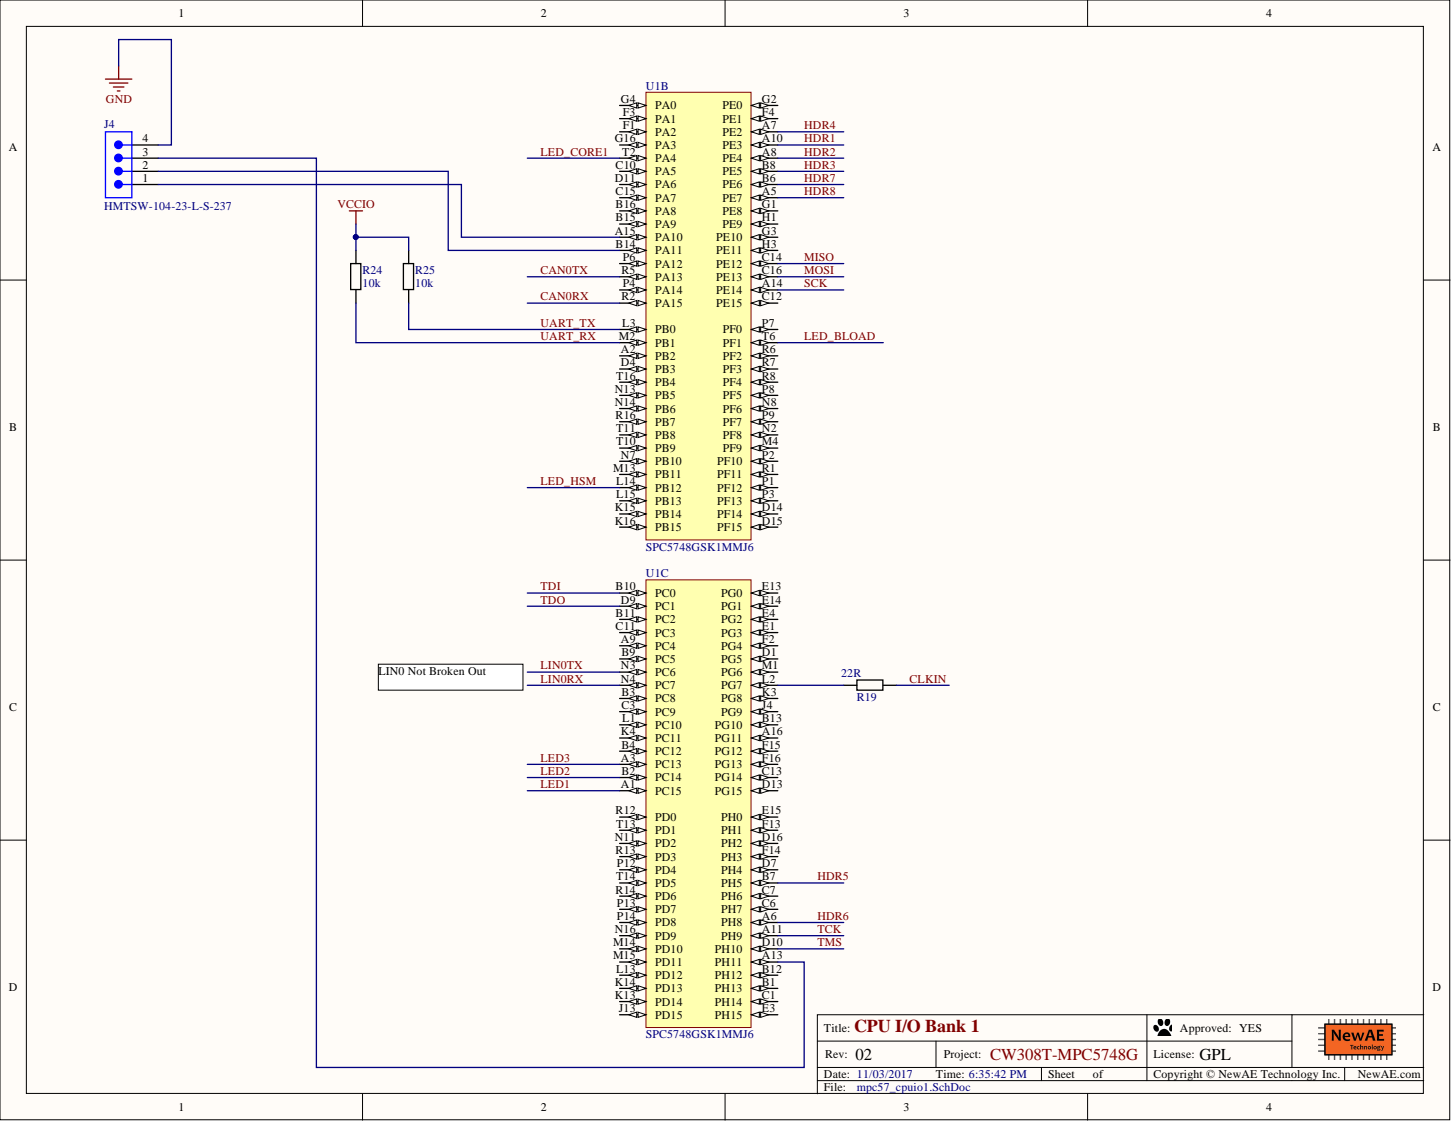
[picture p188: page 3]

T i t le: | A p pro ved : Y E S

Rev : 02 | Project : CW308T-MPC5748G | L icen se: GPL

T ime: : 2 PM | Sheet o f | Co p yri g h t © New A E Tech n | o l o g y Inc.

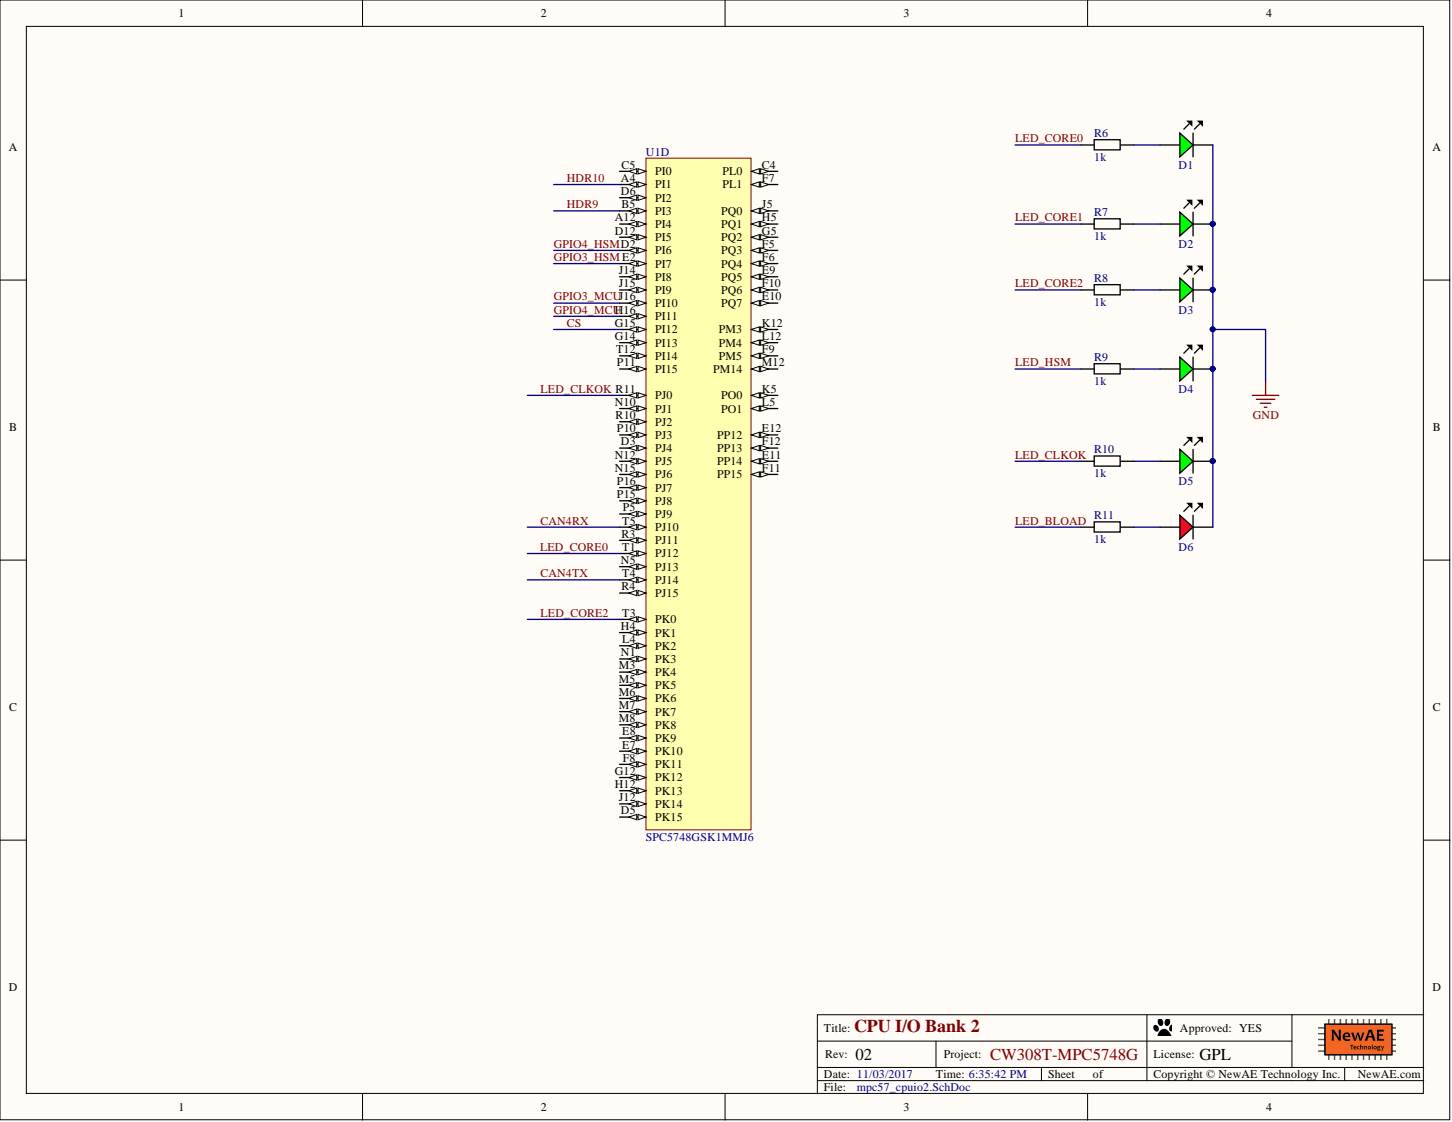
[picture p189: page 4]

T i t le: | A p pro ved : Y E S

Rev : 02 | Project : CW308T-MPC5748G | L icen se: GPL

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

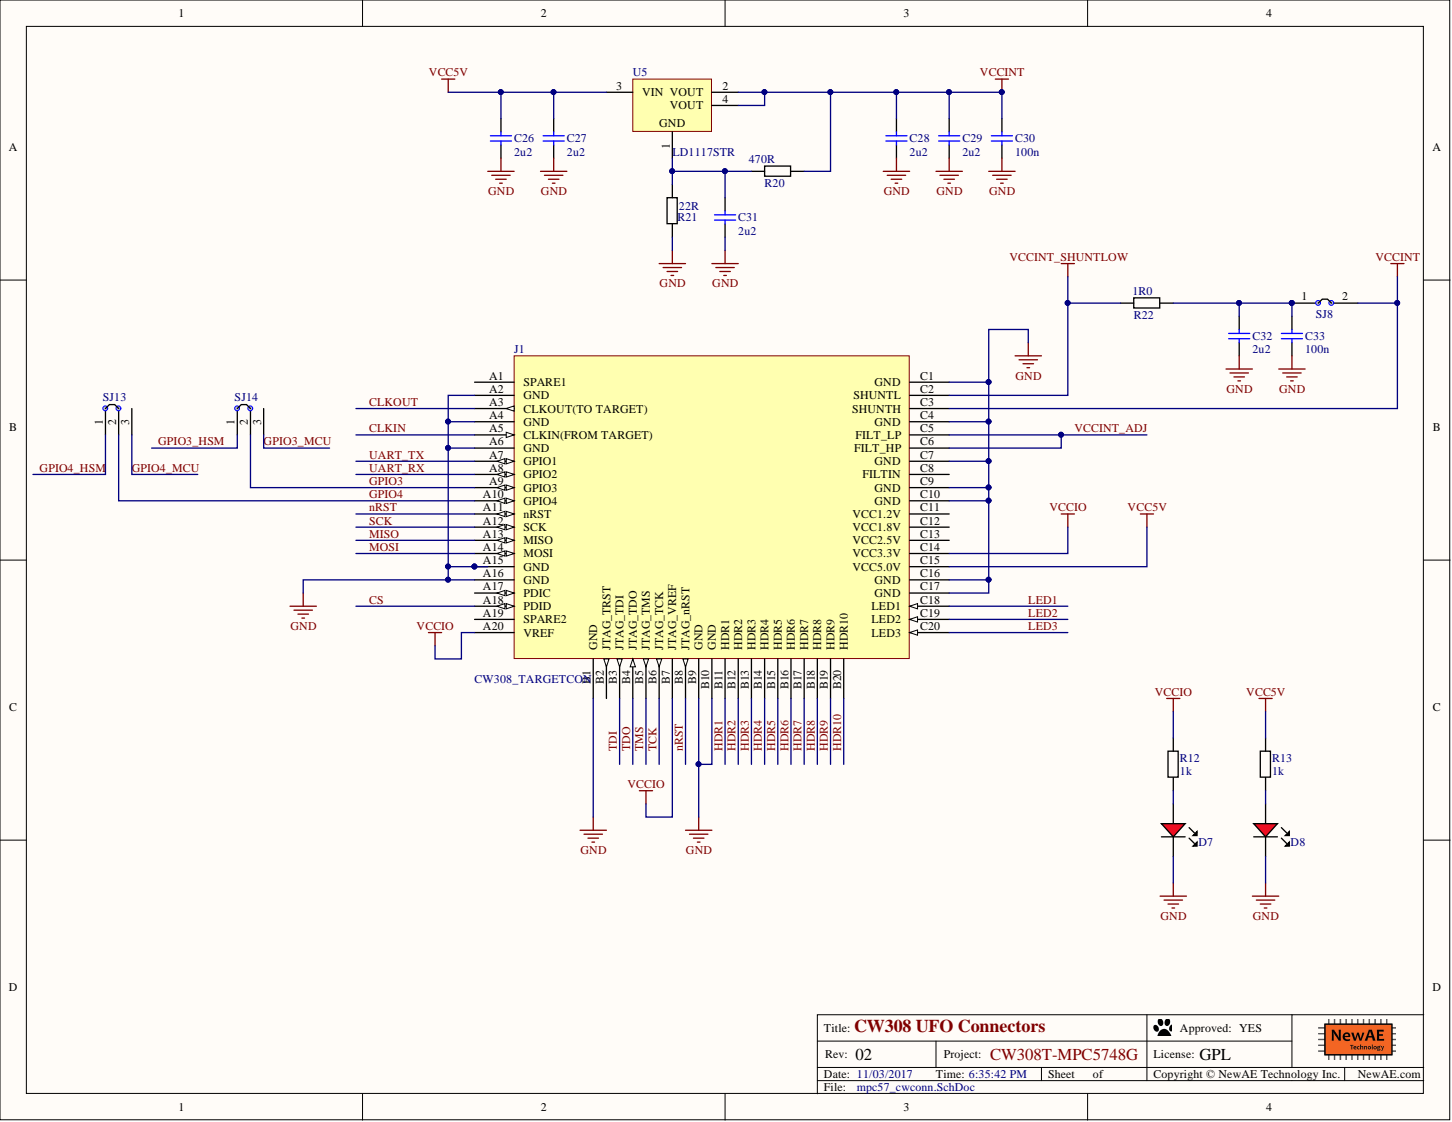
[picture p190: page 5]

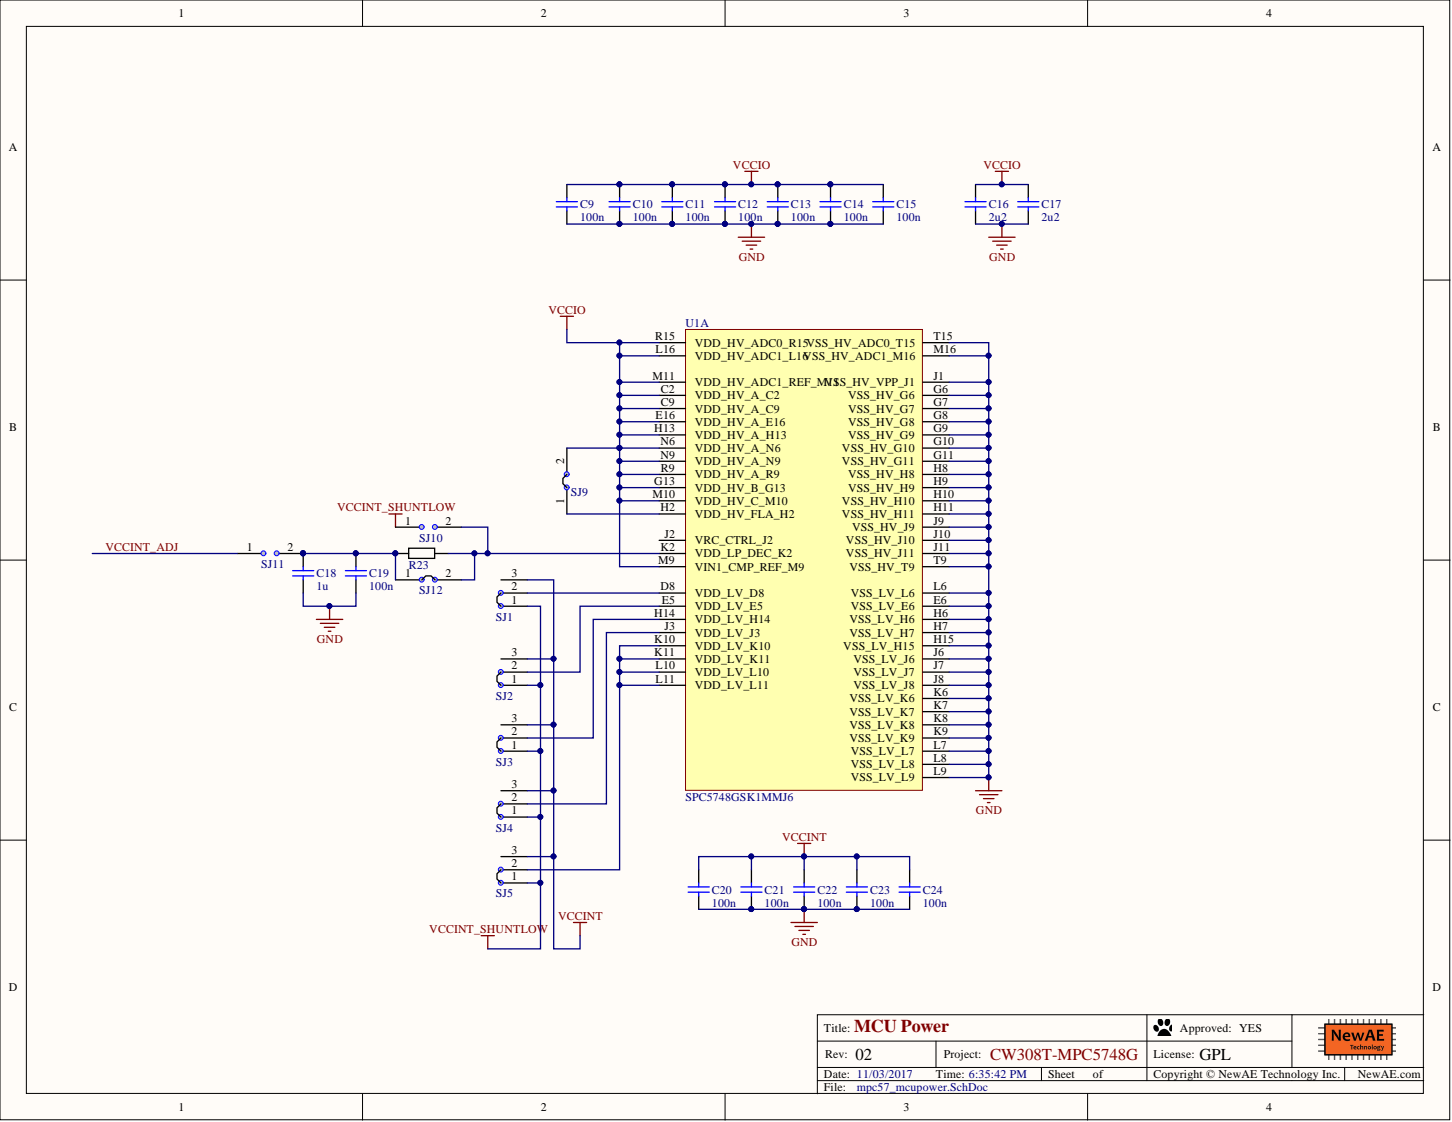
[picture p191: page 6]
